gramaziokohler/coding_architecture_fs26_focus_work/Dokumentation/Group A/Booklet_focuswork_2406 Folder/Links/project2.png

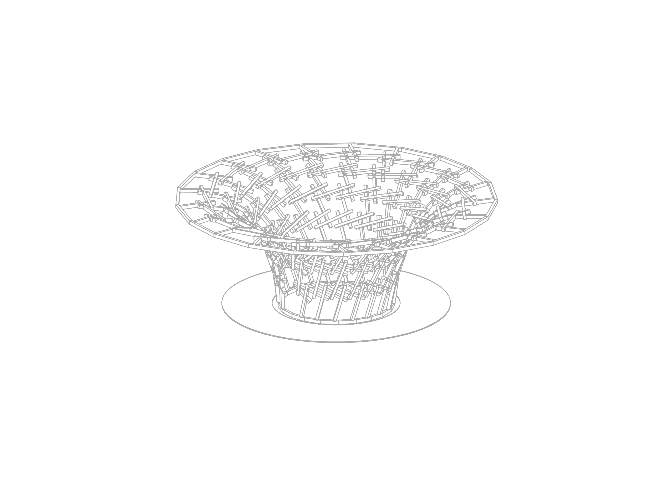
Dokumentation/Group A/Booklet_focuswork_2406 Folder/Links/project2.png
