gramaziokohler/coding_architecture_fs26_focus_work/Dokumentation/Group A/Height.jpg

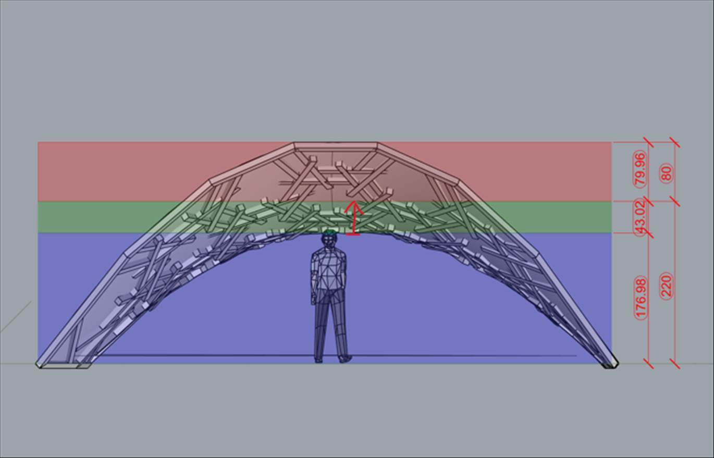
Dokumentation/Group A/Height.jpg
