gramaziokohler/coding_architecture_fs26_focus_work/Dokumentation/Group A/Hexagon Cutting.png

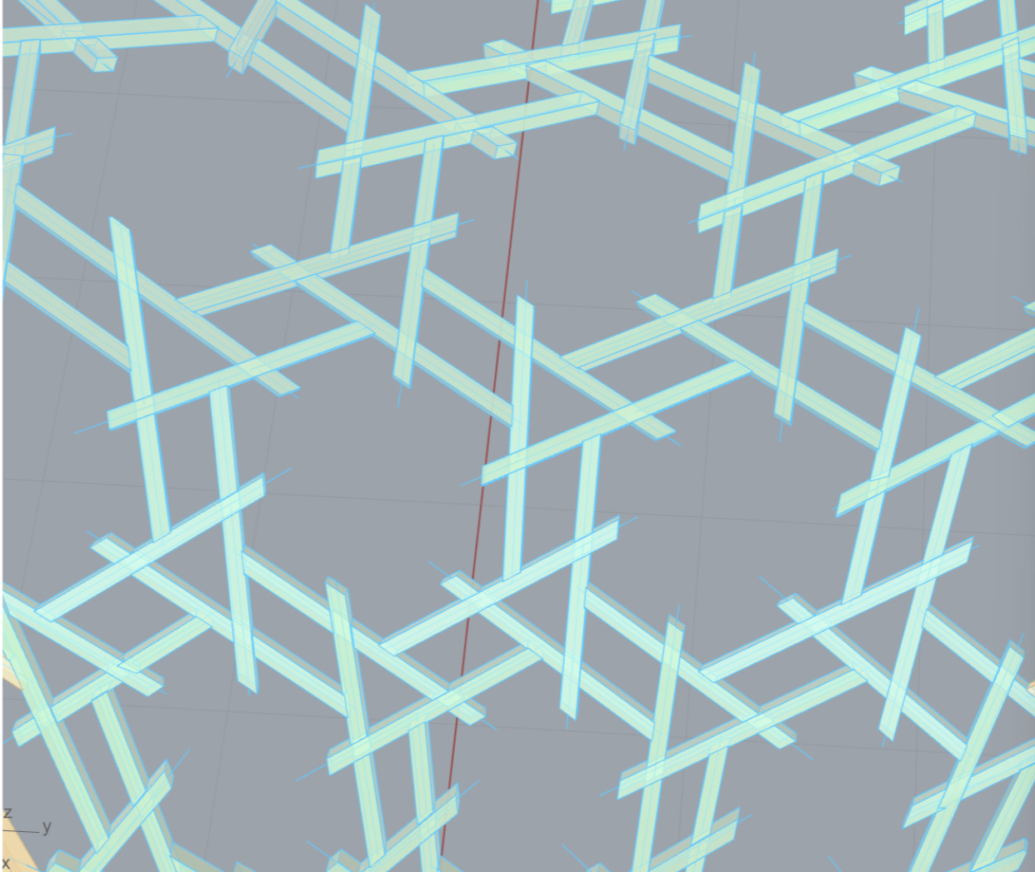
Dokumentation/Group A/Hexagon Cutting.png
