gramaziokohler/coding_architecture_fs26_focus_work/Dokumentation/Group A/Structure_Analysis.png

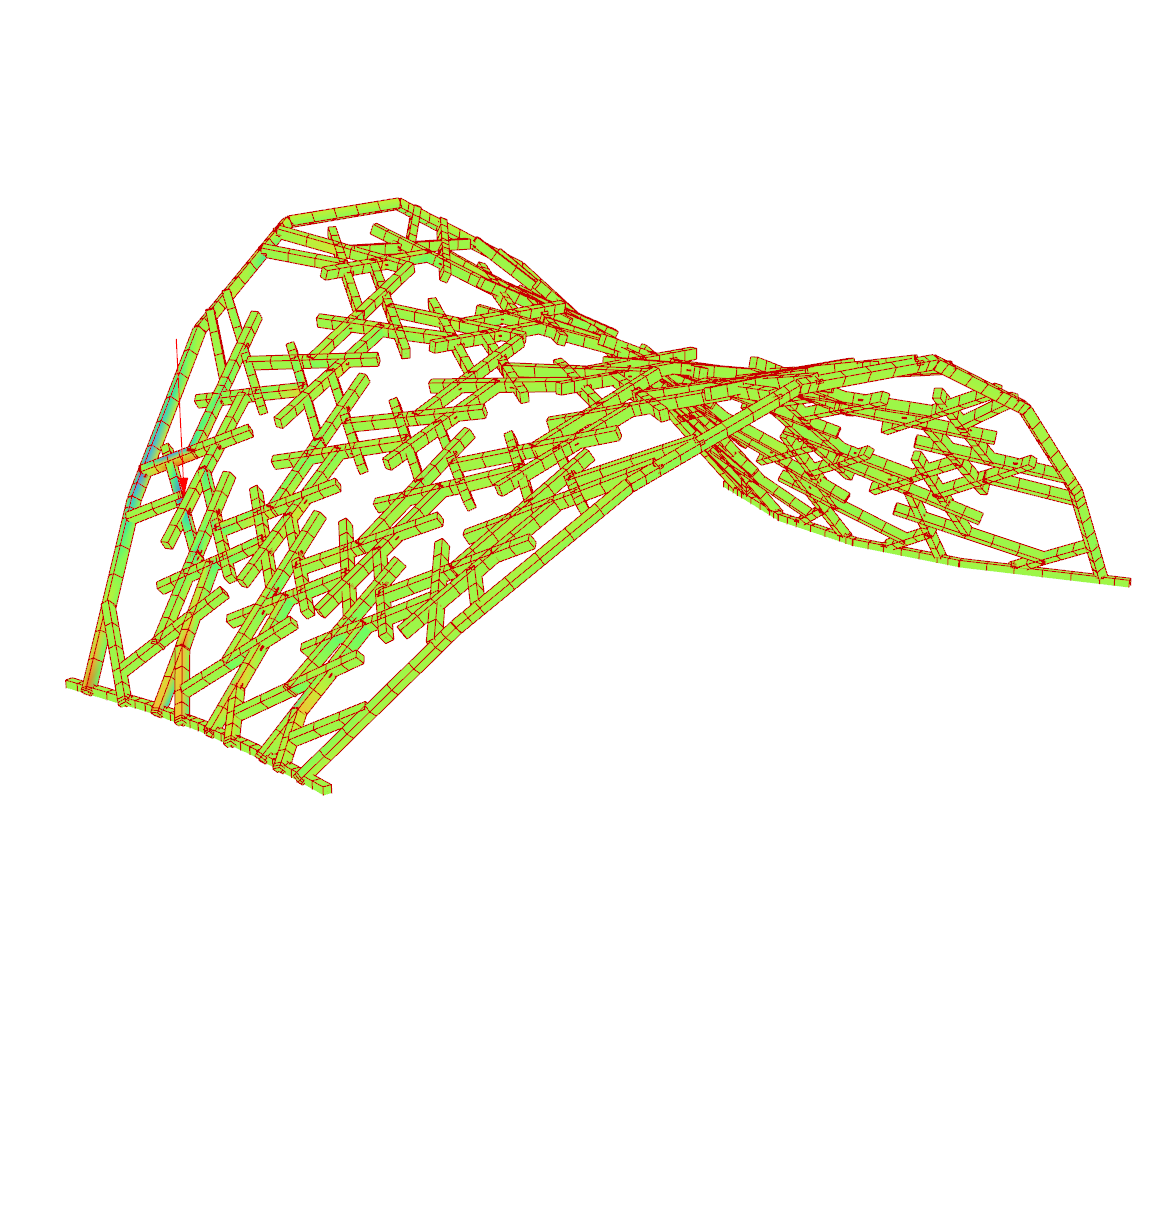
Dokumentation/Group A/Structure_Analysis.png
