gramaziokohler/coding_architecture_fs26_focus_work/Dokumentation/Group B/Screw_processing_2.png

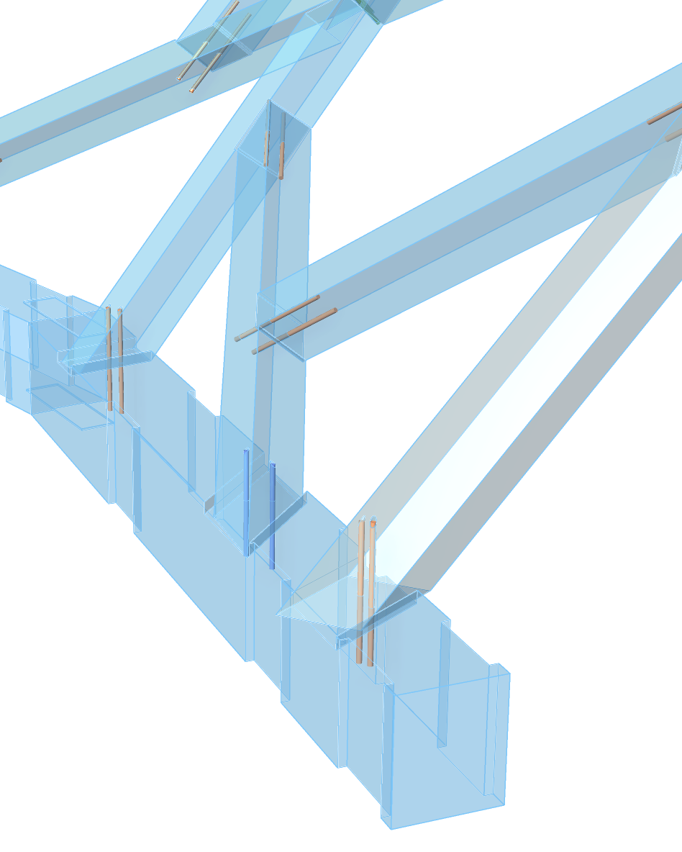
Dokumentation/Group B/Screw_processing_2.png
