gramaziokohler/coding_architecture_fs26_focus_work/Dokumentation/Group B/Screw_processing_6.png

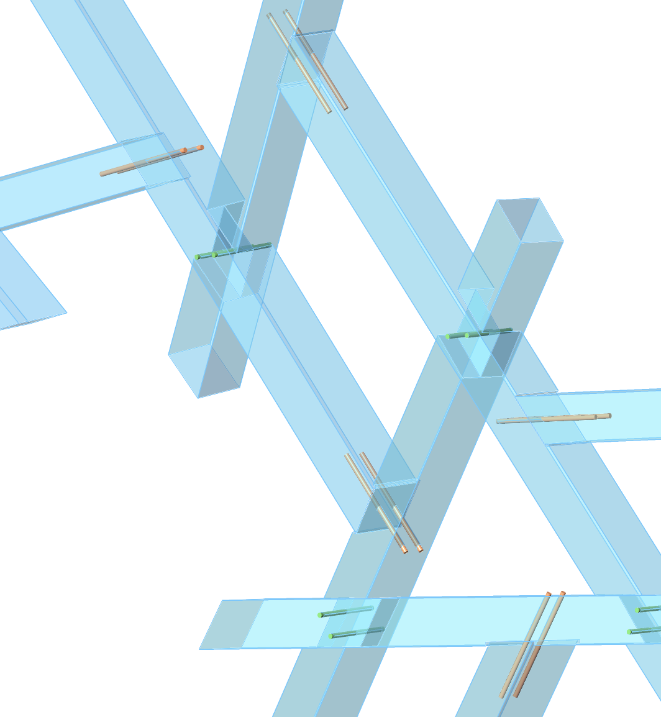
Dokumentation/Group B/Screw_processing_6.png
