gramaziokohler/coding_architecture_fs26_focus_work/Dokumentation/Group B/Screw_processing_fail_2.jpeg

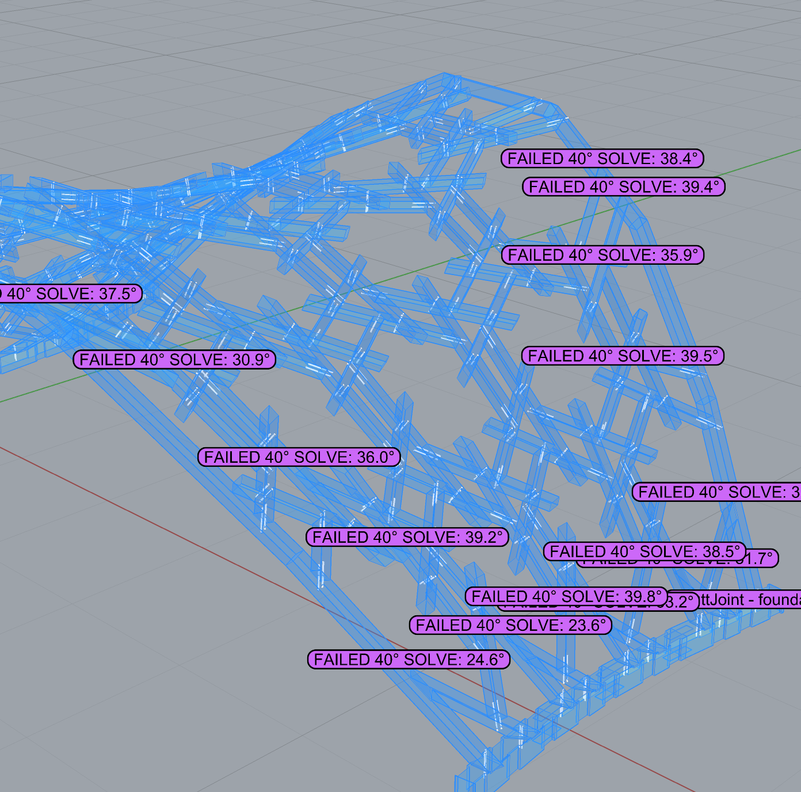
Dokumentation/Group B/Screw_processing_fail_2.jpeg
