gramaziokohler/coding_architecture_fs26_focus_work/Dokumentation/Group B/sketches_joints_2.jpeg

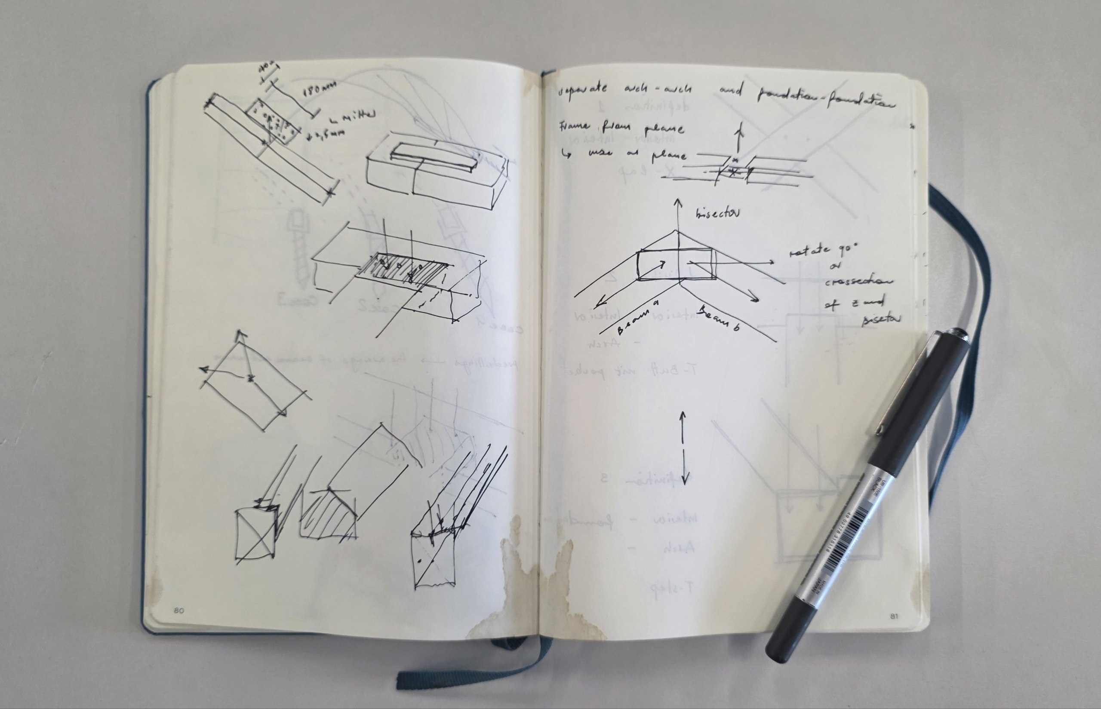
Dokumentation/Group B/sketches_joints_2.jpeg
