gramaziokohler/coding_architecture_fs26_focus_work/working_directory/group_c/bicchieri che brindano.png

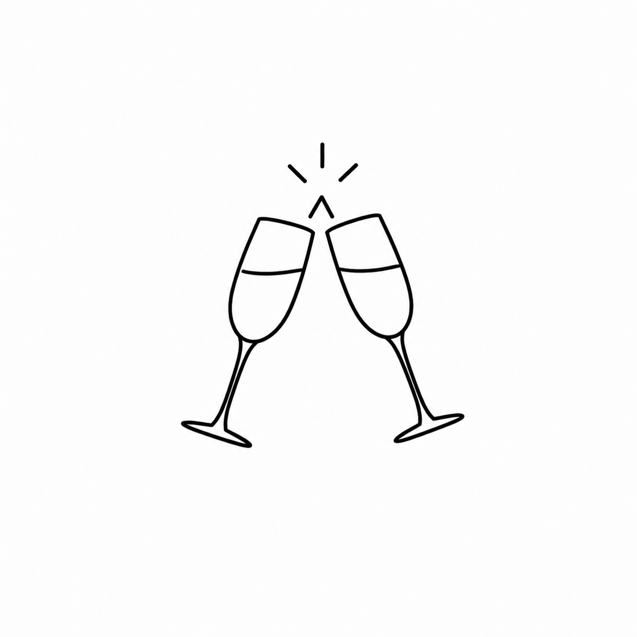
working_directory/group_c/bicchieri che brindano.png
