gramaziokohler/coding_architecture_fs26_focus_work/working_directory/group_d/Assemply_front.png

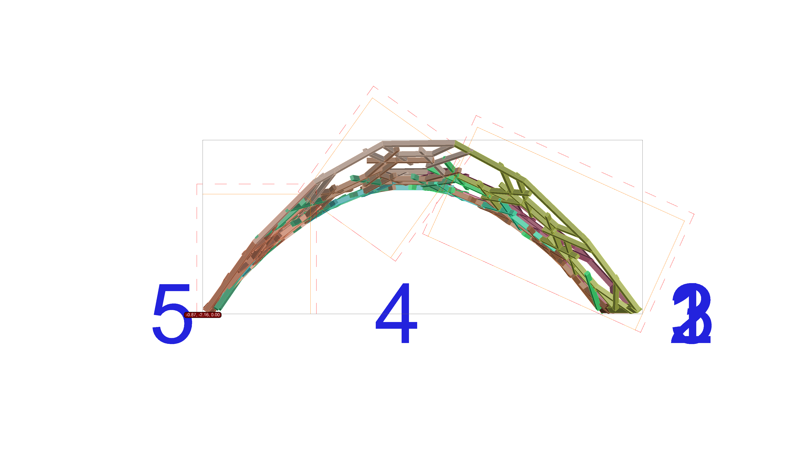
working_directory/group_d/Assemply_front.png
