gramaziokohler/coding_architecture_fs26_focus_work/working_directory/group_d/GardenWires_Diagram.png

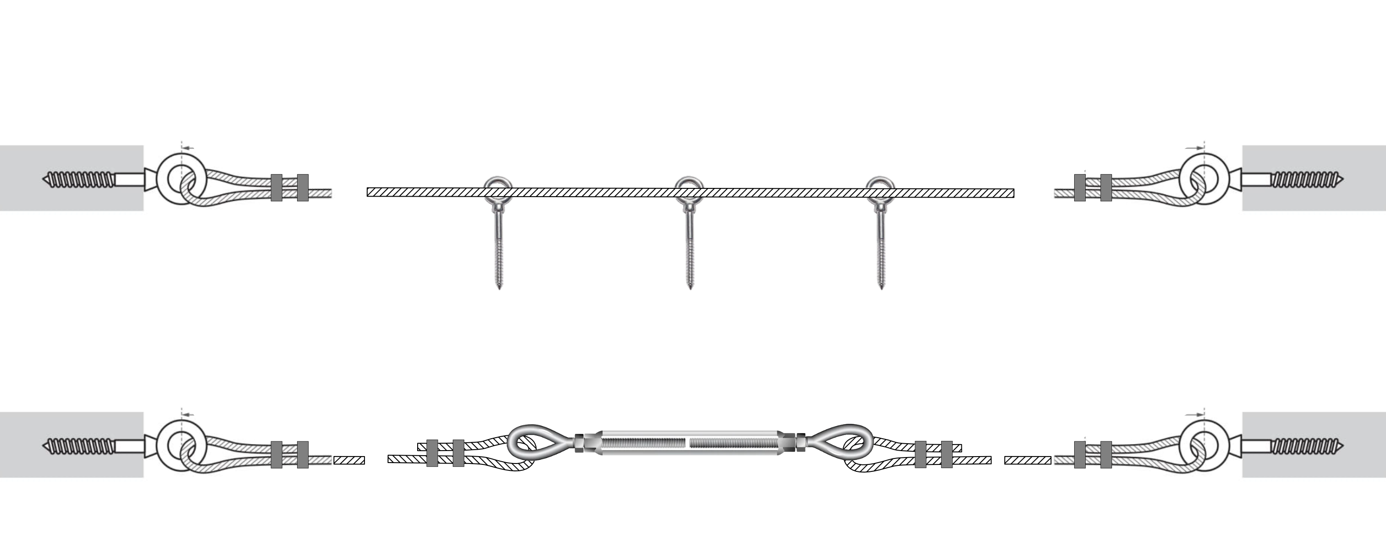
working_directory/group_d/GardenWires_Diagram.png
