gramaziokohler/coding_architecture_fs26_focus_work/working_directory/group_d/STRUCTURE_WITH_NUMBERS_embedded_files/max. 3330.png

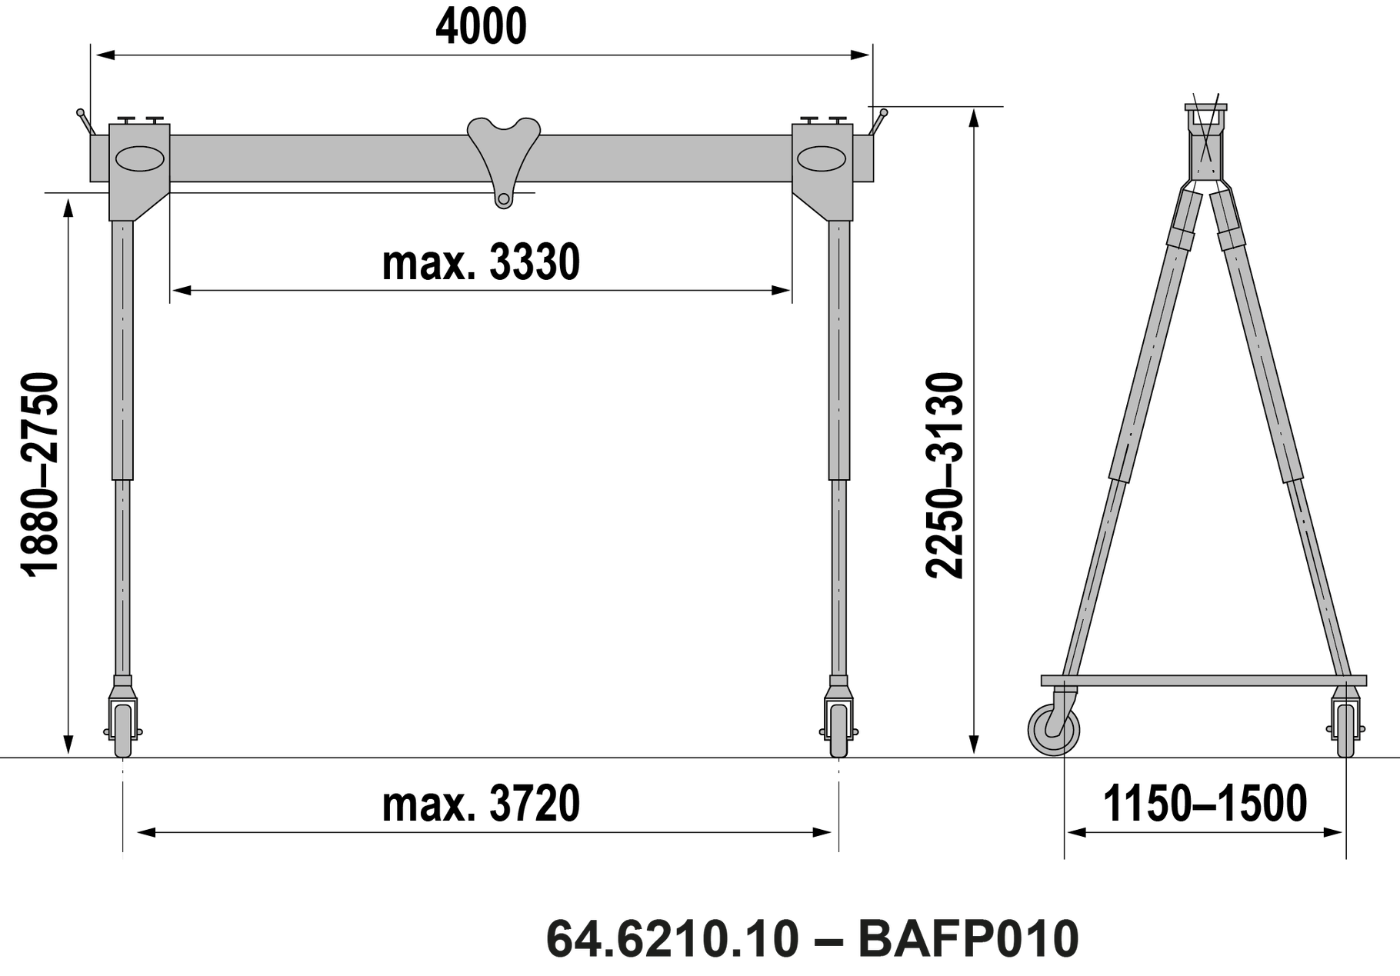
working_directory/group_d/STRUCTURE_WITH_NUMBERS_embedded_files/max. 3330.png
