gramaziokohler/coding_architecture_fs26_focus_work/web_data/beam/a22/a22.stl

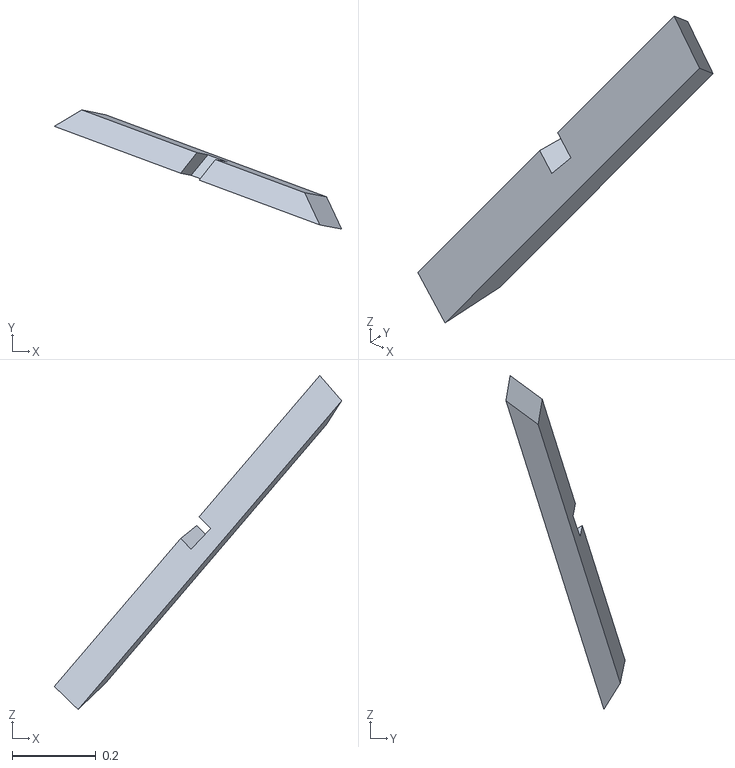
[picture p97: CAD file, 2026-06-04]
web_data/beam/a22/a22.stl
0.687 x 0.285 x 0.798
