gramaziokohler/coding_architecture_fs26_focus_work/web_data/beam/a23/a23.stl

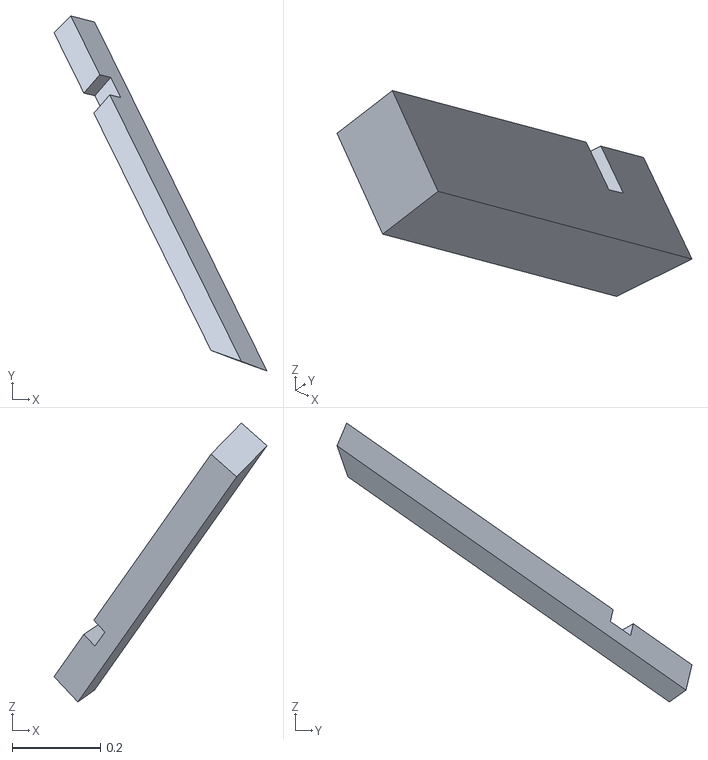
[picture p98: CAD file, 2026-06-04]
web_data/beam/a23/a23.stl
0.484 x 0.806 x 0.633
