gramaziokohler/coding_architecture_fs26_focus_work/web_data/beam/a24/a24.stl

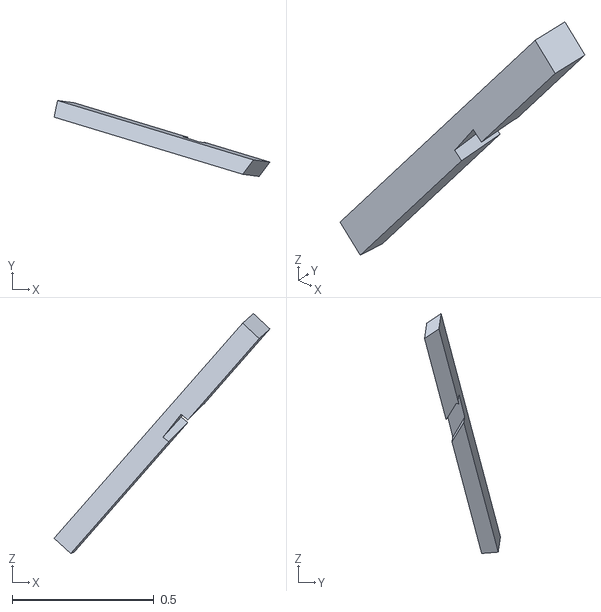
[picture p99: CAD file, 2026-06-04]
web_data/beam/a24/a24.stl
0.761 x 0.268 x 0.846
