gramaziokohler/coding_architecture_fs26_focus_work/web_data/beam/a25/a25.stl

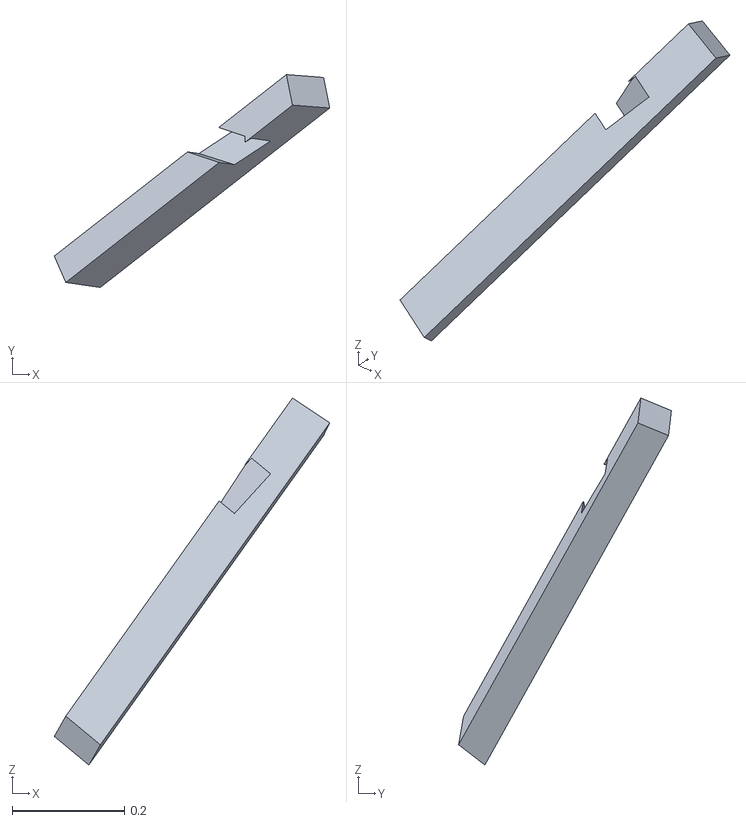
[picture p100: CAD file, 2026-06-04]
web_data/beam/a25/a25.stl
0.491 x 0.38 x 0.654
