gramaziokohler/coding_architecture_fs26_focus_work/web_data/beam/a26/a26.stl

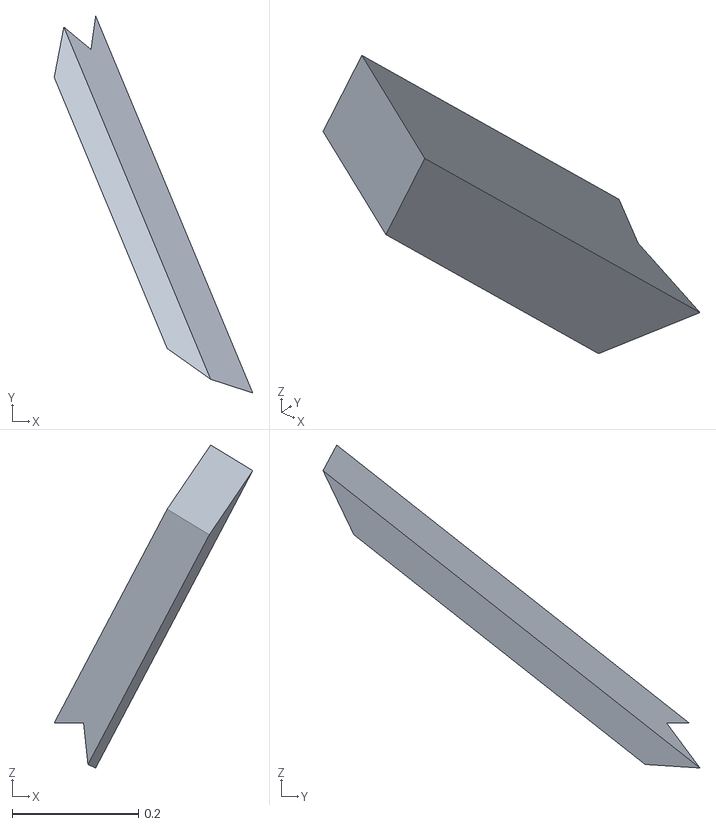
[picture p101: CAD file, 2026-06-04]
web_data/beam/a26/a26.stl
0.315 x 0.597 x 0.512
