gramaziokohler/coding_architecture_fs26_focus_work/web_data/beam/a27/a27.stl

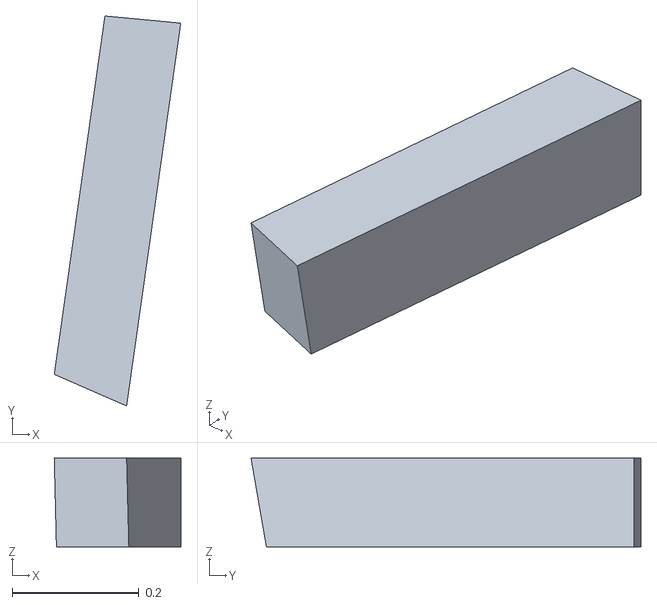
[picture p102: CAD file, 2026-06-04]
web_data/beam/a27/a27.stl
0.2 x 0.615 x 0.14
