gramaziokohler/coding_architecture_fs26_focus_work/web_data/beam/a28/a28.stl

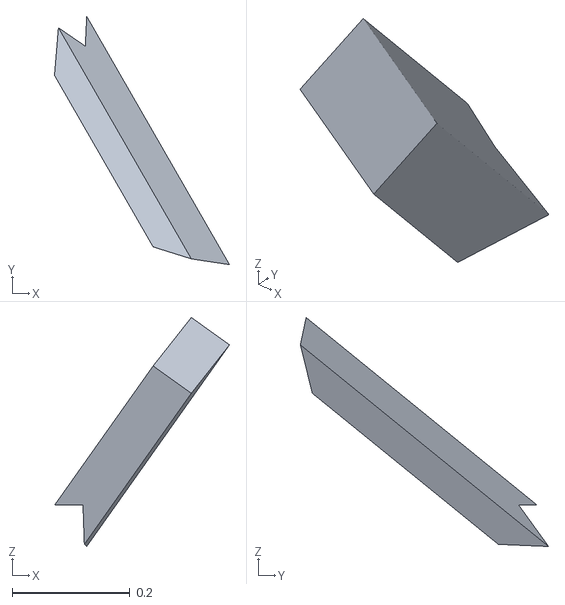
[picture p103: CAD file, 2026-06-04]
web_data/beam/a28/a28.stl
0.297 x 0.421 x 0.389
