gramaziokohler/coding_architecture_fs26_focus_work/web_data/beam/a29/a29.stl

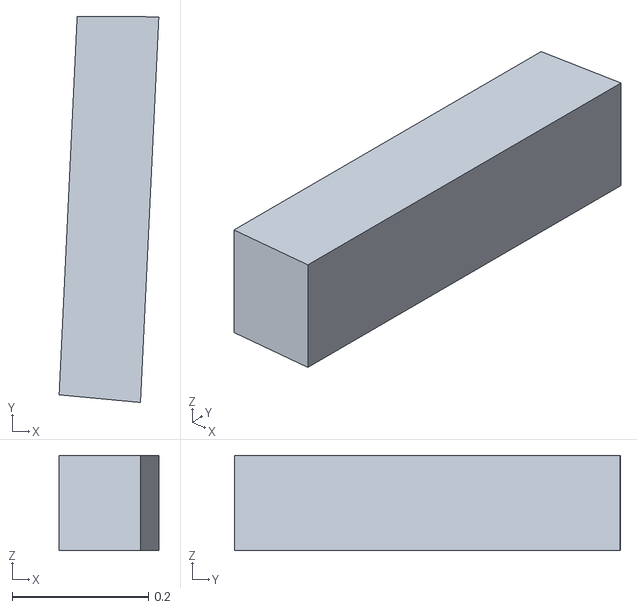
[picture p104: CAD file, 2026-06-04]
web_data/beam/a29/a29.stl
0.147 x 0.567 x 0.14
