gramaziokohler/coding_architecture_fs26_focus_work/web_data/beam/a3/a3.stl

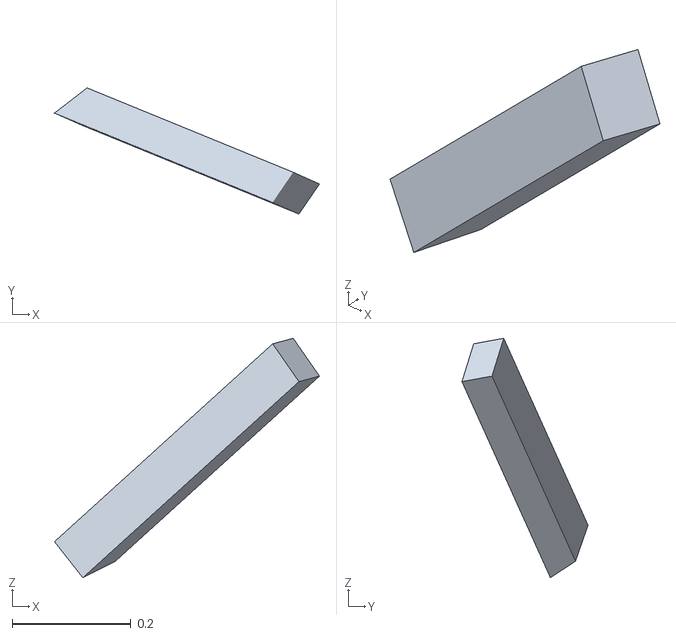
[picture p105: CAD file, 2026-06-04]
web_data/beam/a3/a3.stl
0.447 x 0.213 x 0.403
