gramaziokohler/coding_architecture_fs26_focus_work/web_data/beam/a30/a30.stl

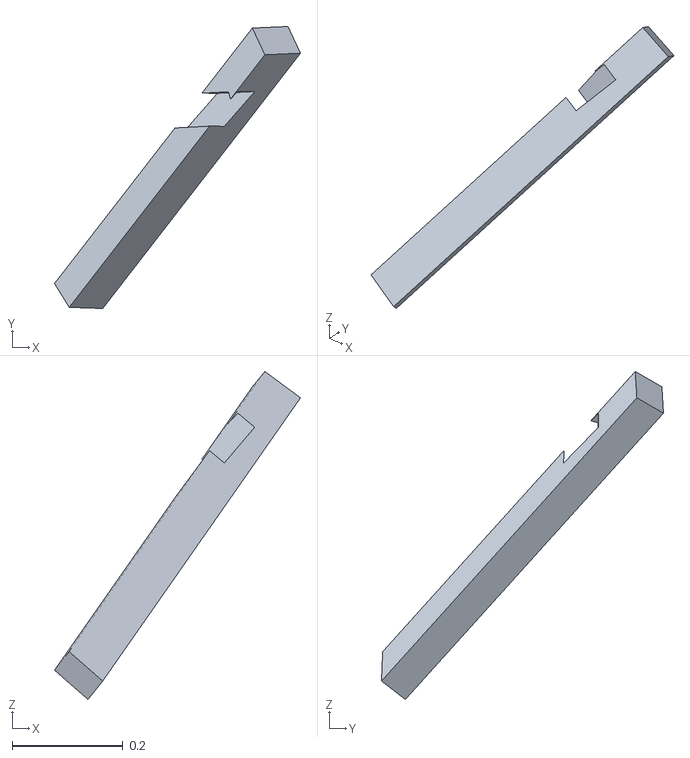
[picture p106: CAD file, 2026-06-04]
web_data/beam/a30/a30.stl
0.444 x 0.509 x 0.592
