gramaziokohler/coding_architecture_fs26_focus_work/web_data/beam/a31/a31.stl

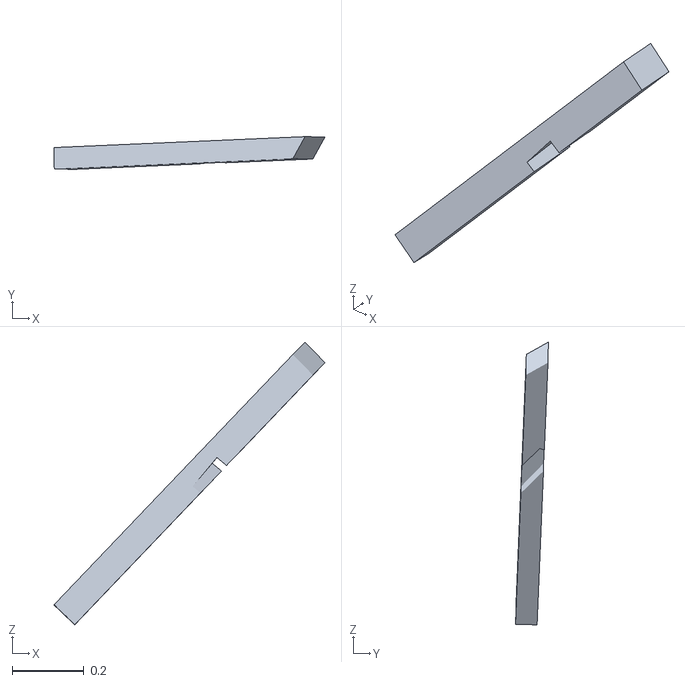
[picture p107: CAD file, 2026-06-04]
web_data/beam/a31/a31.stl
0.756 x 0.0914 x 0.789
