gramaziokohler/coding_architecture_fs26_focus_work/web_data/beam/a32/a32.stl

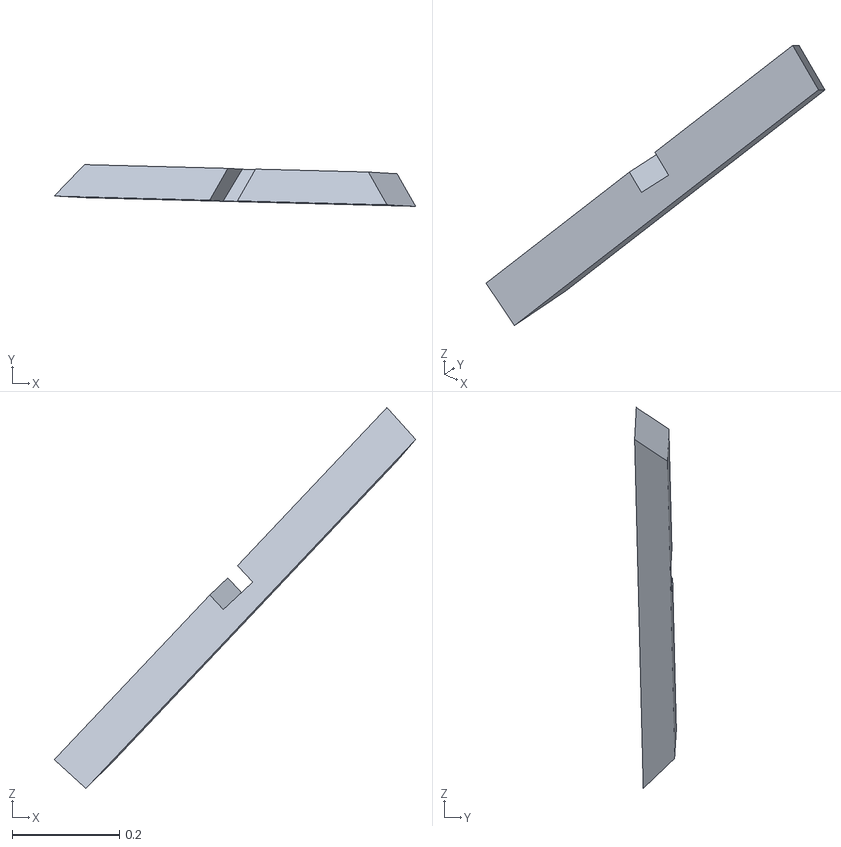
[picture p108: CAD file, 2026-06-04]
web_data/beam/a32/a32.stl
0.674 x 0.078 x 0.711
