gramaziokohler/coding_architecture_fs26_focus_work/web_data/beam/a33/a33.stl

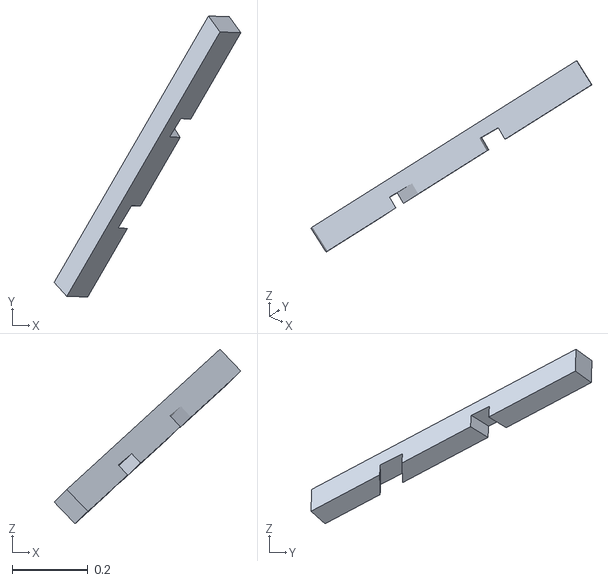
[picture p109: CAD file, 2026-06-04]
web_data/beam/a33/a33.stl
0.494 x 0.743 x 0.462
