gramaziokohler/coding_architecture_fs26_focus_work/web_data/beam/a34/a34.stl

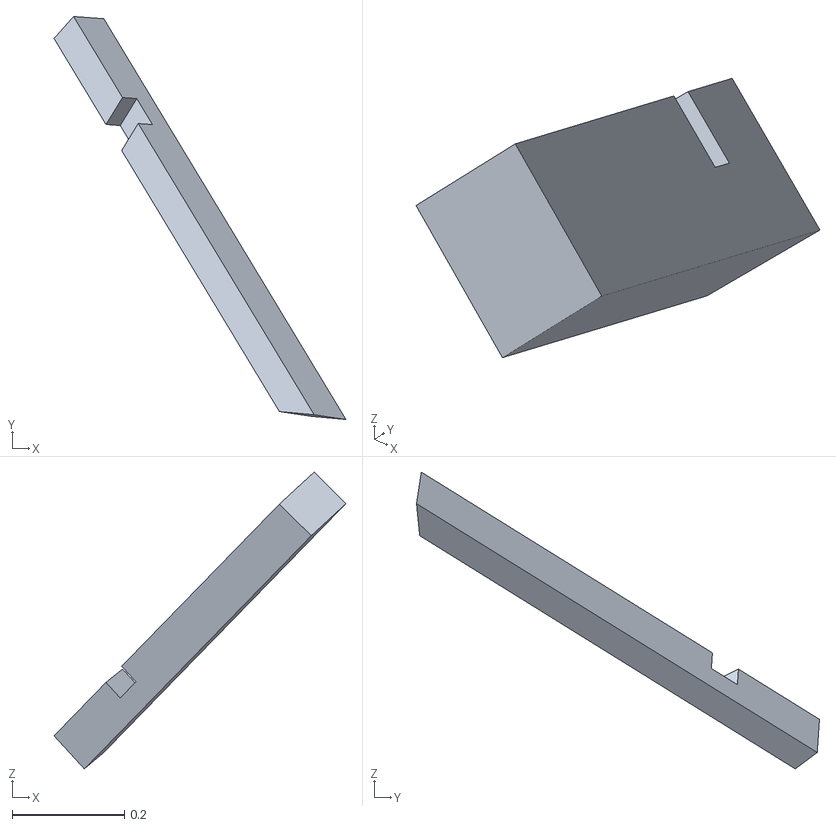
[picture p110: CAD file, 2026-06-04]
web_data/beam/a34/a34.stl
0.52 x 0.717 x 0.528
