gramaziokohler/coding_architecture_fs26_focus_work/web_data/beam/a35/a35.stl

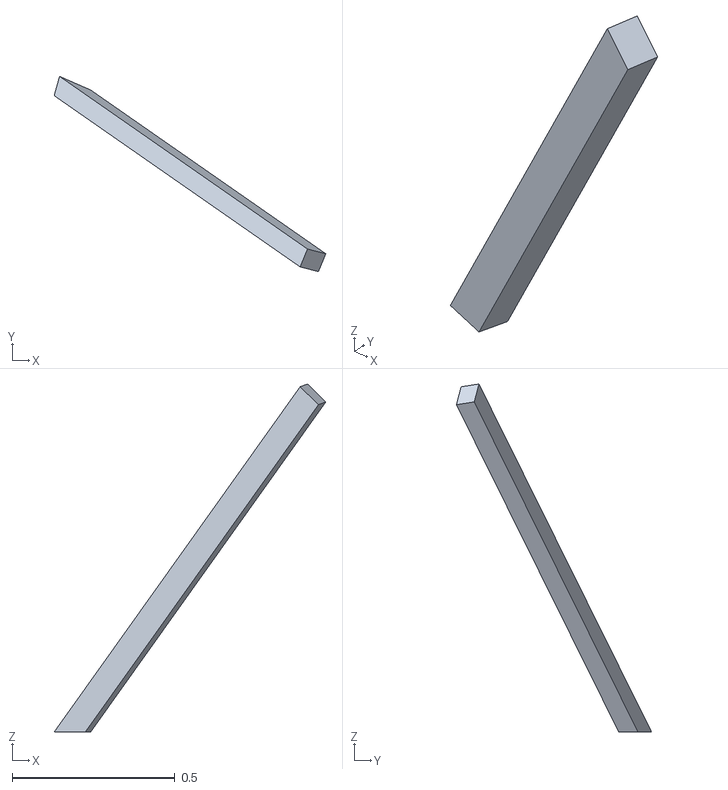
[picture p111: CAD file, 2026-06-04]
web_data/beam/a35/a35.stl
0.835 x 0.6 x 1.07
