gramaziokohler/coding_architecture_fs26_focus_work/web_data/beam/a36/a36.stl

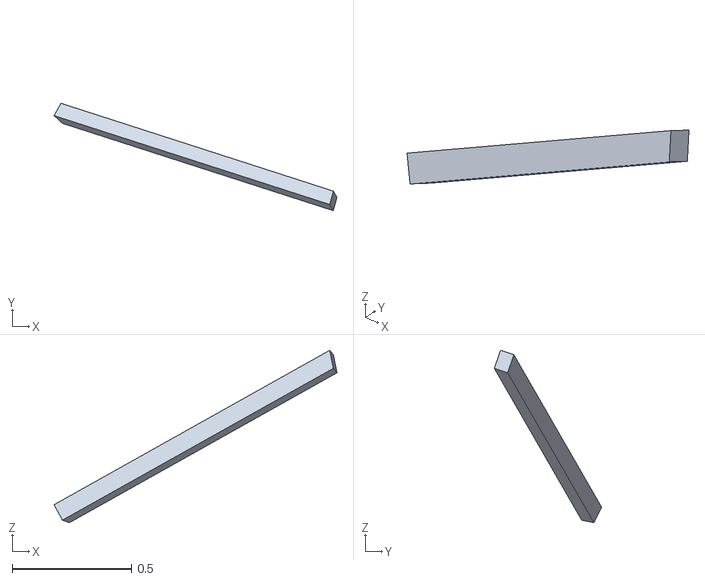
[picture p112: CAD file, 2026-06-04]
web_data/beam/a36/a36.stl
1.19 x 0.45 x 0.723
