gramaziokohler/coding_architecture_fs26_focus_work/web_data/beam/a4/a4.stl

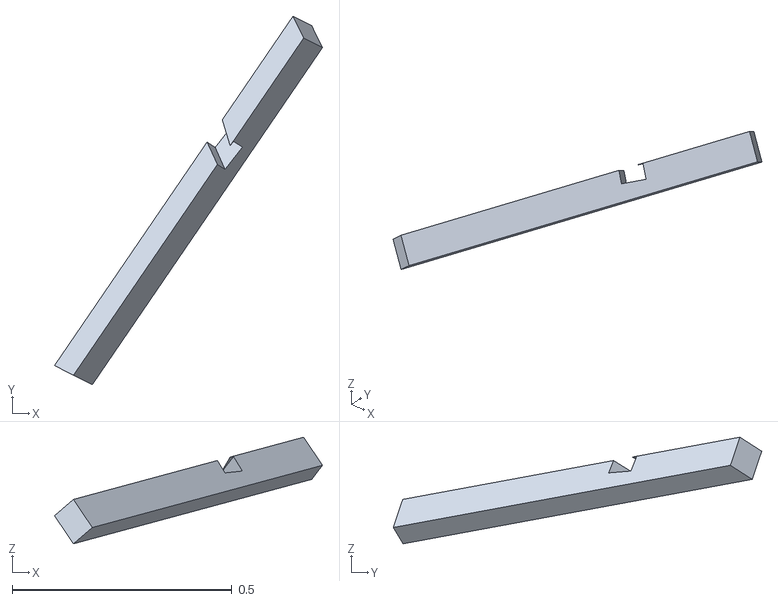
[picture p113: CAD file, 2026-06-04]
web_data/beam/a4/a4.stl
0.61 x 0.839 x 0.243
