gramaziokohler/coding_architecture_fs26_focus_work/web_data/beam/a5/a5.stl

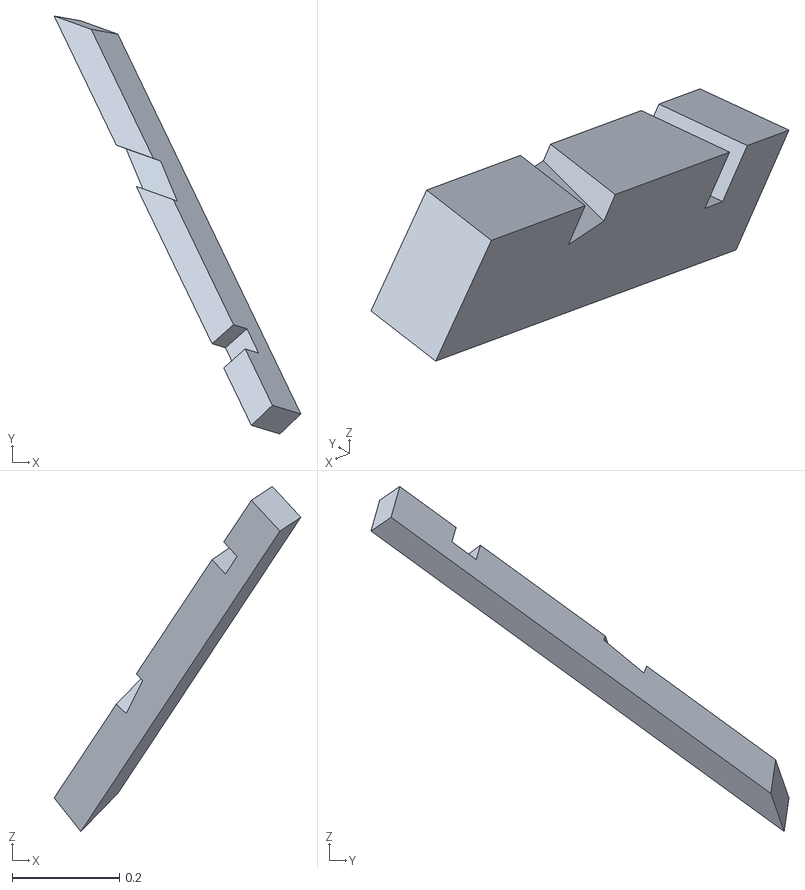
[picture p114: CAD file, 2026-06-04]
web_data/beam/a5/a5.stl
0.461 x 0.781 x 0.644
