gramaziokohler/coding_architecture_fs26_focus_work/web_data/beam/a6/a6.stl

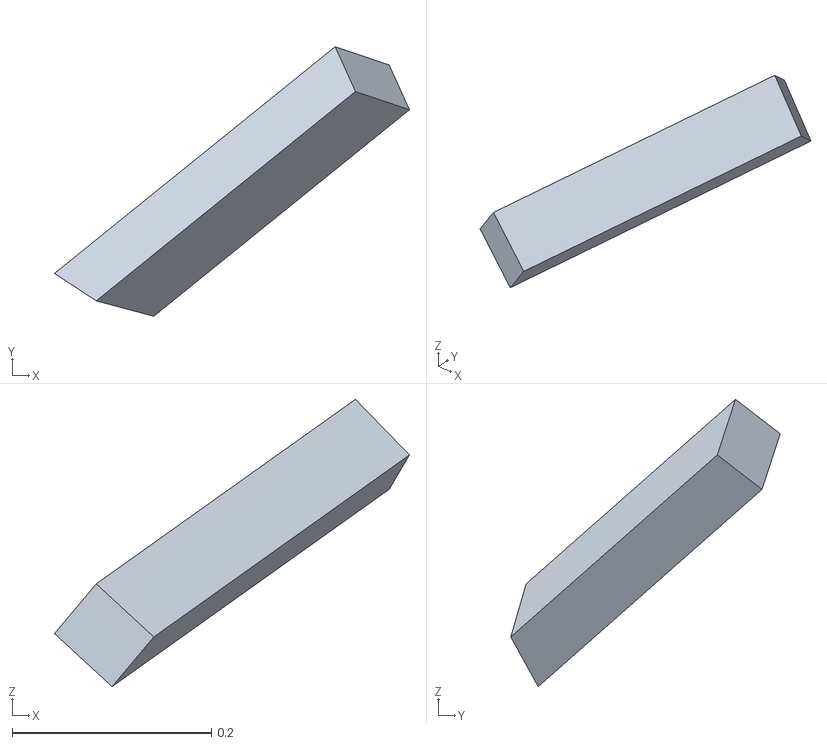
[picture p115: CAD file, 2026-06-04]
web_data/beam/a6/a6.stl
0.357 x 0.271 x 0.289
