gramaziokohler/coding_architecture_fs26_focus_work/web_data/beam/a7/a7.stl

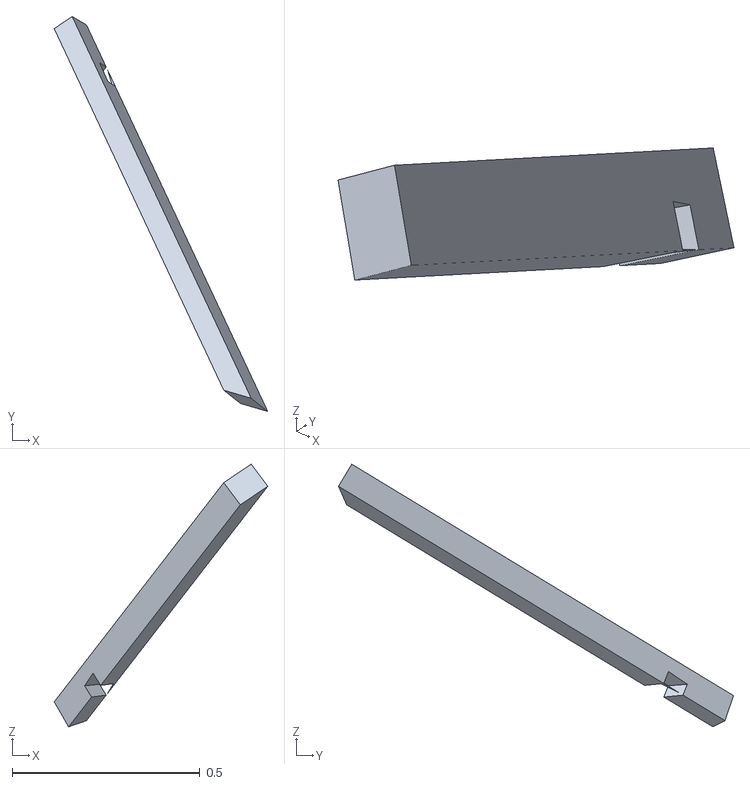
[picture p116: CAD file, 2026-06-04]
web_data/beam/a7/a7.stl
0.568 x 1.05 x 0.699
