gramaziokohler/coding_architecture_fs26_focus_work/web_data/beam/a8/a8.stl

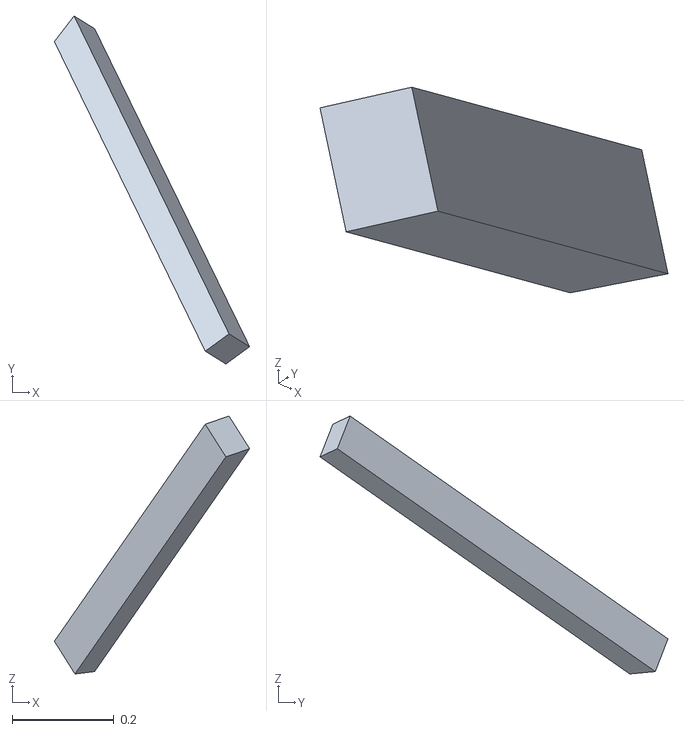
[picture p117: CAD file, 2026-06-04]
web_data/beam/a8/a8.stl
0.384 x 0.684 x 0.507
