gramaziokohler/coding_architecture_fs26_focus_work/web_data/beam/a9/a9.stl

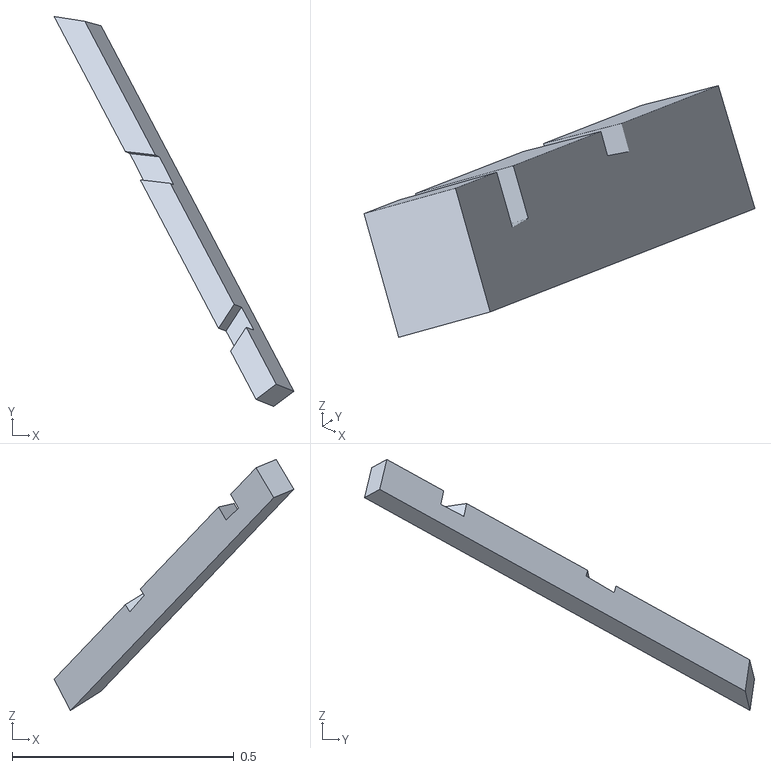
[picture p118: CAD file, 2026-06-04]
web_data/beam/a9/a9.stl
0.541 x 0.88 x 0.567
