gramaziokohler/coding_architecture_fs26_focus_work/web_data/beam/b1/b1.stl

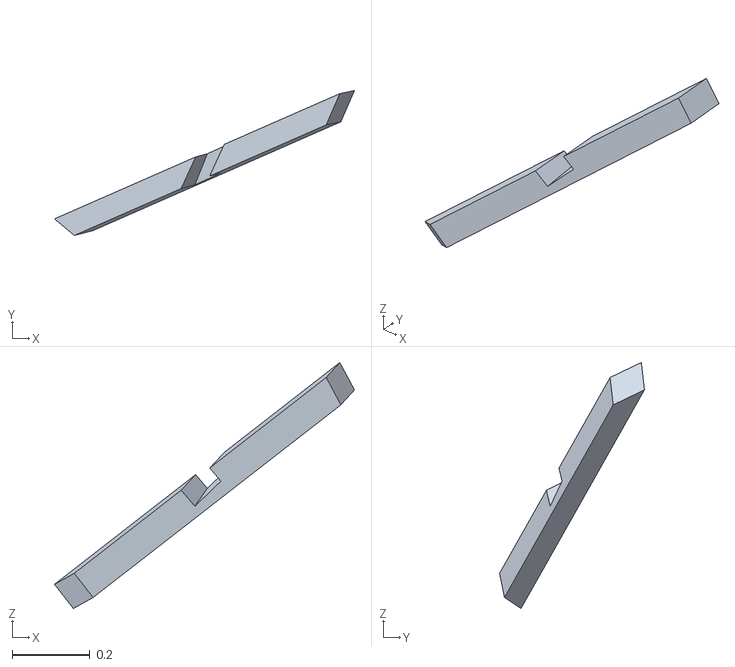
[picture p119: CAD file, 2026-06-04]
web_data/beam/b1/b1.stl
0.774 x 0.374 x 0.635
