gramaziokohler/coding_architecture_fs26_focus_work/web_data/beam/b10/b10.stl

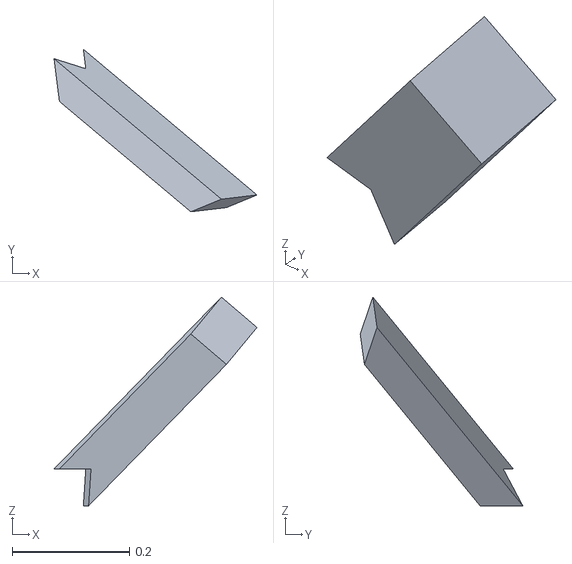
[picture p120: CAD file, 2026-06-04]
web_data/beam/b10/b10.stl
0.346 x 0.277 x 0.356
