gramaziokohler/coding_architecture_fs26_focus_work/web_data/beam/b11/b11.stl

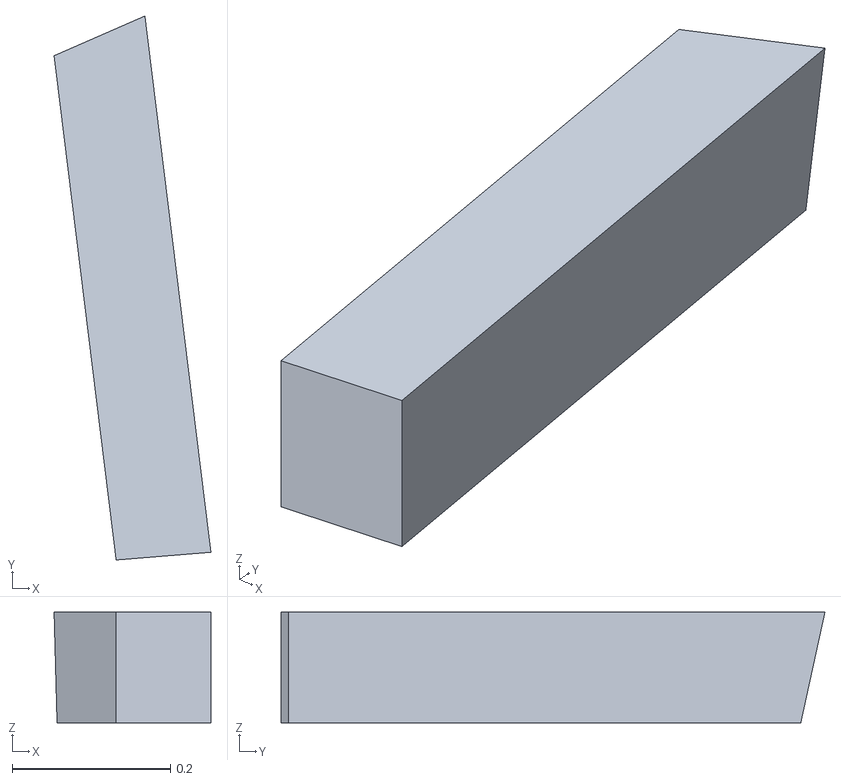
[picture p121: CAD file, 2026-06-04]
web_data/beam/b11/b11.stl
0.198 x 0.687 x 0.14
