gramaziokohler/coding_architecture_fs26_focus_work/web_data/beam/b12/b12.stl

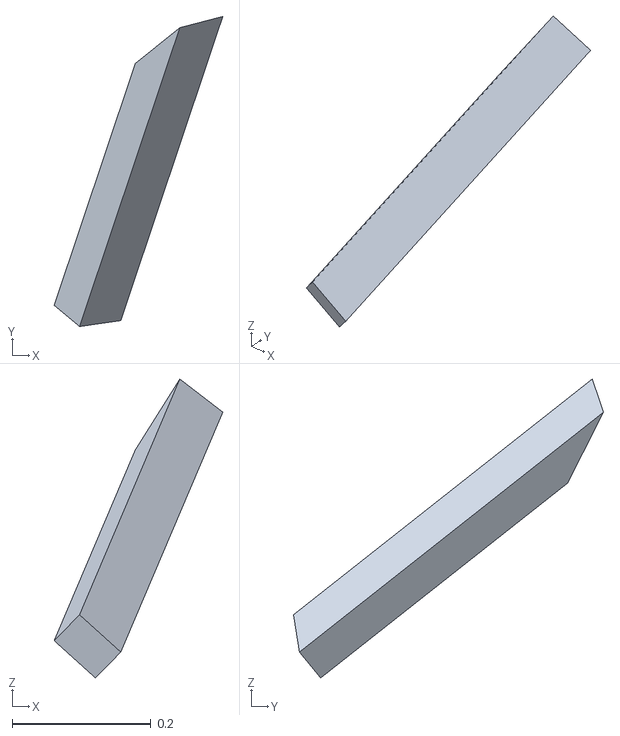
[picture p122: CAD file, 2026-06-04]
web_data/beam/b12/b12.stl
0.243 x 0.447 x 0.431
