gramaziokohler/coding_architecture_fs26_focus_work/web_data/beam/b13/b13.stl

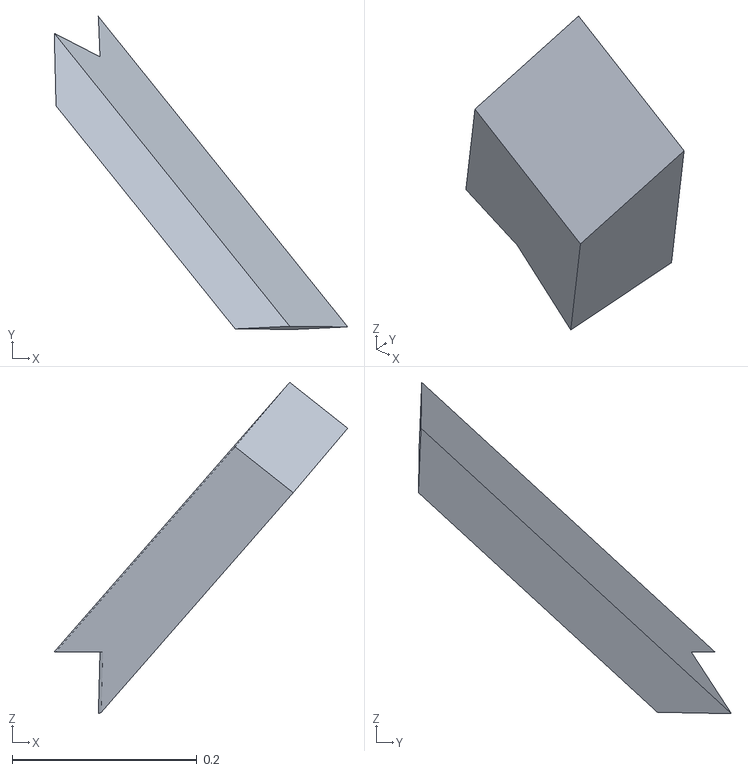
[picture p123: CAD file, 2026-06-04]
web_data/beam/b13/b13.stl
0.317 x 0.338 x 0.358
