gramaziokohler/coding_architecture_fs26_focus_work/web_data/beam/b14/b14.stl

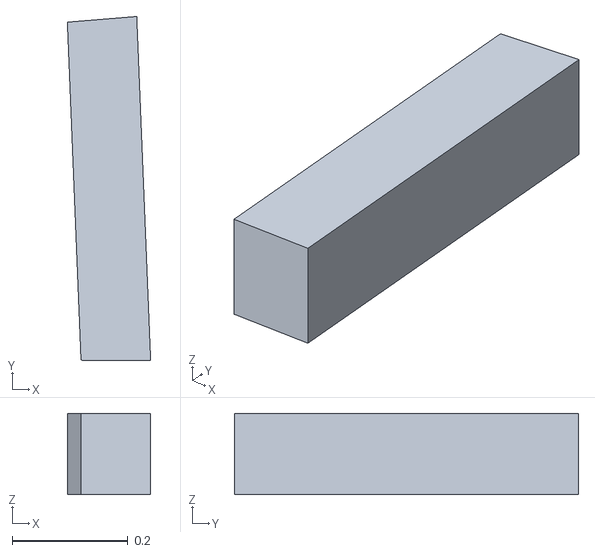
[picture p124: CAD file, 2026-06-04]
web_data/beam/b14/b14.stl
0.144 x 0.593 x 0.14
