gramaziokohler/coding_architecture_fs26_focus_work/web_data/beam/b15/b15.stl

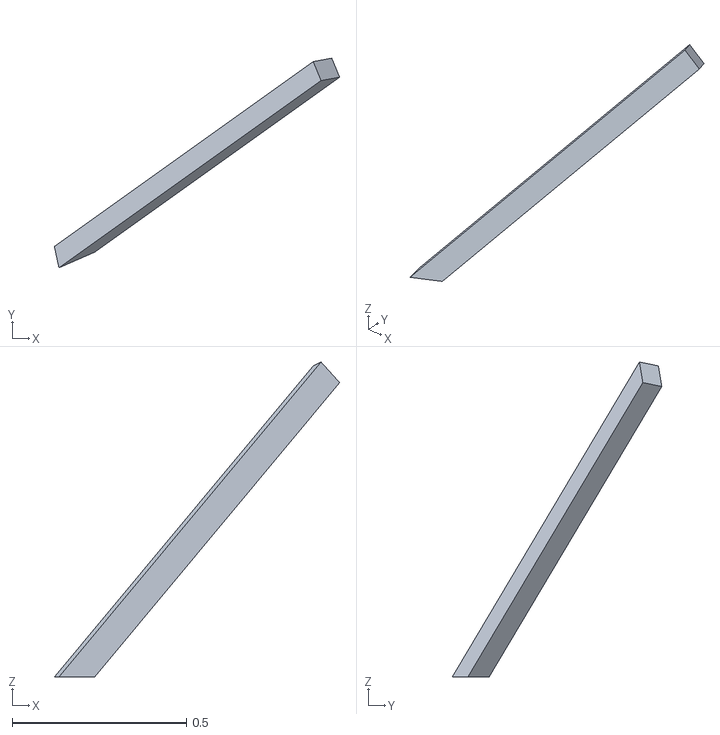
[picture p125: CAD file, 2026-06-04]
web_data/beam/b15/b15.stl
0.819 x 0.602 x 0.904
