gramaziokohler/coding_architecture_fs26_focus_work/web_data/beam/b16/b16.stl

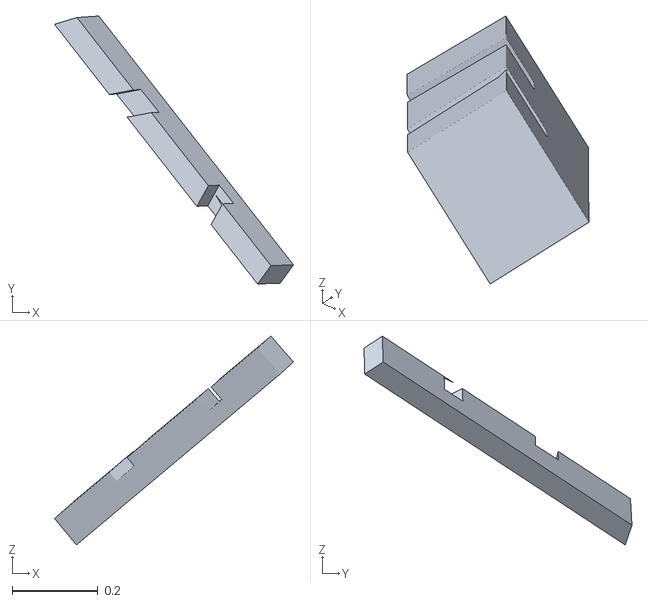
[picture p126: CAD file, 2026-06-04]
web_data/beam/b16/b16.stl
0.556 x 0.624 x 0.486
