gramaziokohler/coding_architecture_fs26_focus_work/web_data/beam/b17/b17.stl

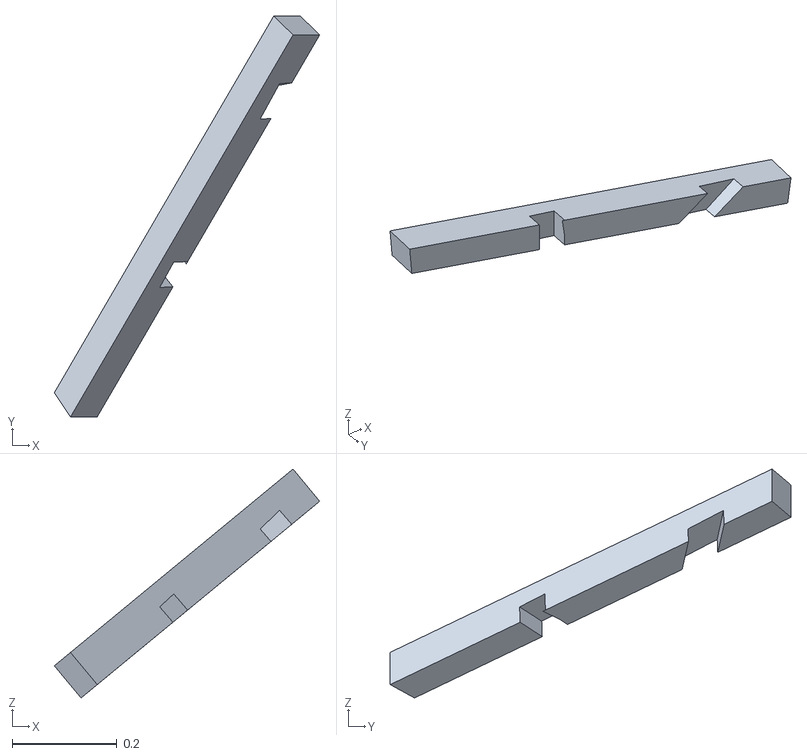
[picture p127: CAD file, 2026-06-04]
web_data/beam/b17/b17.stl
0.507 x 0.767 x 0.438
