gramaziokohler/coding_architecture_fs26_focus_work/web_data/beam/b18/b18.stl

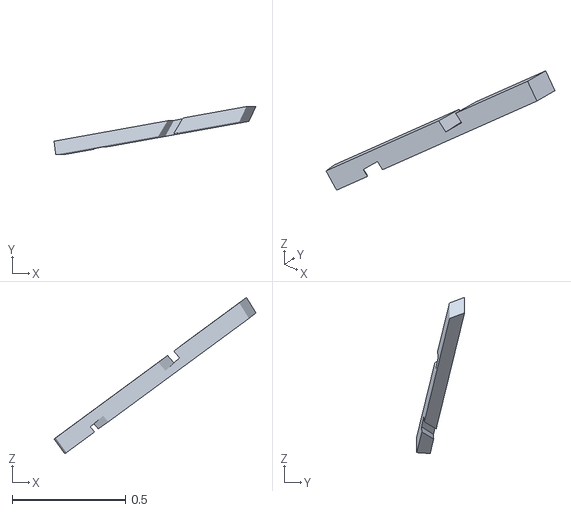
[picture p128: CAD file, 2026-06-04]
web_data/beam/b18/b18.stl
0.893 x 0.213 x 0.69
