gramaziokohler/coding_architecture_fs26_focus_work/web_data/beam/b19/b19.stl

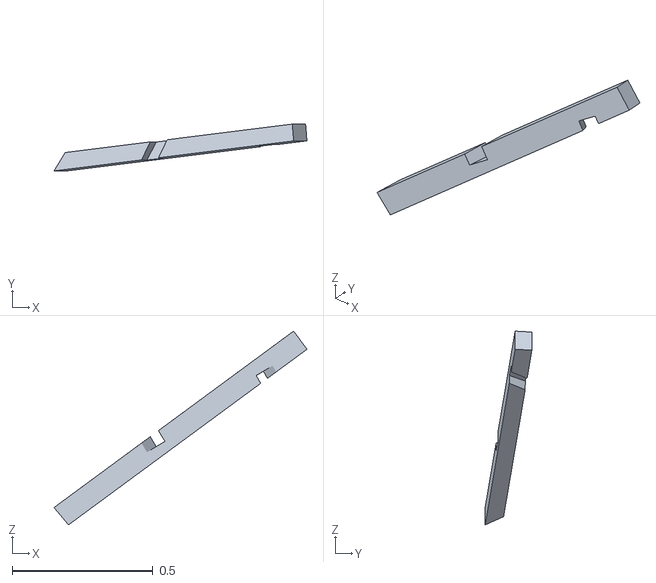
[picture p129: CAD file, 2026-06-04]
web_data/beam/b19/b19.stl
0.898 x 0.166 x 0.688
