gramaziokohler/coding_architecture_fs26_focus_work/web_data/beam/b2/b2.stl

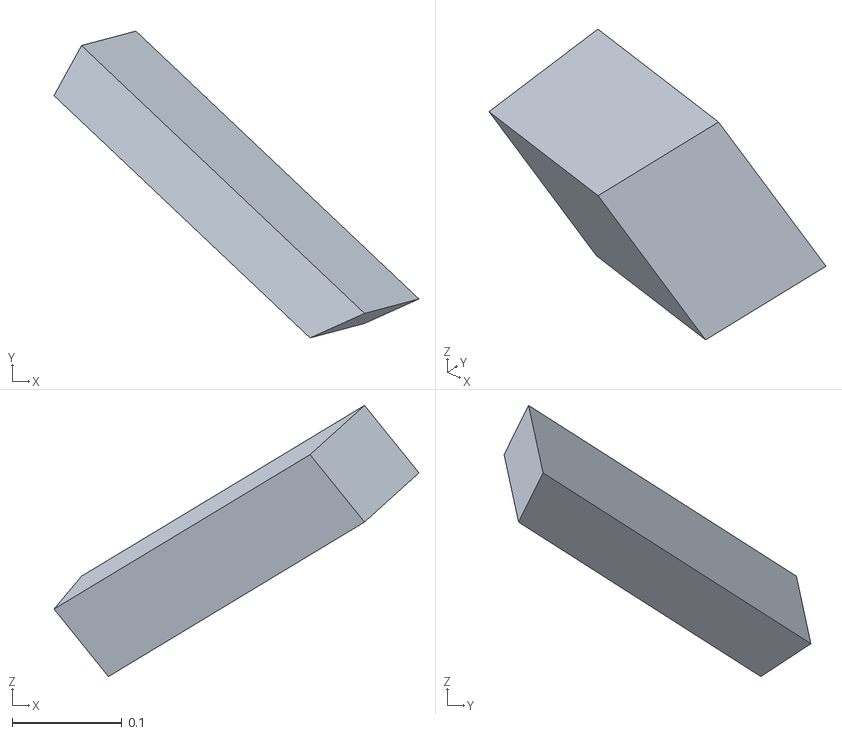
[picture p130: CAD file, 2026-06-04]
web_data/beam/b2/b2.stl
0.332 x 0.279 x 0.247
