gramaziokohler/coding_architecture_fs26_focus_work/web_data/beam/b20/b20.stl

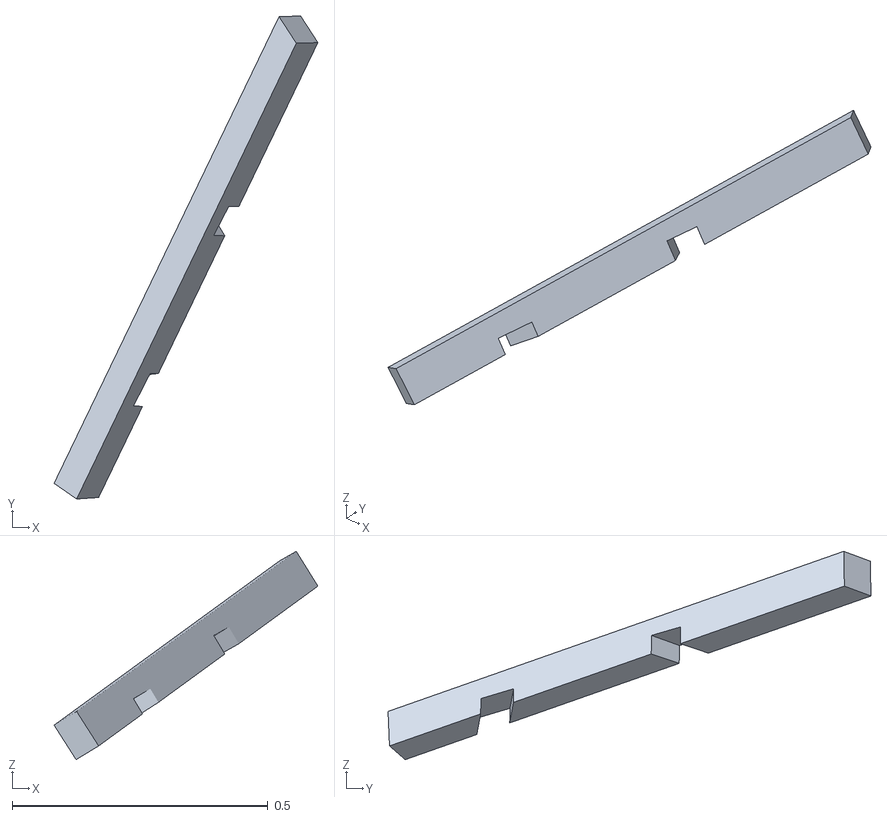
[picture p131: CAD file, 2026-06-04]
web_data/beam/b20/b20.stl
0.516 x 0.944 x 0.407
