gramaziokohler/coding_architecture_fs26_focus_work/web_data/beam/b21/b21.stl

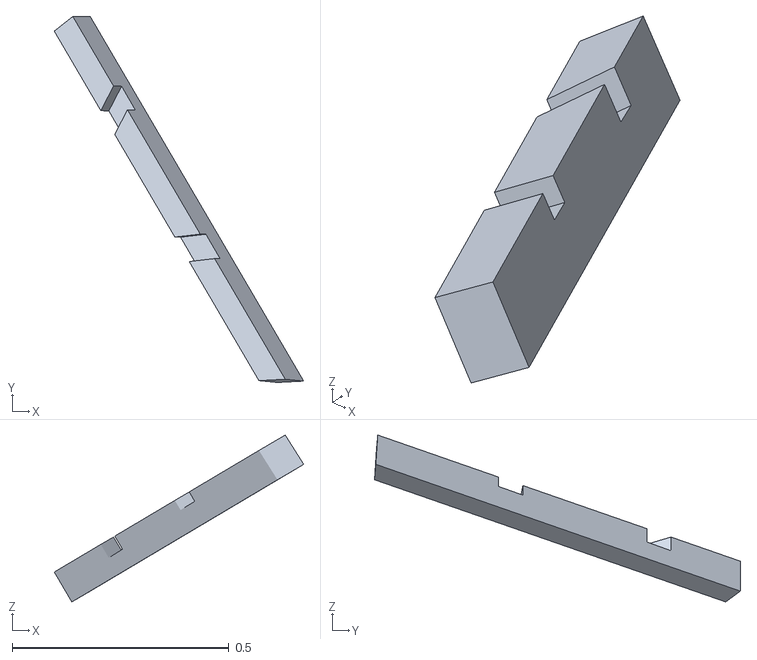
[picture p132: CAD file, 2026-06-04]
web_data/beam/b21/b21.stl
0.576 x 0.845 x 0.385
