gramaziokohler/coding_architecture_fs26_focus_work/web_data/beam/b22/b22.stl

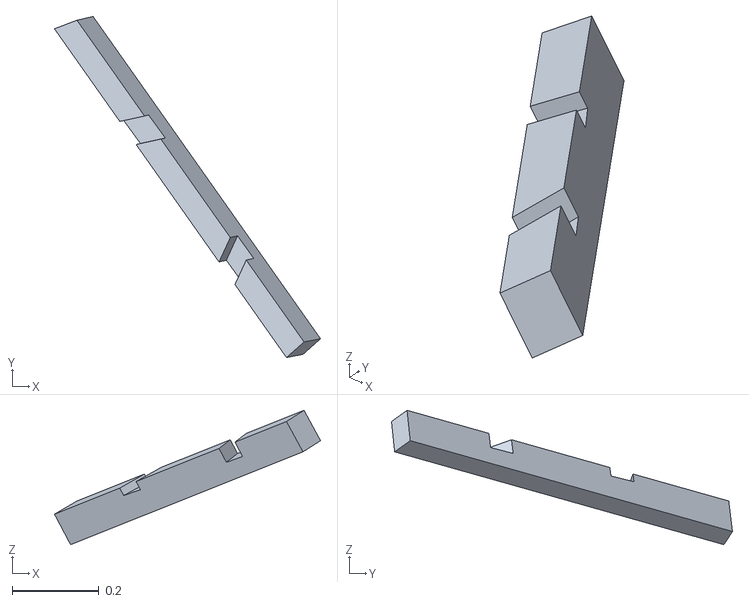
[picture p133: CAD file, 2026-06-04]
web_data/beam/b22/b22.stl
0.614 x 0.786 x 0.31
