gramaziokohler/coding_architecture_fs26_focus_work/web_data/beam/b23/b23.stl

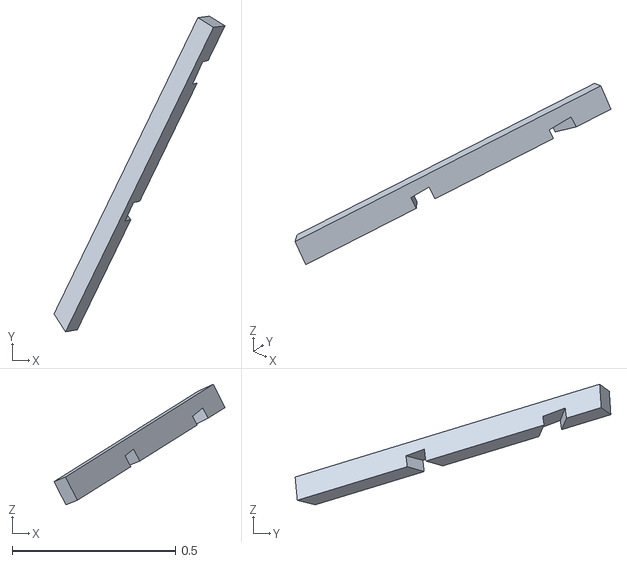
[picture p134: CAD file, 2026-06-04]
web_data/beam/b23/b23.stl
0.523 x 0.966 x 0.369
