gramaziokohler/coding_architecture_fs26_focus_work/web_data/beam/b24/b24.stl

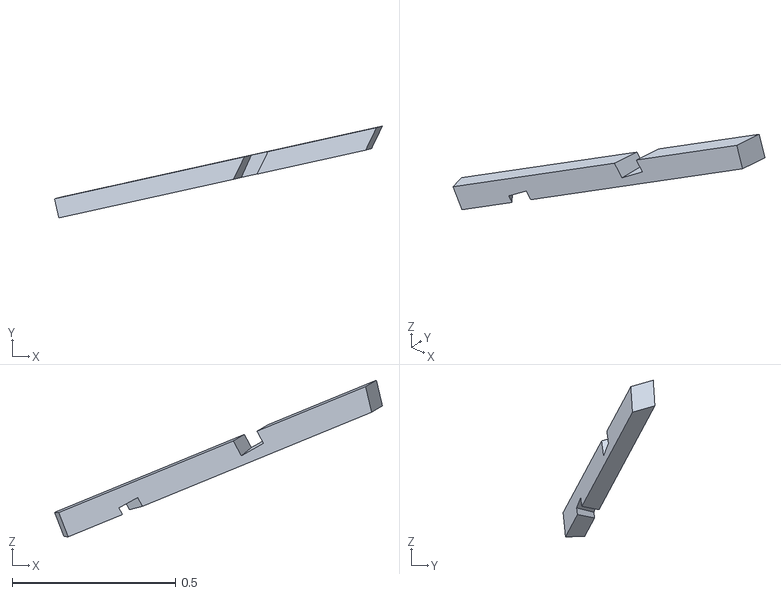
[picture p135: CAD file, 2026-06-04]
web_data/beam/b24/b24.stl
1.00 x 0.281 x 0.48
