gramaziokohler/coding_architecture_fs26_focus_work/web_data/beam/b25/b25.stl

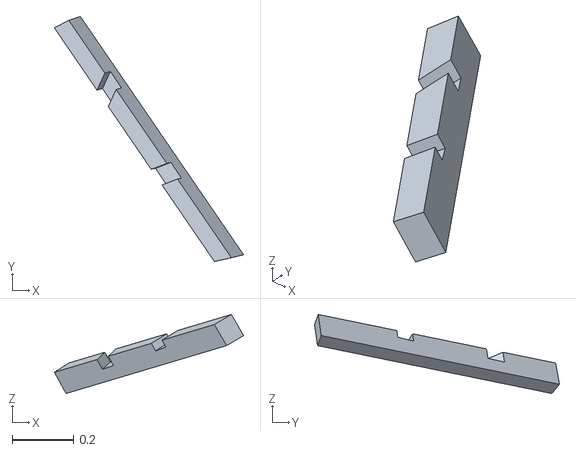
[picture p136: CAD file, 2026-06-04]
web_data/beam/b25/b25.stl
0.617 x 0.799 x 0.258
