gramaziokohler/coding_architecture_fs26_focus_work/web_data/beam/b26/b26.stl

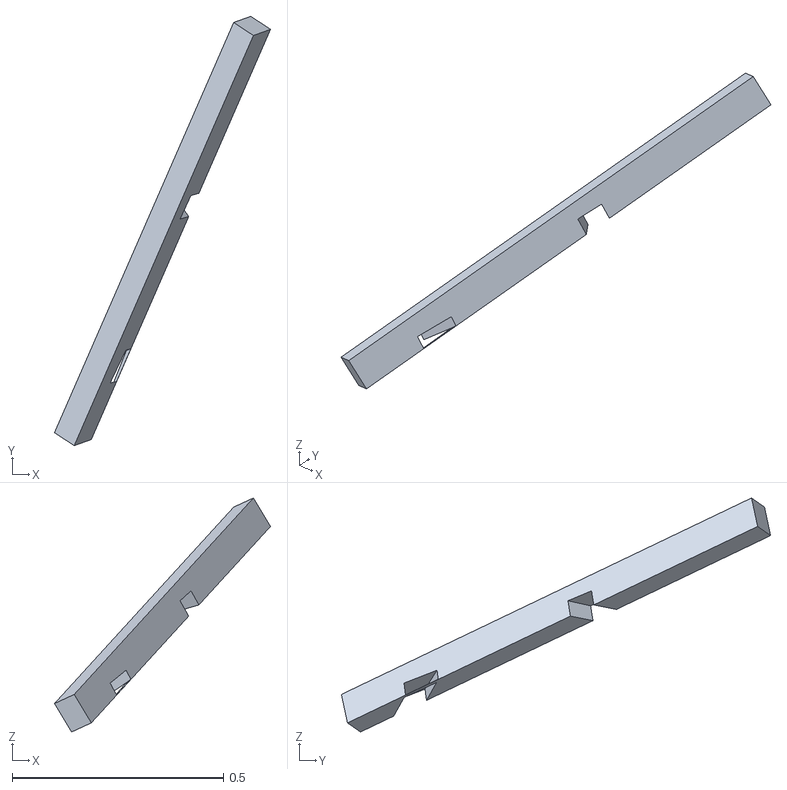
[picture p137: CAD file, 2026-06-04]
web_data/beam/b26/b26.stl
0.512 x 1.02 x 0.554
