gramaziokohler/coding_architecture_fs26_focus_work/web_data/beam/b27/b27.stl

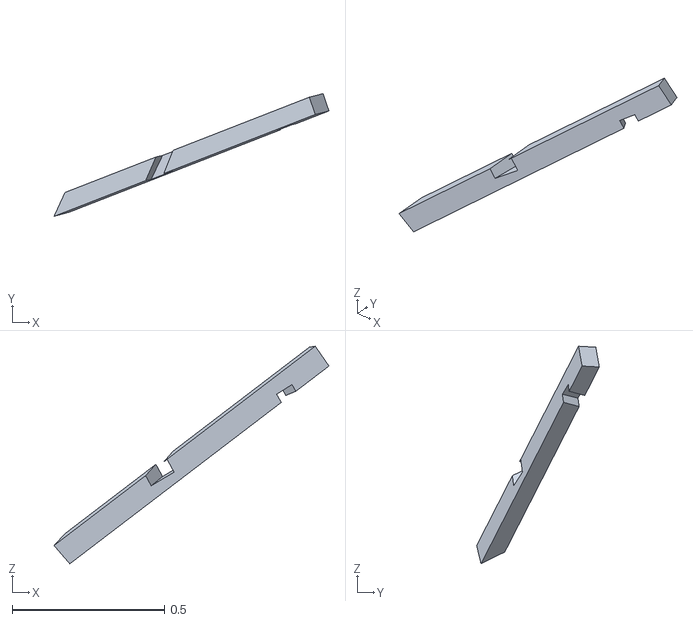
[picture p138: CAD file, 2026-06-04]
web_data/beam/b27/b27.stl
0.902 x 0.403 x 0.714
