gramaziokohler/coding_architecture_fs26_focus_work/web_data/beam/b28/b28.stl

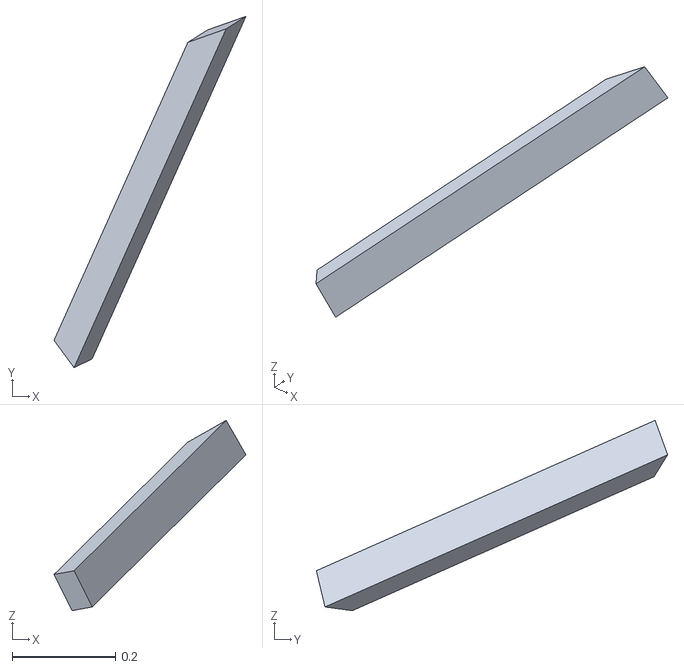
[picture p139: CAD file, 2026-06-04]
web_data/beam/b28/b28.stl
0.371 x 0.679 x 0.368
