gramaziokohler/coding_architecture_fs26_focus_work/web_data/beam/b29/b29.stl

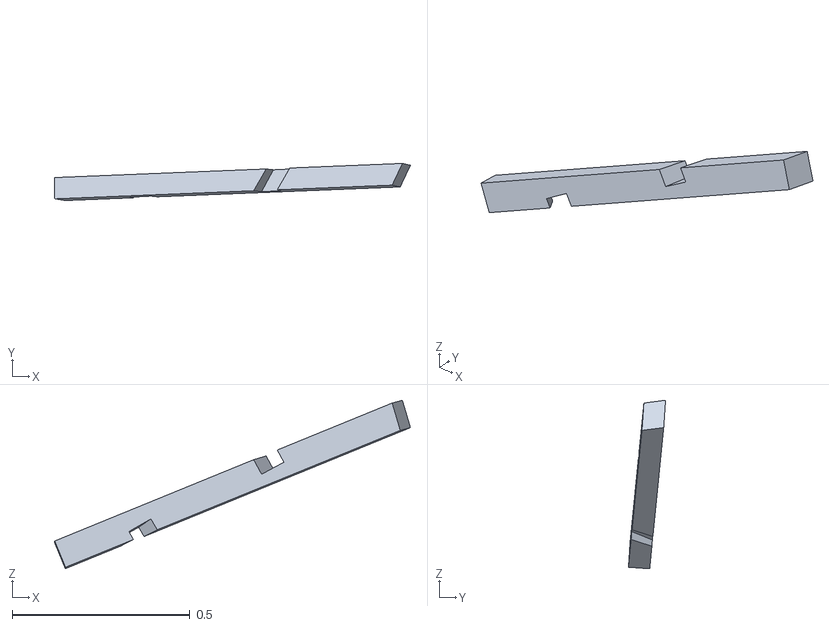
[picture p140: CAD file, 2026-06-04]
web_data/beam/b29/b29.stl
1.00 x 0.104 x 0.474
