gramaziokohler/coding_architecture_fs26_focus_work/web_data/beam/b3/b3.stl

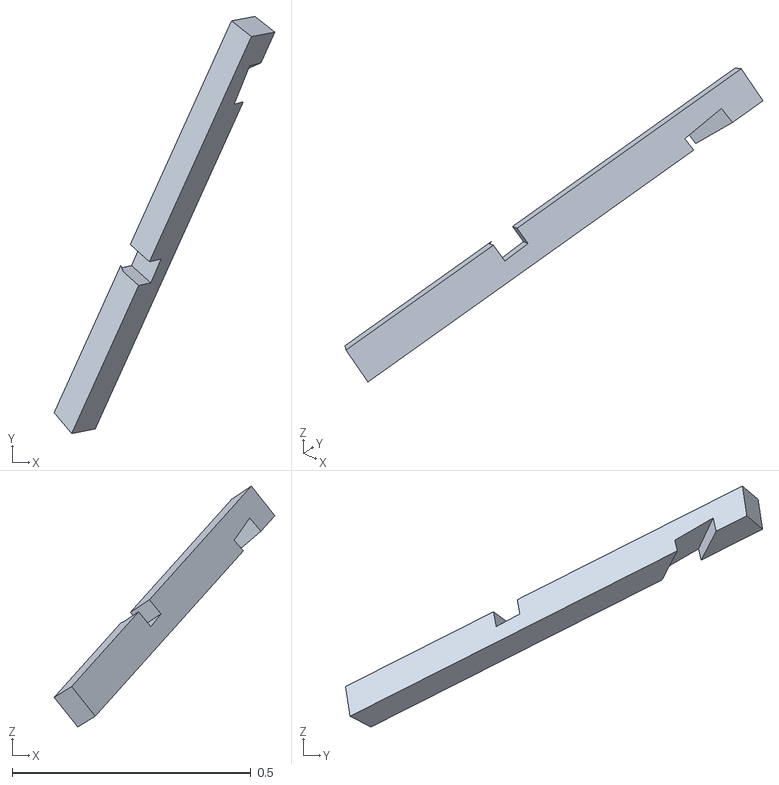
[picture p141: CAD file, 2026-06-04]
web_data/beam/b3/b3.stl
0.462 x 0.874 x 0.505
