gramaziokohler/coding_architecture_fs26_focus_work/web_data/beam/b30/b30.stl

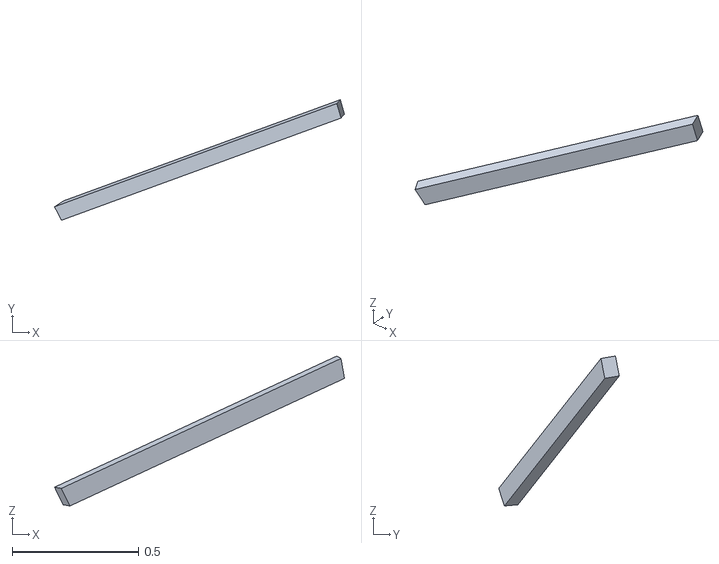
[picture p142: CAD file, 2026-06-04]
web_data/beam/b30/b30.stl
1.15 x 0.477 x 0.593
