gramaziokohler/coding_architecture_fs26_focus_work/web_data/beam/b31/b31.stl

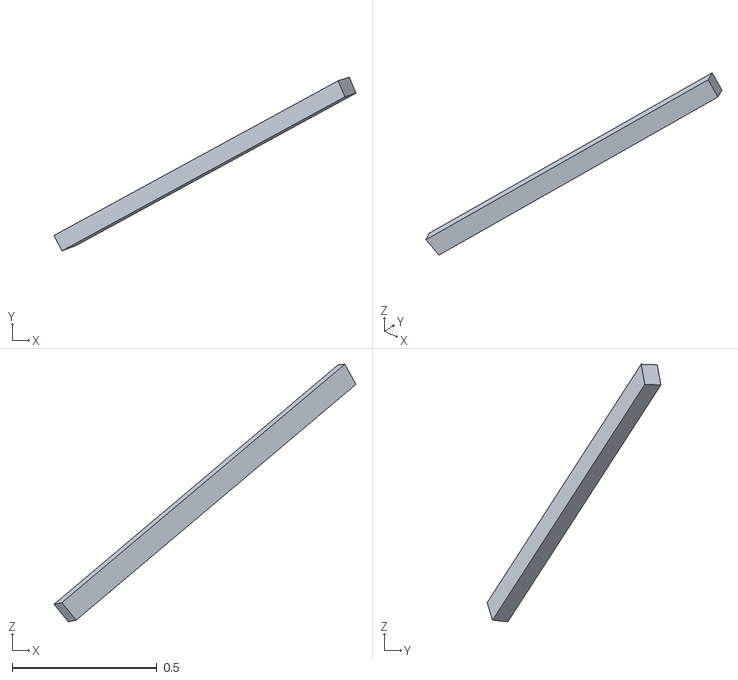
[picture p143: CAD file, 2026-06-04]
web_data/beam/b31/b31.stl
1.04 x 0.6 x 0.889
