gramaziokohler/coding_architecture_fs26_focus_work/web_data/beam/b4/b4.stl

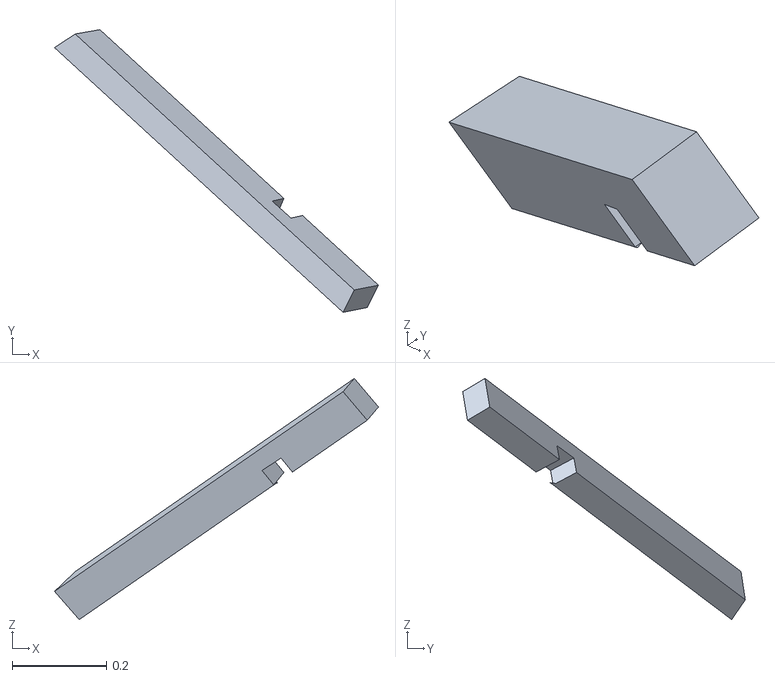
[picture p144: CAD file, 2026-06-04]
web_data/beam/b4/b4.stl
0.687 x 0.599 x 0.511
