gramaziokohler/coding_architecture_fs26_focus_work/web_data/beam/b5/b5.stl

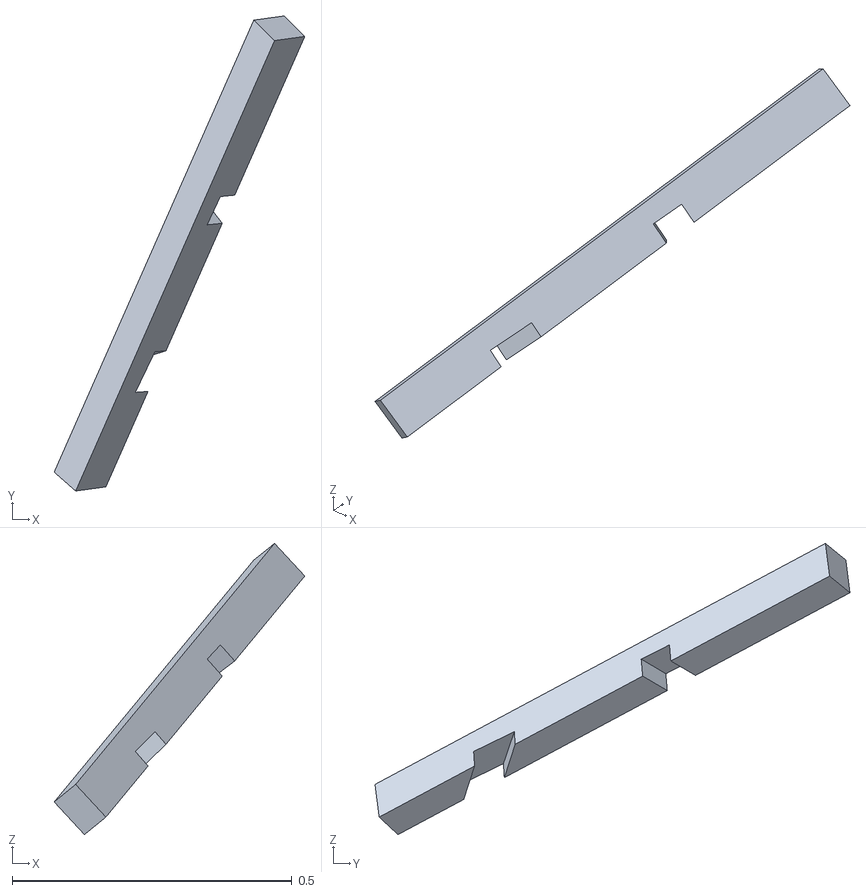
[picture p145: CAD file, 2026-06-04]
web_data/beam/b5/b5.stl
0.448 x 0.85 x 0.521
