gramaziokohler/coding_architecture_fs26_focus_work/web_data/beam/b6/b6.stl

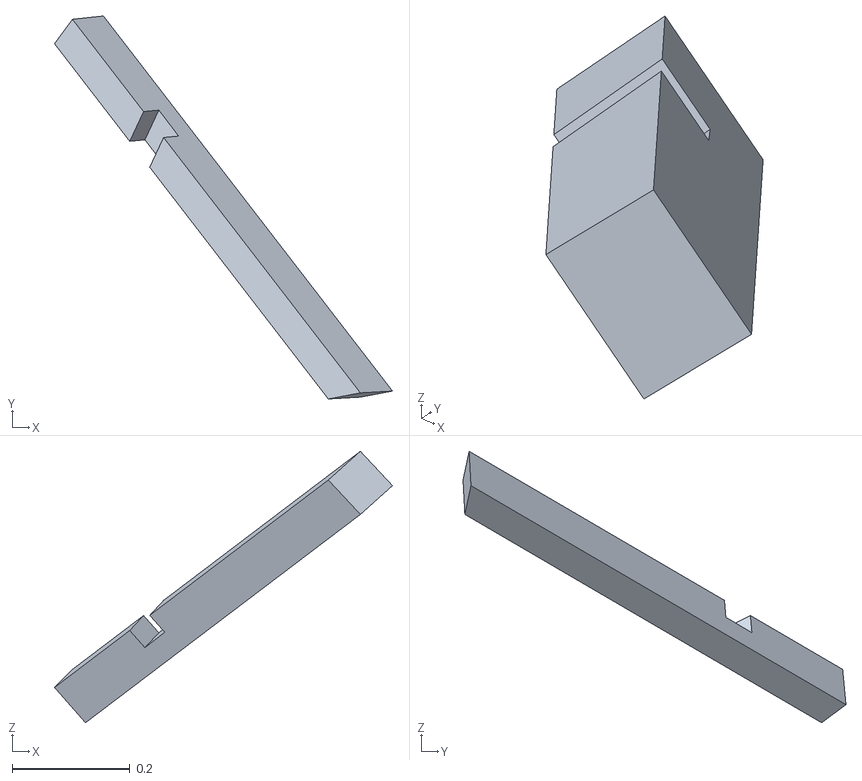
[picture p146: CAD file, 2026-06-04]
web_data/beam/b6/b6.stl
0.575 x 0.651 x 0.462
