gramaziokohler/coding_architecture_fs26_focus_work/web_data/beam/b7/b7.stl

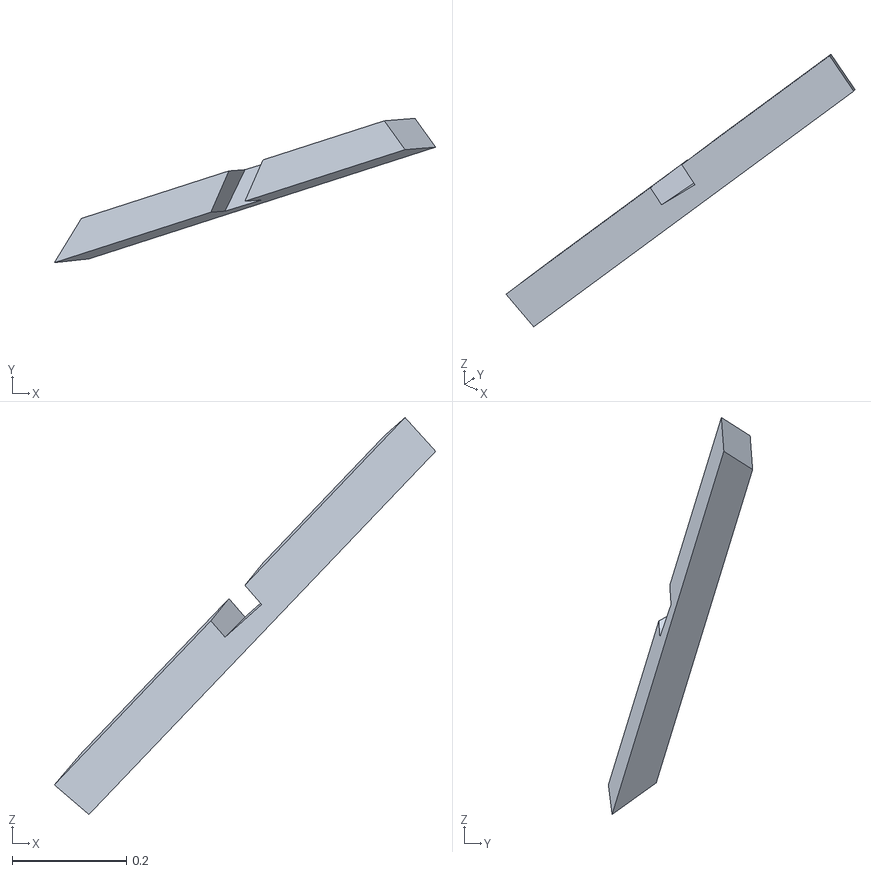
[picture p147: CAD file, 2026-06-04]
web_data/beam/b7/b7.stl
0.669 x 0.253 x 0.696
