gramaziokohler/coding_architecture_fs26_focus_work/web_data/beam/b8/b8.stl

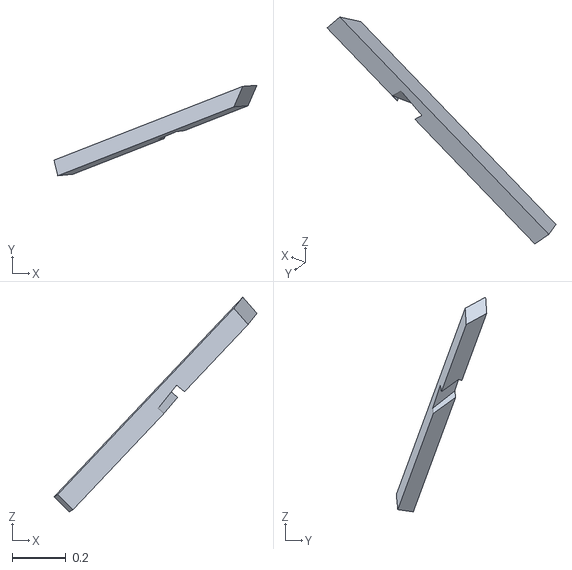
[picture p148: CAD file, 2026-06-04]
web_data/beam/b8/b8.stl
0.753 x 0.336 x 0.797
