gramaziokohler/coding_architecture_fs26_focus_work/web_data/beam/b9/b9.stl

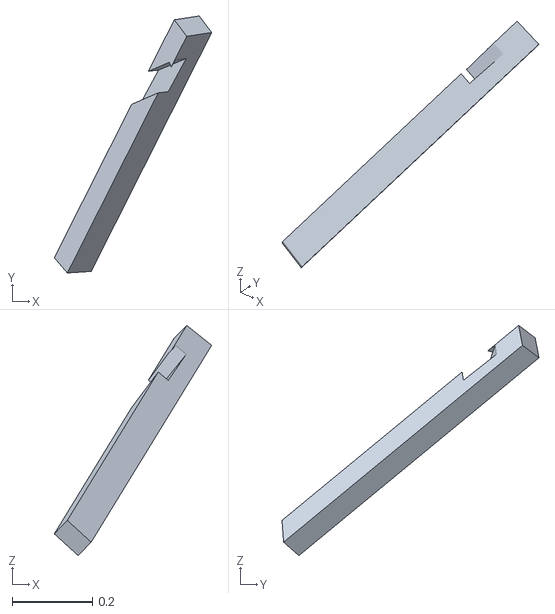
[picture p149: CAD file, 2026-06-04]
web_data/beam/b9/b9.stl
0.391 x 0.639 x 0.572
