gramaziokohler/coding_architecture_fs26_focus_work/web_data/beam/c1/c1.stl

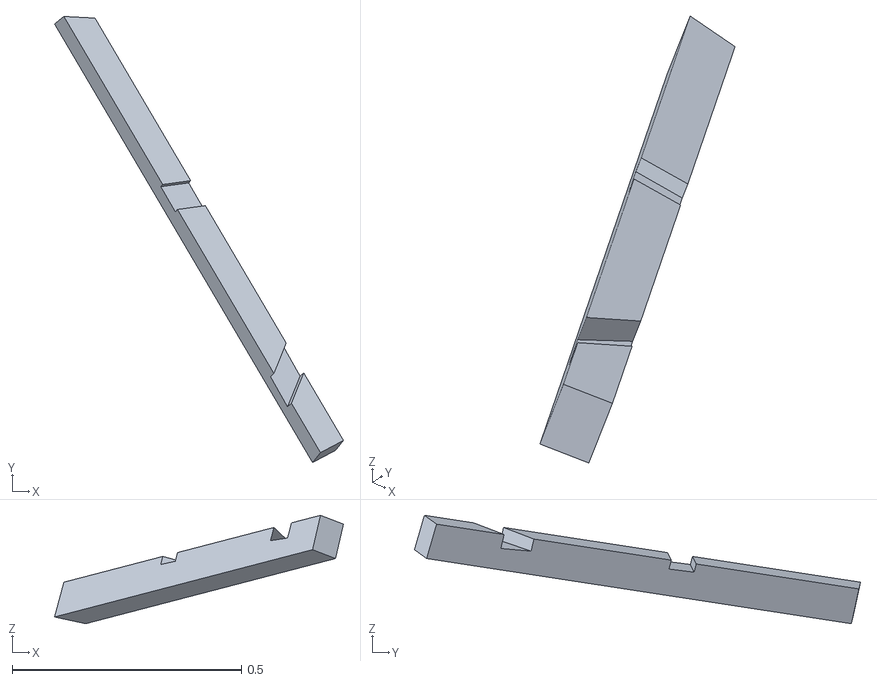
[picture p150: CAD file, 2026-06-04]
web_data/beam/c1/c1.stl
0.631 x 0.973 x 0.236
