gramaziokohler/coding_architecture_fs26_focus_work/web_data/beam/c10/c10.stl

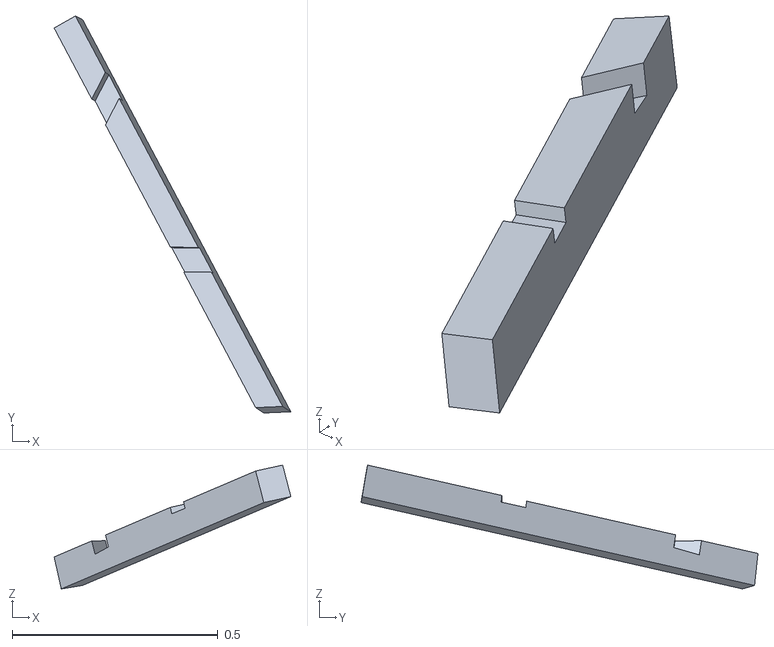
[picture p151: CAD file, 2026-06-04]
web_data/beam/c10/c10.stl
0.575 x 0.964 x 0.301
