gramaziokohler/coding_architecture_fs26_focus_work/web_data/beam/c11/c11.stl

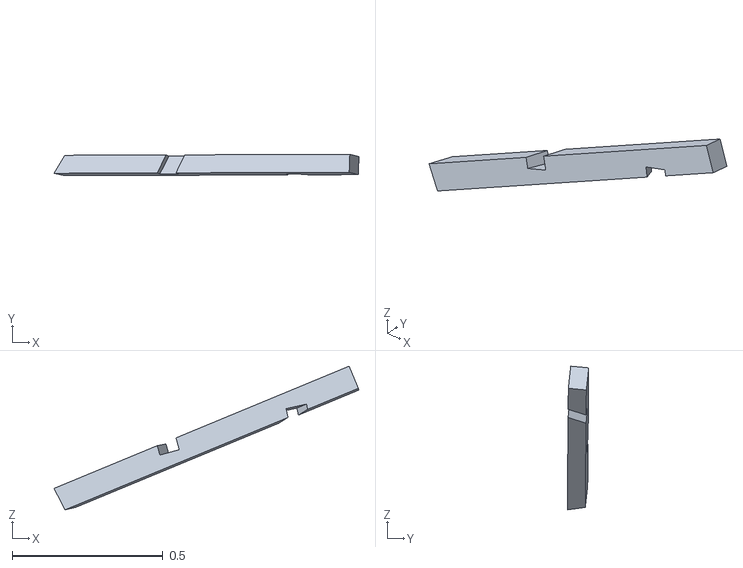
[picture p152: CAD file, 2026-06-04]
web_data/beam/c11/c11.stl
1.01 x 0.0712 x 0.477
