gramaziokohler/coding_architecture_fs26_focus_work/web_data/beam/c12/c12.stl

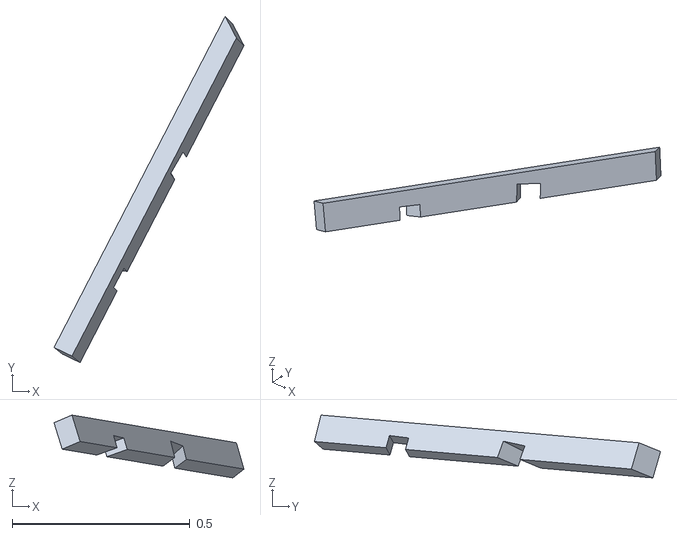
[picture p153: CAD file, 2026-06-04]
web_data/beam/c12/c12.stl
0.535 x 0.974 x 0.177
