gramaziokohler/coding_architecture_fs26_focus_work/web_data/beam/c13/c13.stl

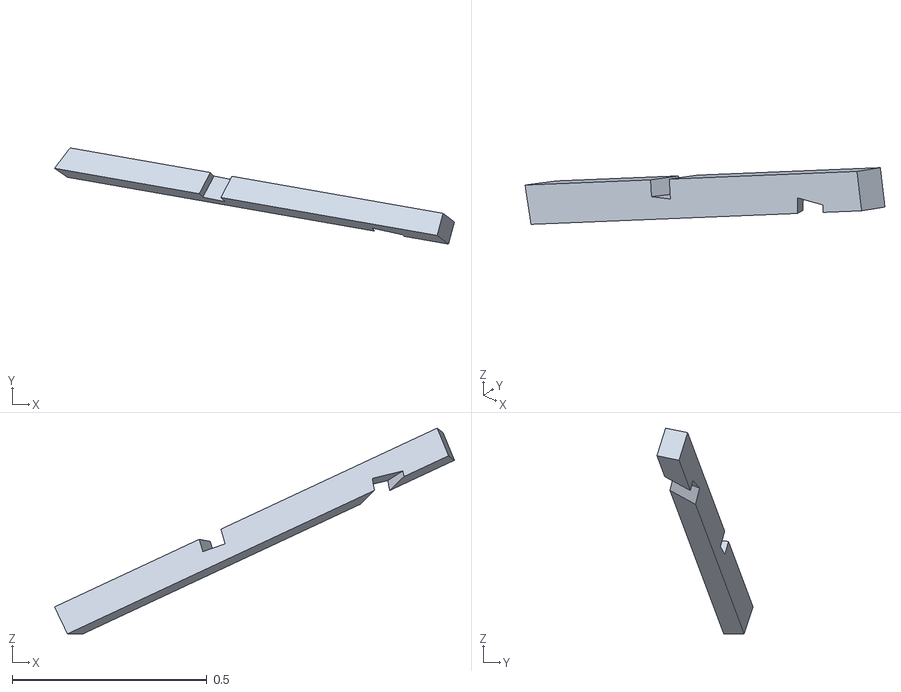
[picture p154: CAD file, 2026-06-04]
web_data/beam/c13/c13.stl
1.03 x 0.247 x 0.529
