gramaziokohler/coding_architecture_fs26_focus_work/web_data/beam/c14/c14.stl

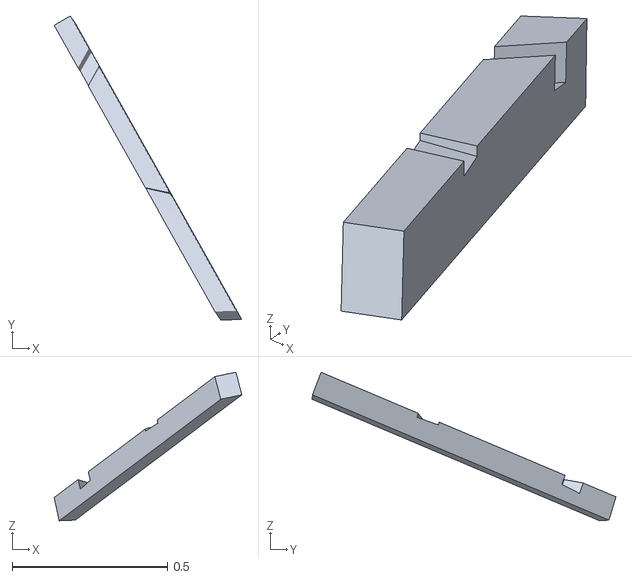
[picture p155: CAD file, 2026-06-04]
web_data/beam/c14/c14.stl
0.605 x 0.98 x 0.479
