gramaziokohler/coding_architecture_fs26_focus_work/web_data/beam/c15/c15.stl

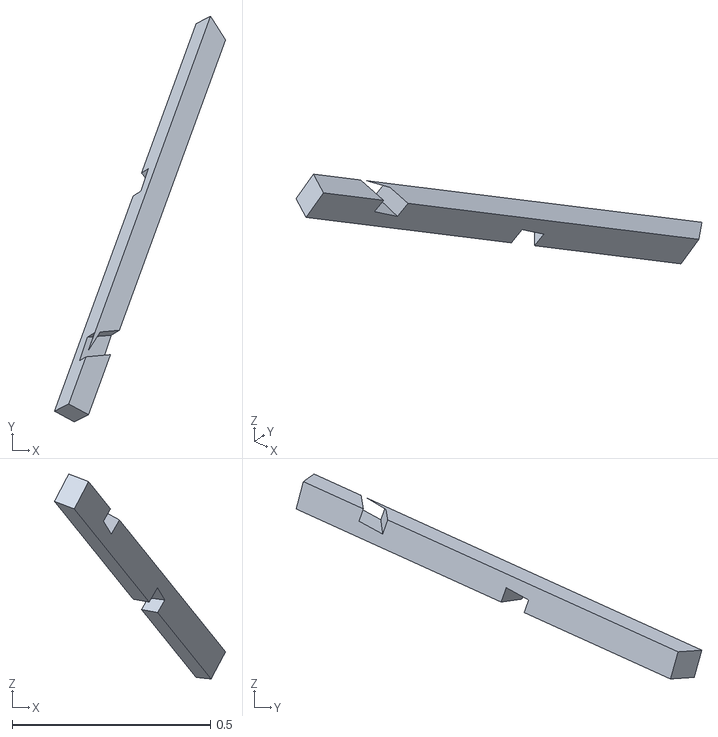
[picture p156: CAD file, 2026-06-04]
web_data/beam/c15/c15.stl
0.432 x 1.02 x 0.517
