gramaziokohler/coding_architecture_fs26_focus_work/web_data/beam/c16/c16.stl

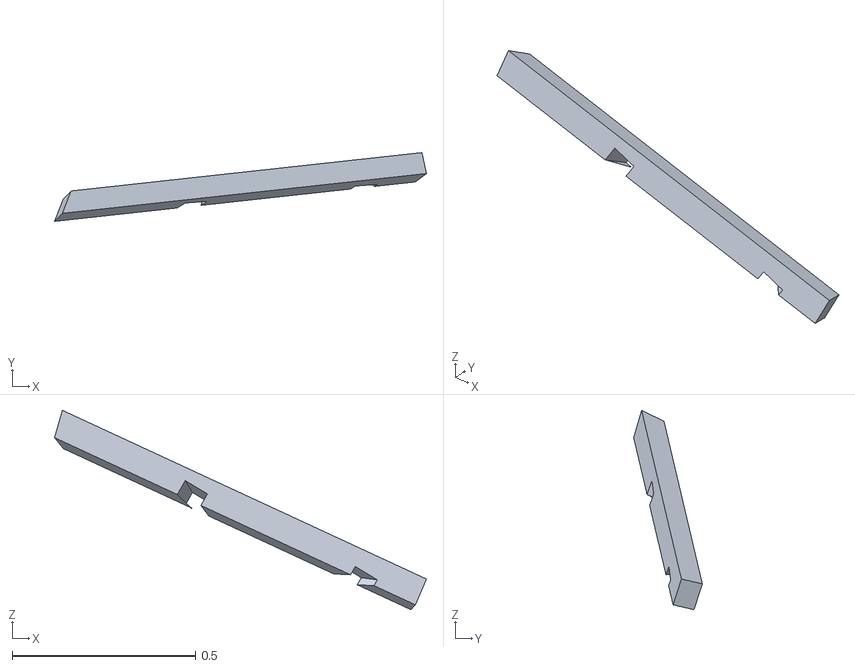
[picture p157: CAD file, 2026-06-04]
web_data/beam/c16/c16.stl
1.02 x 0.188 x 0.545
