gramaziokohler/coding_architecture_fs26_focus_work/web_data/beam/c17/c17.stl

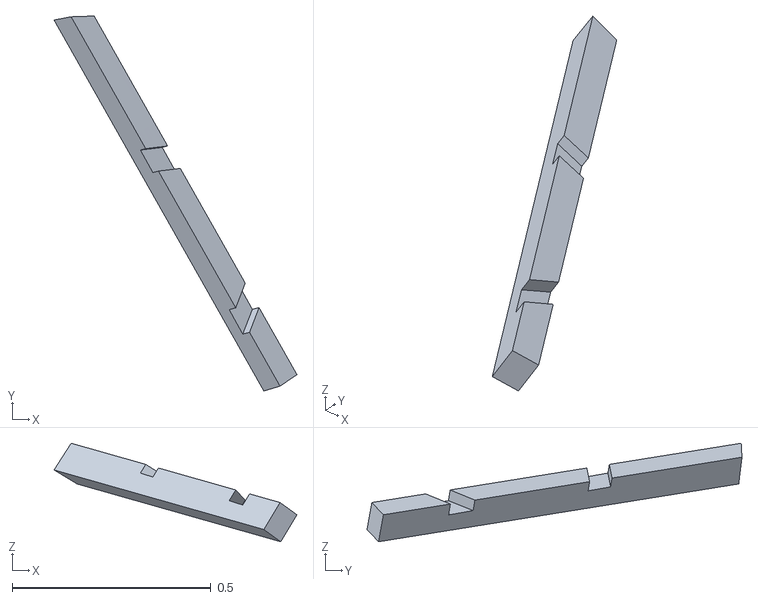
[picture p158: CAD file, 2026-06-04]
web_data/beam/c17/c17.stl
0.61 x 0.942 x 0.248
