gramaziokohler/coding_architecture_fs26_focus_work/web_data/beam/c18/c18.stl

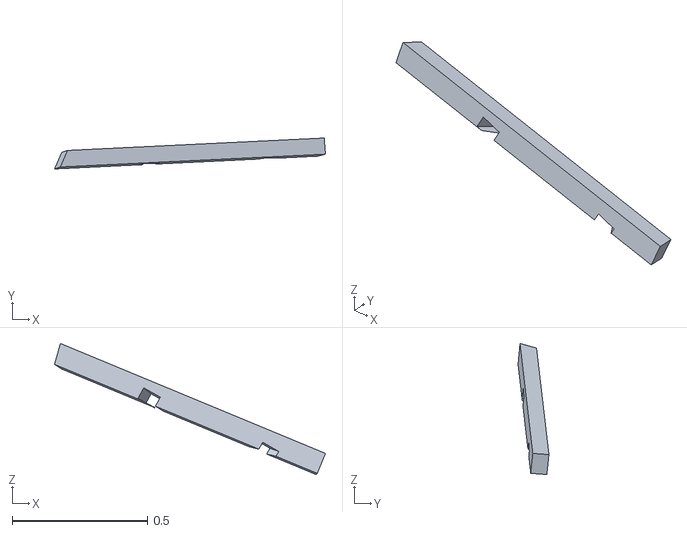
[picture p159: CAD file, 2026-06-04]
web_data/beam/c18/c18.stl
1.00 x 0.114 x 0.484
