gramaziokohler/coding_architecture_fs26_focus_work/web_data/beam/c19/c19.stl

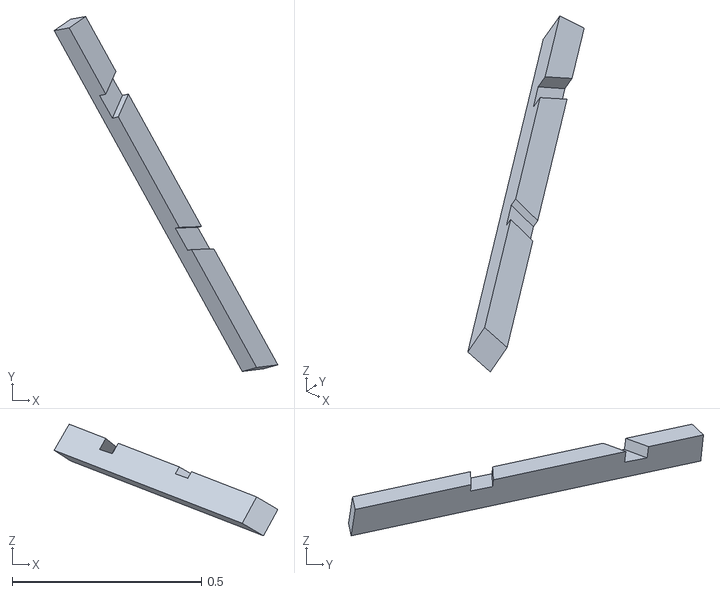
[picture p160: CAD file, 2026-06-04]
web_data/beam/c19/c19.stl
0.592 x 0.939 x 0.295
