gramaziokohler/coding_architecture_fs26_focus_work/web_data/beam/c2/c2.stl

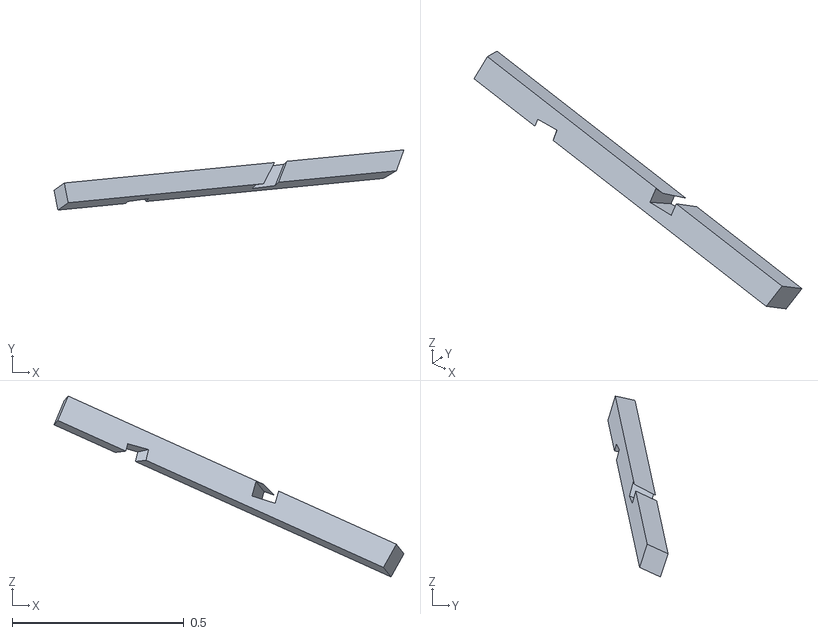
[picture p161: CAD file, 2026-06-04]
web_data/beam/c2/c2.stl
1.02 x 0.175 x 0.526
