gramaziokohler/coding_architecture_fs26_focus_work/web_data/beam/c20/c20.stl

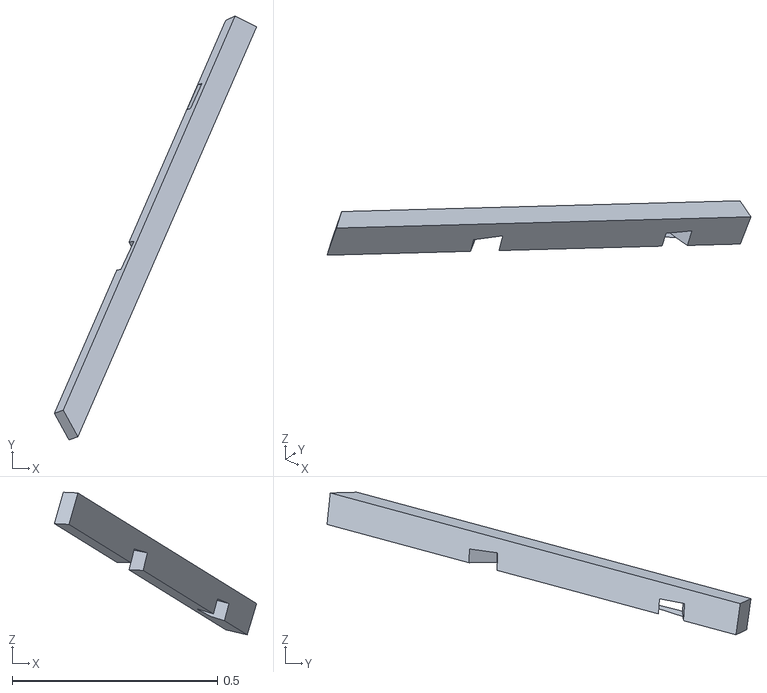
[picture p162: CAD file, 2026-06-04]
web_data/beam/c20/c20.stl
0.493 x 1.03 x 0.347
