gramaziokohler/coding_architecture_fs26_focus_work/web_data/beam/c21/c21.stl

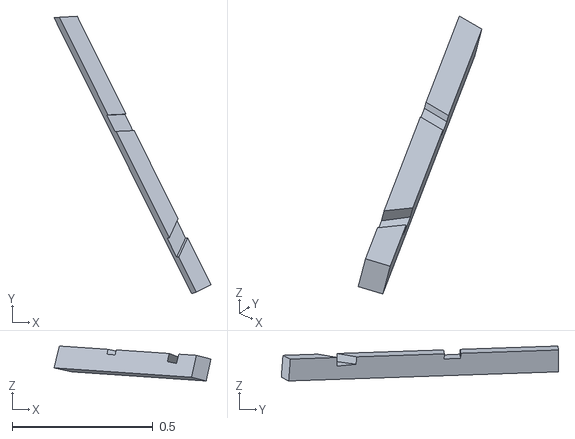
[picture p163: CAD file, 2026-06-04]
web_data/beam/c21/c21.stl
0.558 x 0.987 x 0.124
