gramaziokohler/coding_architecture_fs26_focus_work/web_data/beam/c22/c22.stl

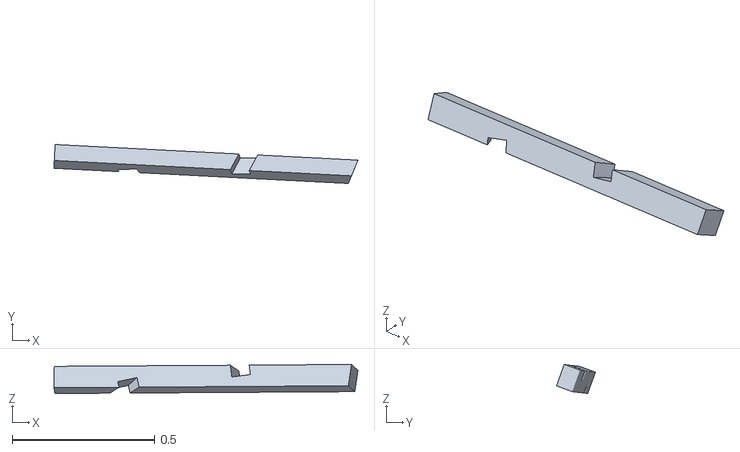
[picture p164: CAD file, 2026-06-04]
web_data/beam/c22/c22.stl
1.07 x 0.137 x 0.102
