gramaziokohler/coding_architecture_fs26_focus_work/web_data/beam/c23/c23.stl

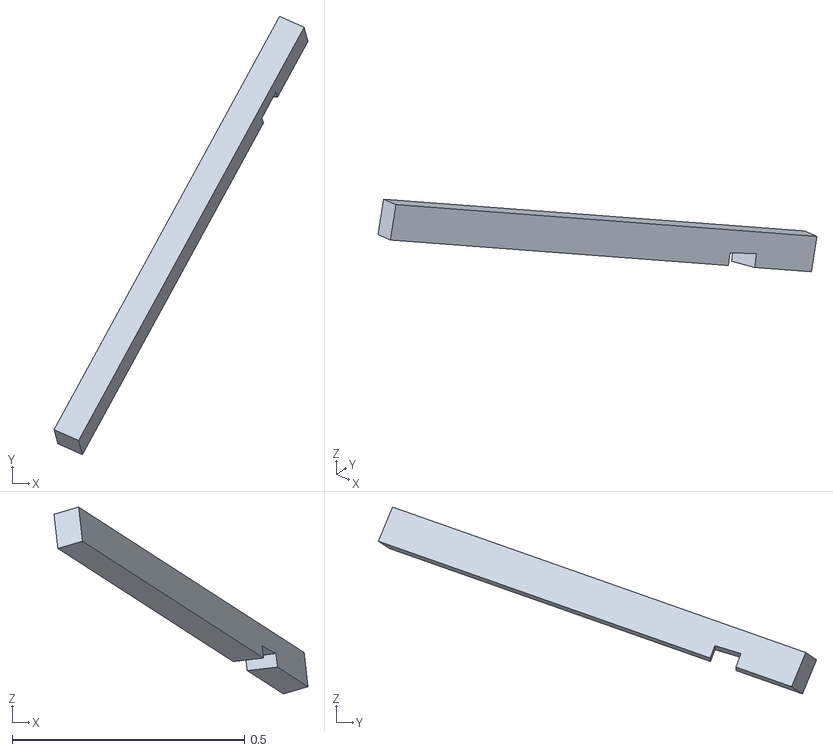
[picture p165: CAD file, 2026-06-04]
web_data/beam/c23/c23.stl
0.547 x 0.943 x 0.402
