gramaziokohler/coding_architecture_fs26_focus_work/web_data/beam/c24/c24.stl

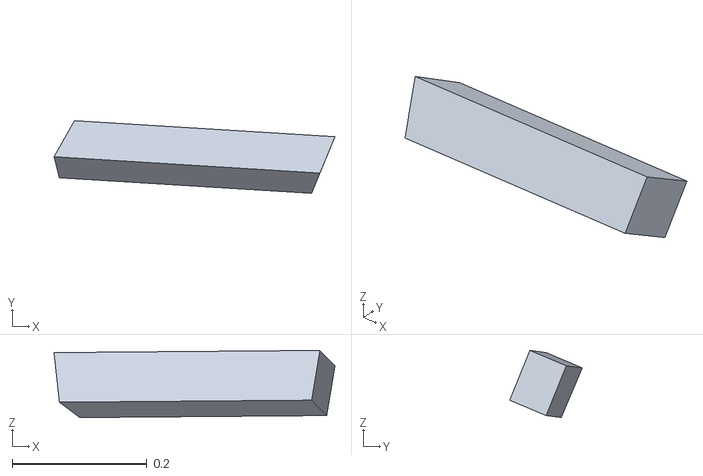
[picture p166: CAD file, 2026-06-04]
web_data/beam/c24/c24.stl
0.418 x 0.108 x 0.0998
