gramaziokohler/coding_architecture_fs26_focus_work/web_data/beam/c25/c25.stl

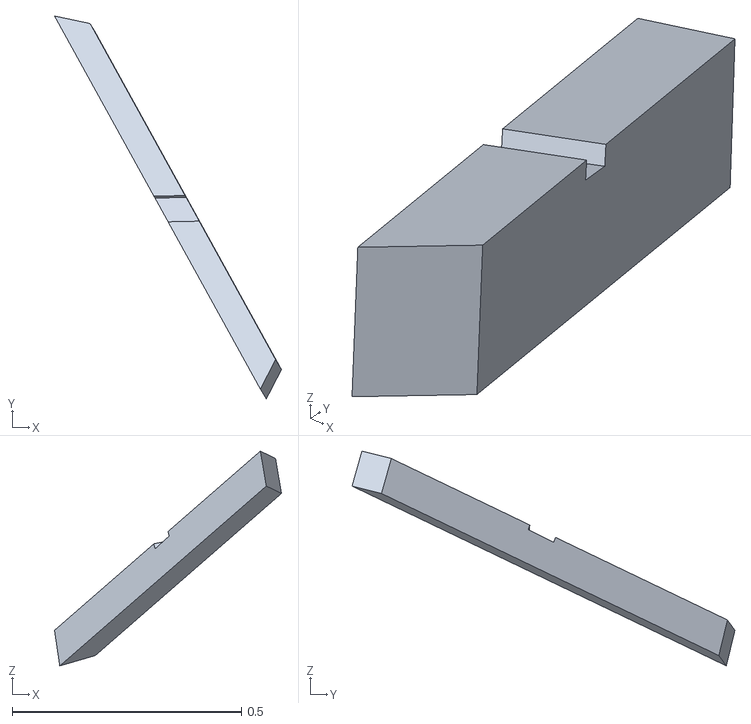
[picture p167: CAD file, 2026-06-04]
web_data/beam/c25/c25.stl
0.495 x 0.835 x 0.468
