gramaziokohler/coding_architecture_fs26_focus_work/web_data/beam/c26/c26.stl

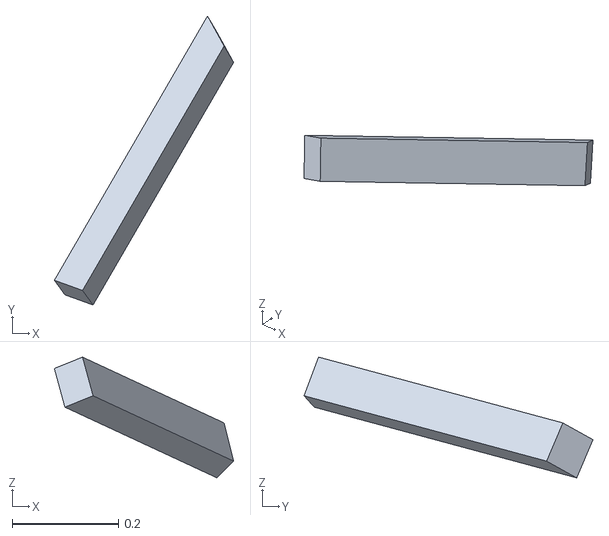
[picture p168: CAD file, 2026-06-04]
web_data/beam/c26/c26.stl
0.337 x 0.543 x 0.227
