gramaziokohler/coding_architecture_fs26_focus_work/web_data/beam/c27/c27.stl

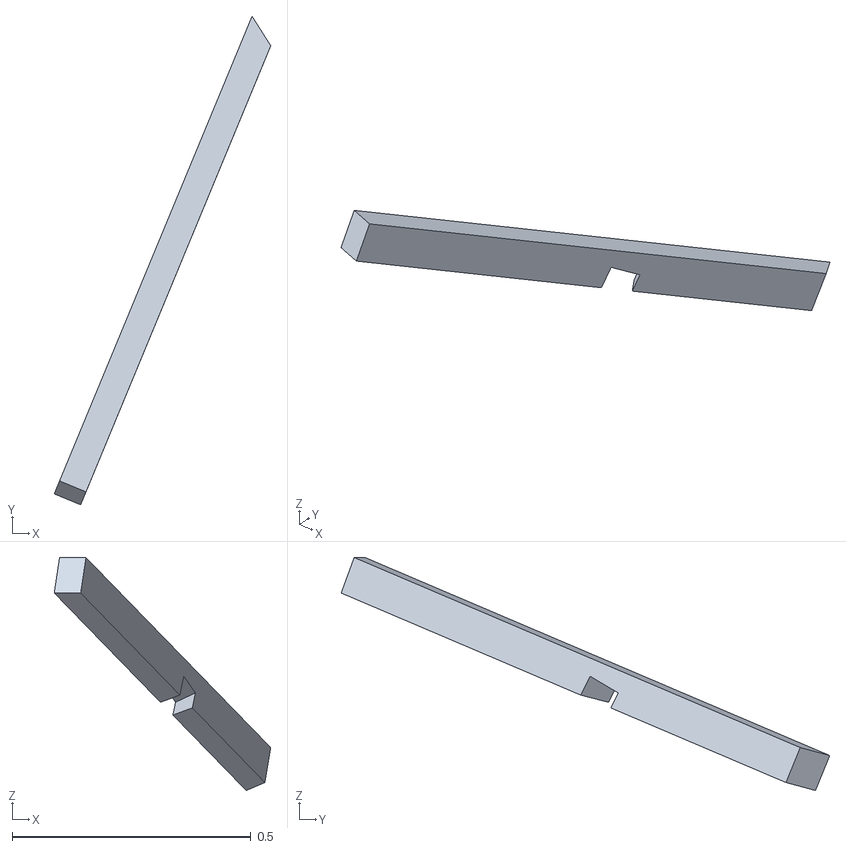
[picture p169: CAD file, 2026-06-04]
web_data/beam/c27/c27.stl
0.454 x 1.02 x 0.488
