gramaziokohler/coding_architecture_fs26_focus_work/web_data/beam/c28/c28.stl

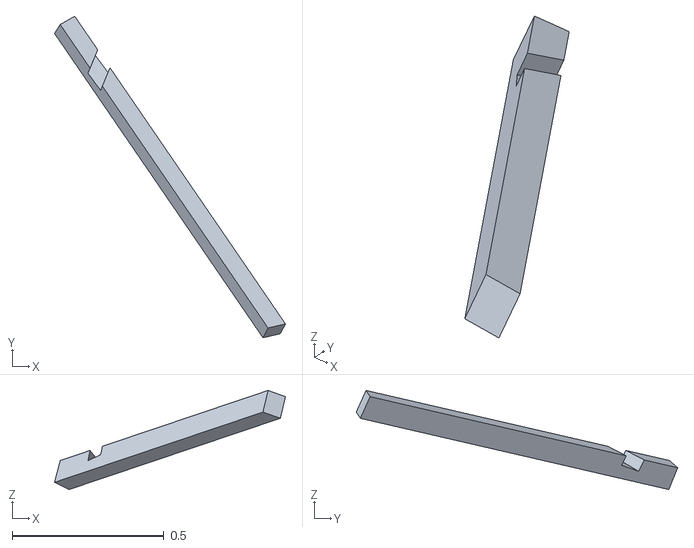
[picture p170: CAD file, 2026-06-04]
web_data/beam/c28/c28.stl
0.761 x 1.06 x 0.327
