gramaziokohler/coding_architecture_fs26_focus_work/web_data/beam/c29/c29.stl

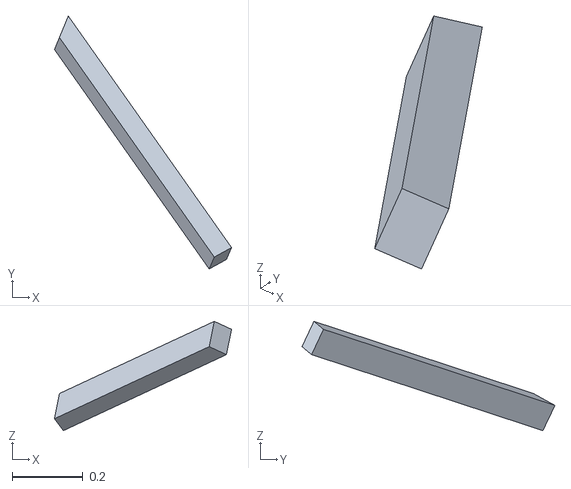
[picture p171: CAD file, 2026-06-04]
web_data/beam/c29/c29.stl
0.499 x 0.713 x 0.308
