gramaziokohler/coding_architecture_fs26_focus_work/web_data/beam/c3/c3.stl

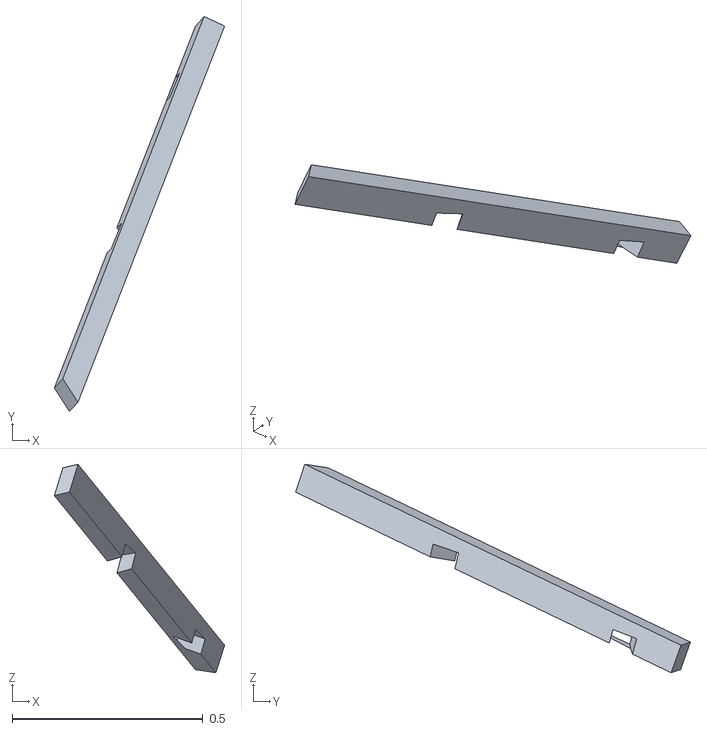
[picture p172: CAD file, 2026-06-04]
web_data/beam/c3/c3.stl
0.447 x 1.04 x 0.547
