gramaziokohler/coding_architecture_fs26_focus_work/web_data/beam/c30/c30.stl

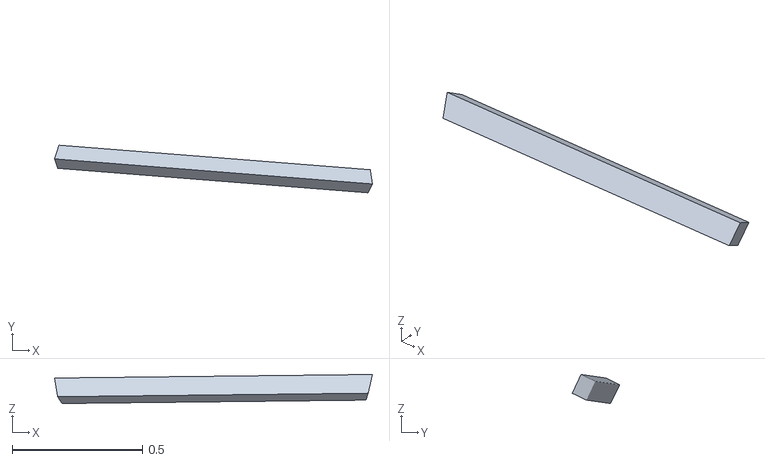
[picture p173: CAD file, 2026-06-04]
web_data/beam/c30/c30.stl
1.22 x 0.183 x 0.112
