gramaziokohler/coding_architecture_fs26_focus_work/web_data/beam/c4/c4.stl

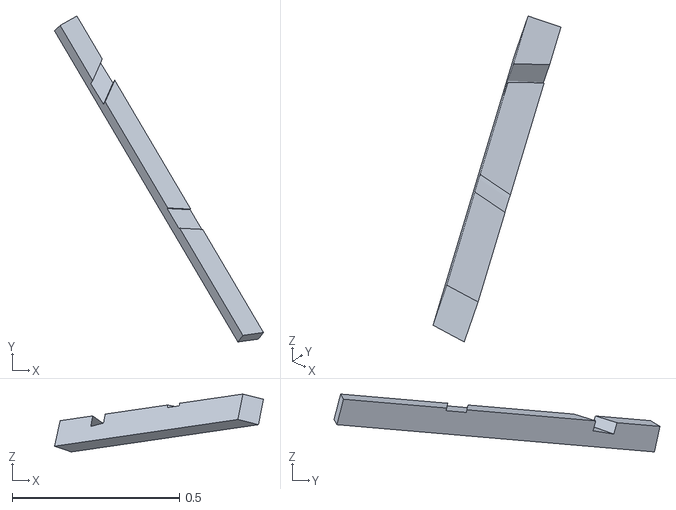
[picture p174: CAD file, 2026-06-04]
web_data/beam/c4/c4.stl
0.625 x 0.975 x 0.173
