gramaziokohler/coding_architecture_fs26_focus_work/web_data/beam/c5/c5.stl

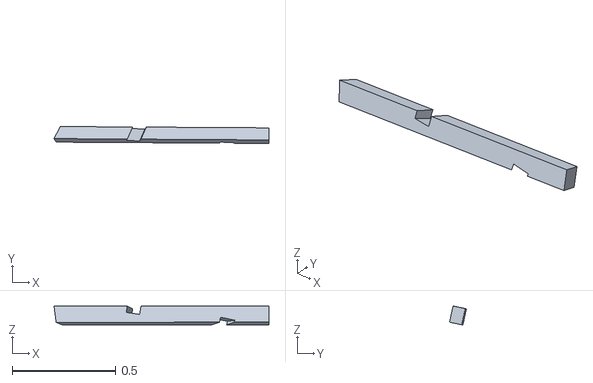
[picture p175: CAD file, 2026-06-04]
web_data/beam/c5/c5.stl
1.04 x 0.082 x 0.0919
