gramaziokohler/coding_architecture_fs26_focus_work/web_data/beam/c6/c6.stl

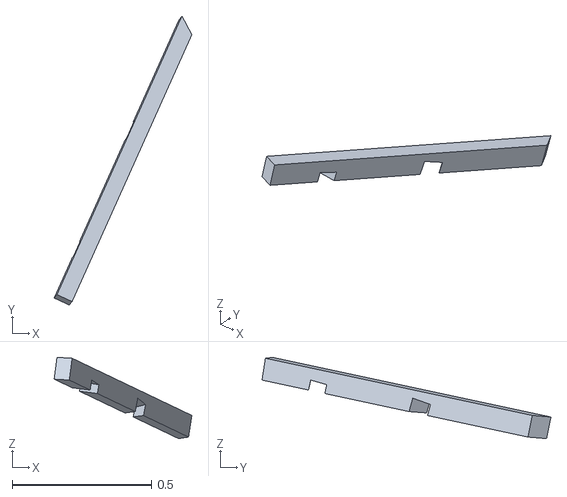
[picture p176: CAD file, 2026-06-04]
web_data/beam/c6/c6.stl
0.495 x 1.04 x 0.292
