gramaziokohler/coding_architecture_fs26_focus_work/web_data/beam/c7/c7.stl

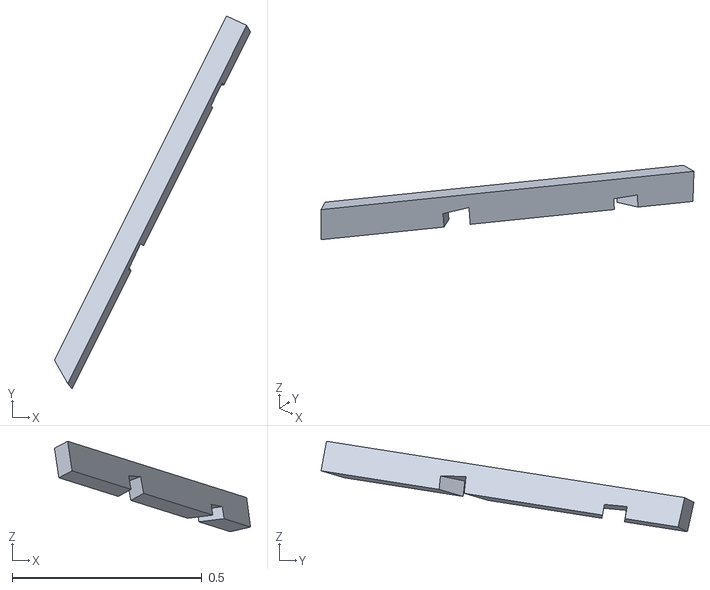
[picture p177: CAD file, 2026-06-04]
web_data/beam/c7/c7.stl
0.517 x 0.982 x 0.238
