gramaziokohler/coding_architecture_fs26_focus_work/web_data/beam/c8/c8.stl

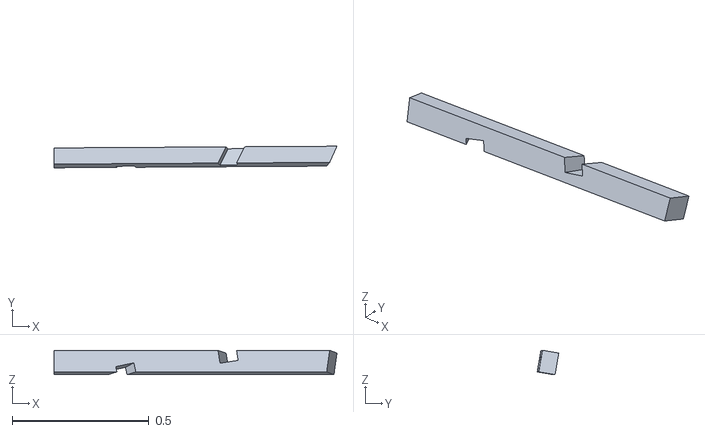
[picture p178: CAD file, 2026-06-04]
web_data/beam/c8/c8.stl
1.03 x 0.0791 x 0.0893
