gramaziokohler/coding_architecture_fs26_focus_work/web_data/beam/c9/c9.stl

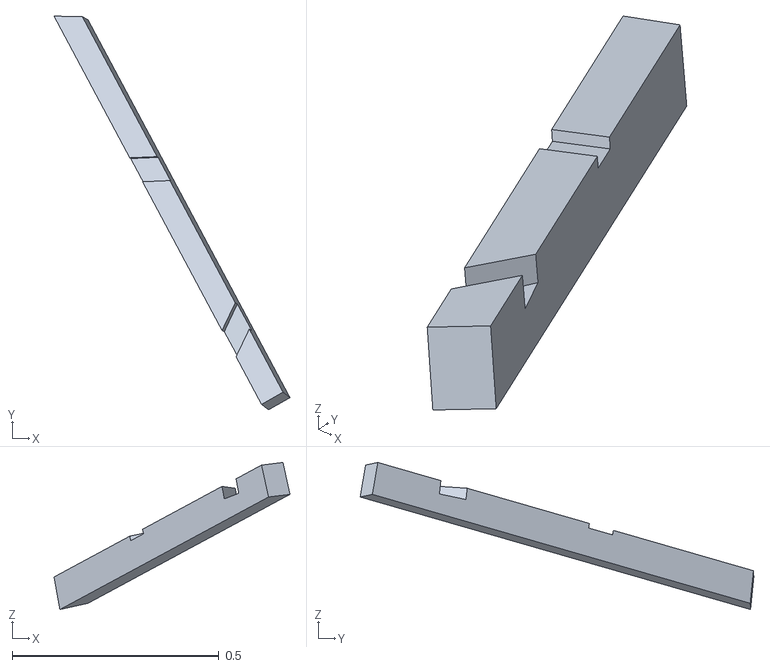
[picture p179: CAD file, 2026-06-04]
web_data/beam/c9/c9.stl
0.57 x 0.951 x 0.355
