gramaziokohler/coding_architecture_fs26_focus_work/web_data/beam/d1/d1.stl

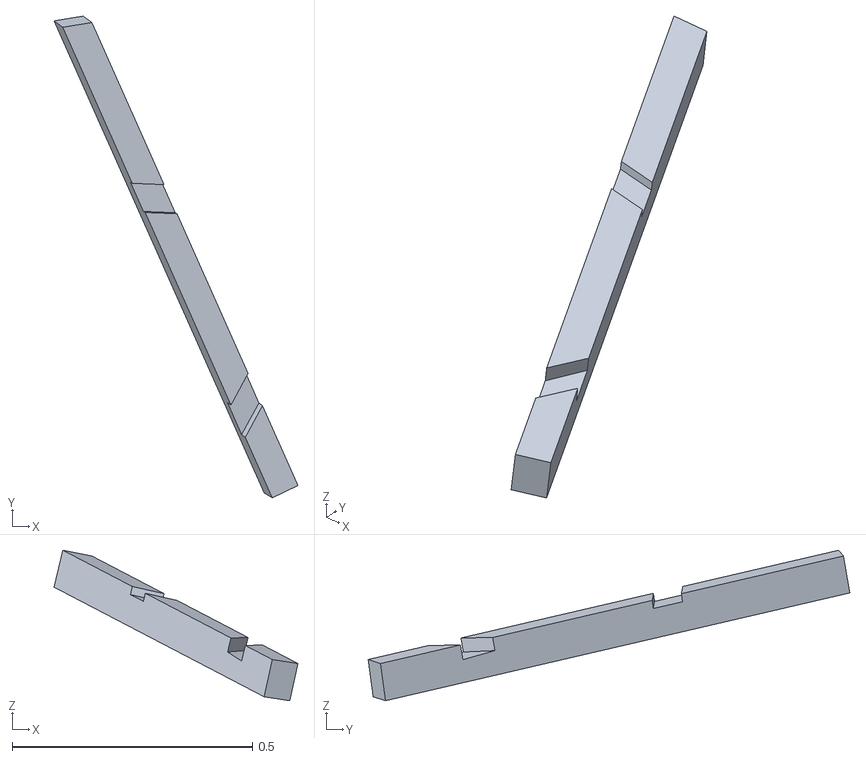
[picture p180: CAD file, 2026-06-04]
web_data/beam/d1/d1.stl
0.508 x 1.00 x 0.313
