gramaziokohler/coding_architecture_fs26_focus_work/web_data/beam/d10/d10.stl

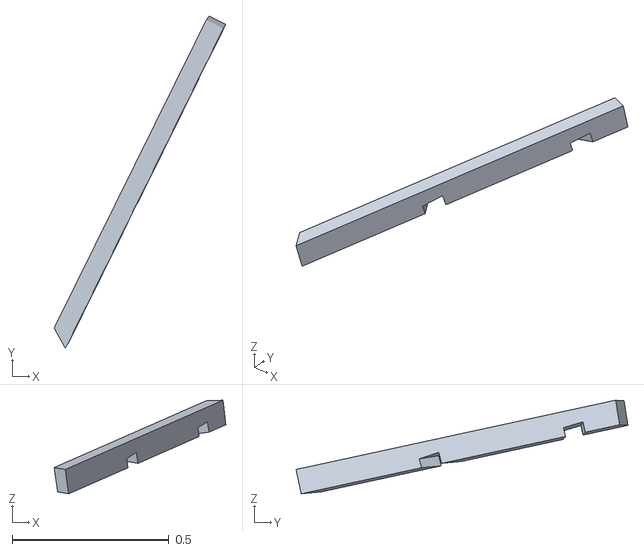
[picture p181: CAD file, 2026-06-04]
web_data/beam/d10/d10.stl
0.548 x 1.06 x 0.299
