gramaziokohler/coding_architecture_fs26_focus_work/web_data/beam/d11/d11.stl

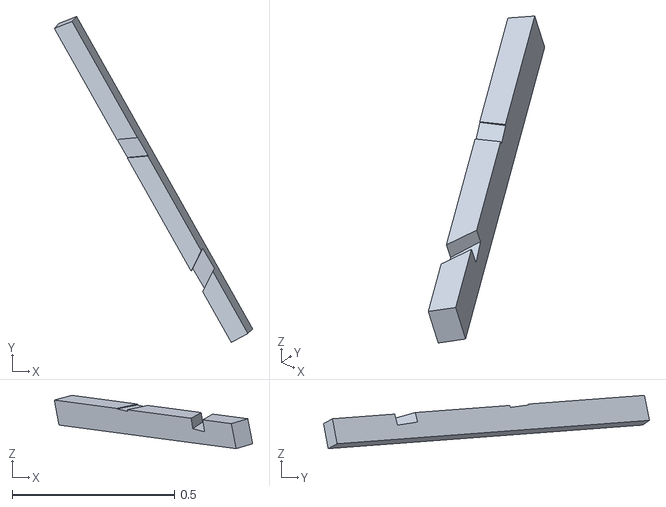
[picture p182: CAD file, 2026-06-04]
web_data/beam/d11/d11.stl
0.612 x 1.01 x 0.165
