gramaziokohler/coding_architecture_fs26_focus_work/web_data/beam/d12/d12.stl

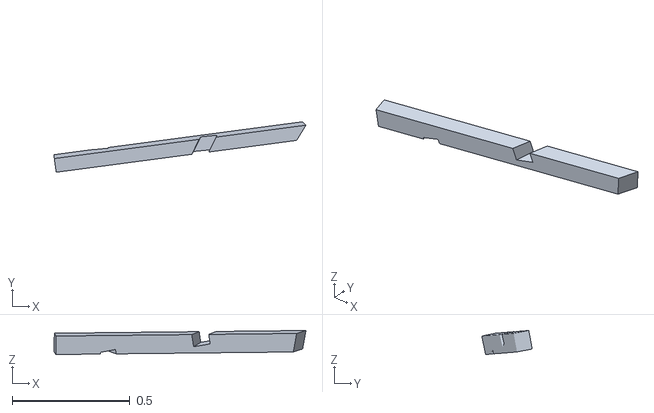
[picture p183: CAD file, 2026-06-04]
web_data/beam/d12/d12.stl
1.07 x 0.214 x 0.102
