gramaziokohler/coding_architecture_fs26_focus_work/web_data/beam/d13/d13.stl

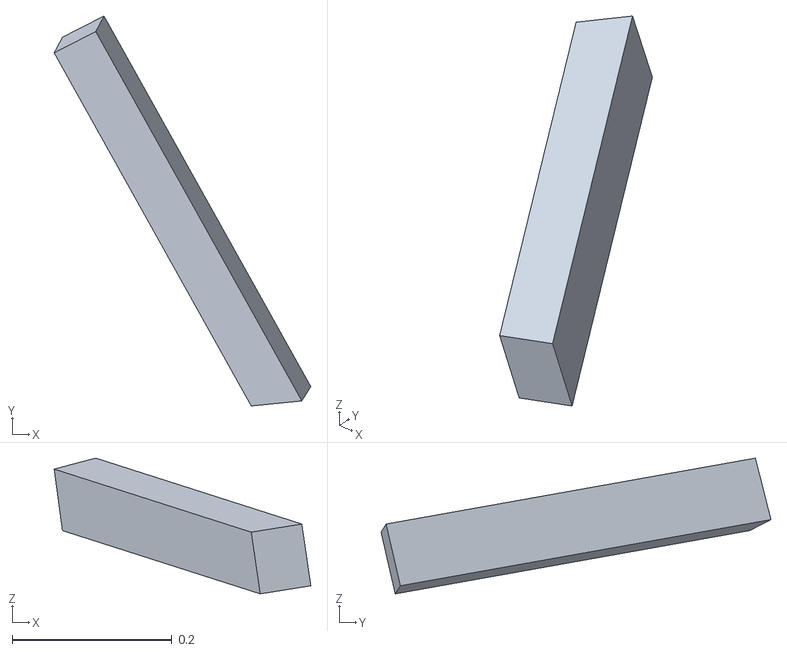
[picture p184: CAD file, 2026-06-04]
web_data/beam/d13/d13.stl
0.321 x 0.488 x 0.17
