gramaziokohler/coding_architecture_fs26_focus_work/web_data/beam/d14/d14.stl

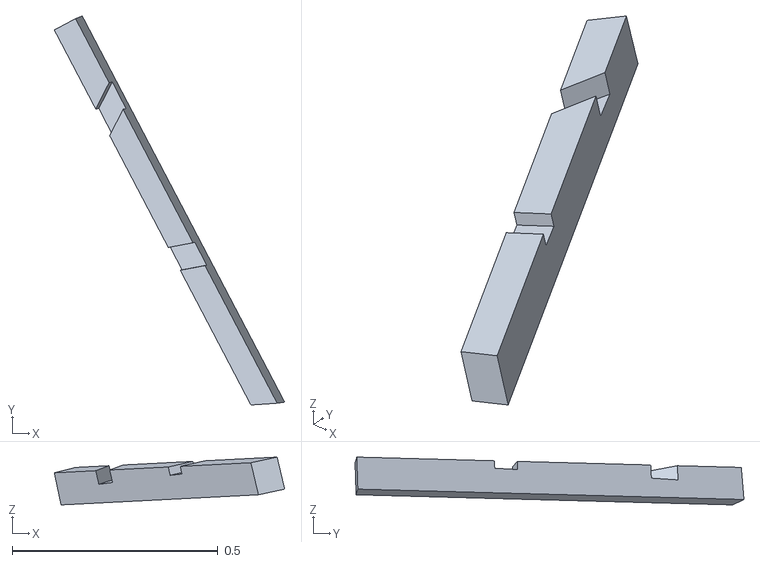
[picture p185: CAD file, 2026-06-04]
web_data/beam/d14/d14.stl
0.56 x 0.946 x 0.116
