gramaziokohler/coding_architecture_fs26_focus_work/web_data/beam/d15/d15.stl

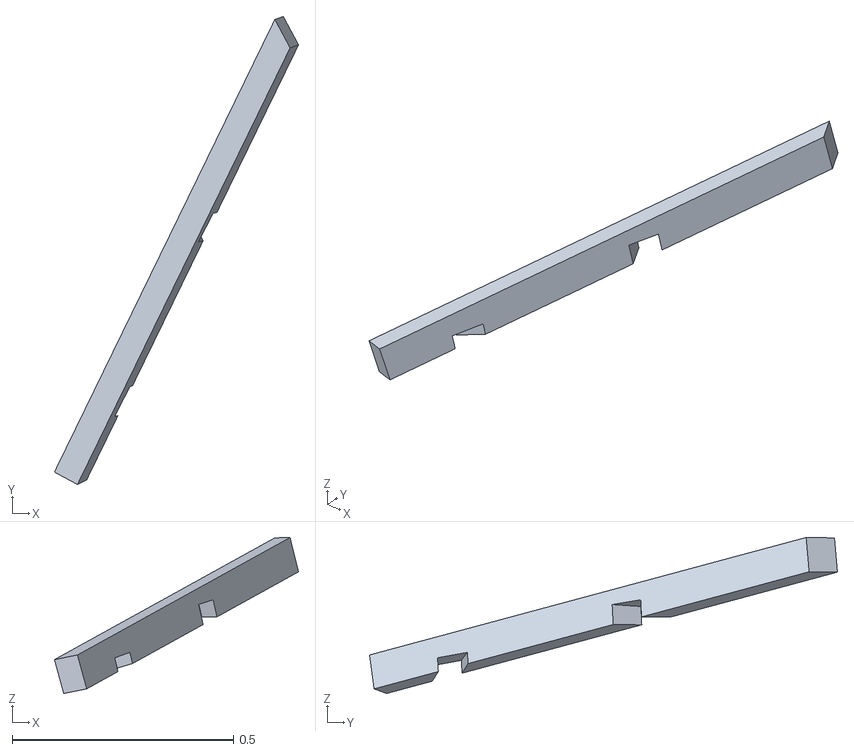
[picture p186: CAD file, 2026-06-04]
web_data/beam/d15/d15.stl
0.551 x 1.06 x 0.352
