gramaziokohler/coding_architecture_fs26_focus_work/web_data/beam/d16/d16.stl

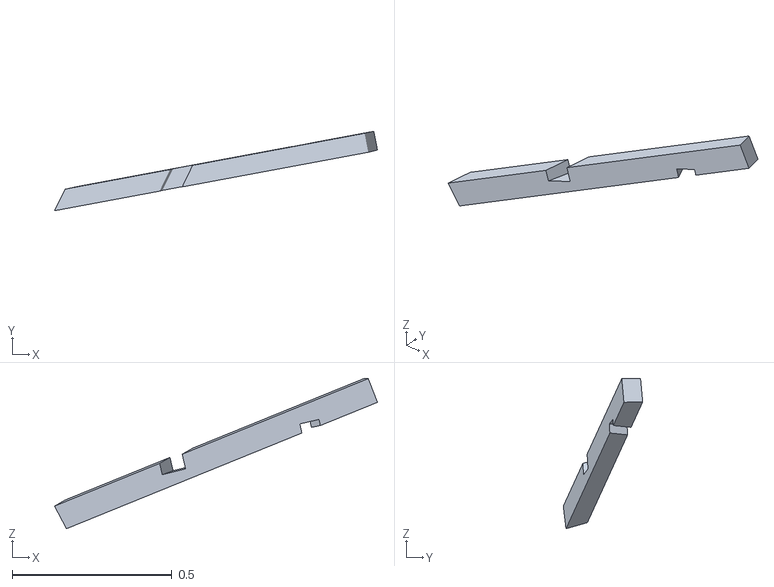
[picture p187: CAD file, 2026-06-04]
web_data/beam/d16/d16.stl
1.01 x 0.249 x 0.471
