gramaziokohler/coding_architecture_fs26_focus_work/web_data/beam/d17/d17.stl

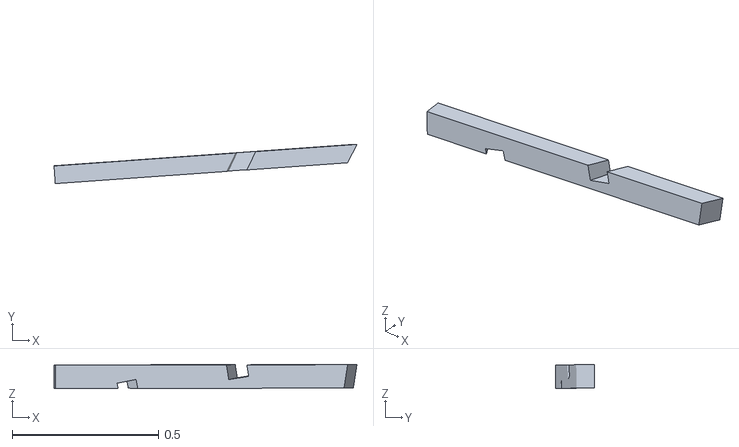
[picture p188: CAD file, 2026-06-04]
web_data/beam/d17/d17.stl
1.04 x 0.134 x 0.0828
