gramaziokohler/coding_architecture_fs26_focus_work/web_data/beam/d18/d18.stl

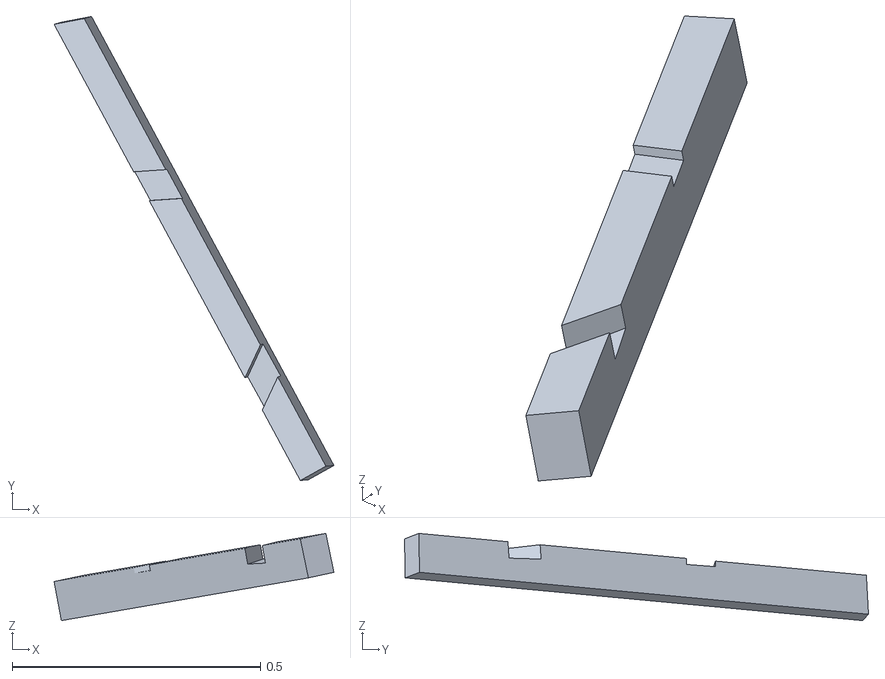
[picture p189: CAD file, 2026-06-04]
web_data/beam/d18/d18.stl
0.563 x 0.934 x 0.176
