gramaziokohler/coding_architecture_fs26_focus_work/web_data/beam/d19/d19.stl

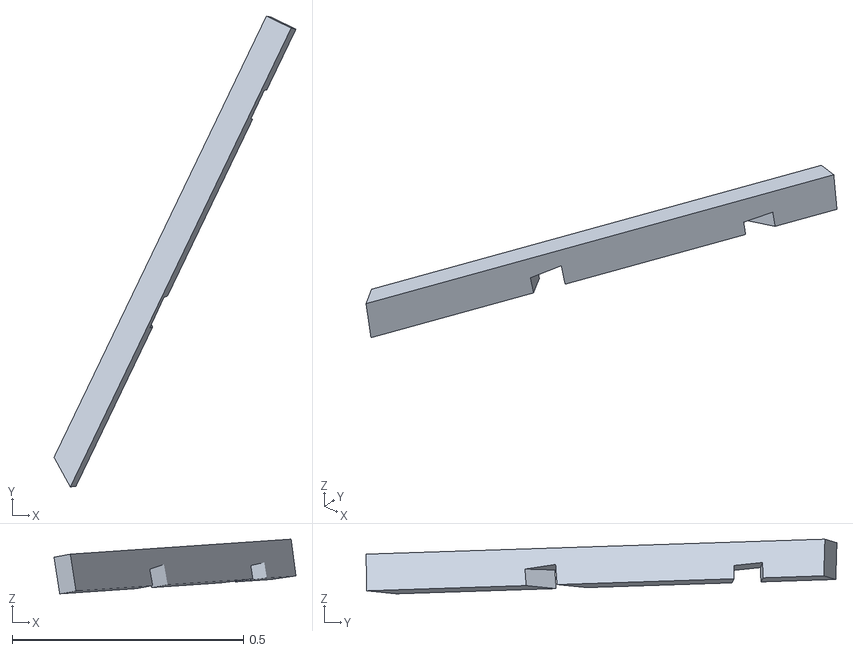
[picture p190: CAD file, 2026-06-04]
web_data/beam/d19/d19.stl
0.523 x 1.02 x 0.118
