gramaziokohler/coding_architecture_fs26_focus_work/web_data/beam/d2/d2.stl

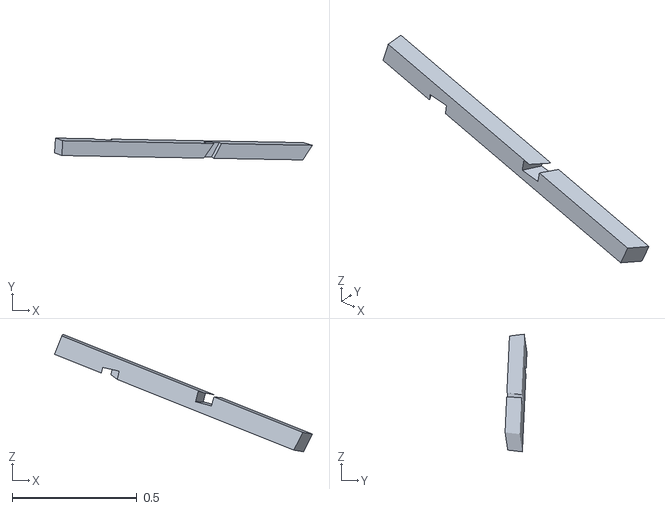
[picture p191: CAD file, 2026-06-04]
web_data/beam/d2/d2.stl
1.03 x 0.0879 x 0.472
