gramaziokohler/coding_architecture_fs26_focus_work/web_data/beam/d20/d20.stl

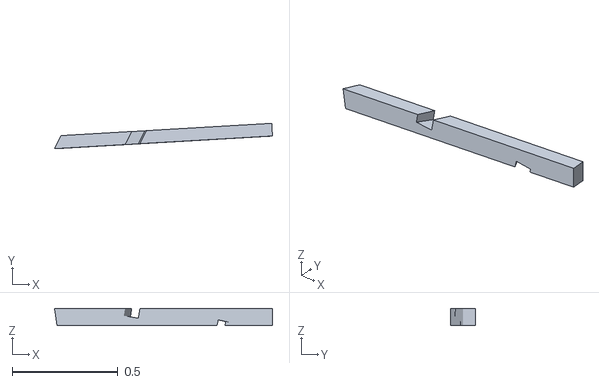
[picture p192: CAD file, 2026-06-04]
web_data/beam/d20/d20.stl
1.03 x 0.12 x 0.0813
