gramaziokohler/coding_architecture_fs26_focus_work/web_data/beam/d3/d3.stl

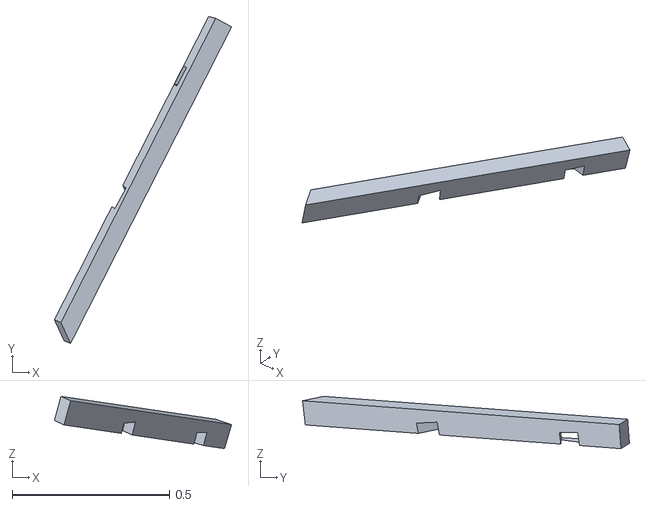
[picture p193: CAD file, 2026-06-04]
web_data/beam/d3/d3.stl
0.564 x 1.04 x 0.166
