gramaziokohler/coding_architecture_fs26_focus_work/web_data/beam/d4/d4.stl

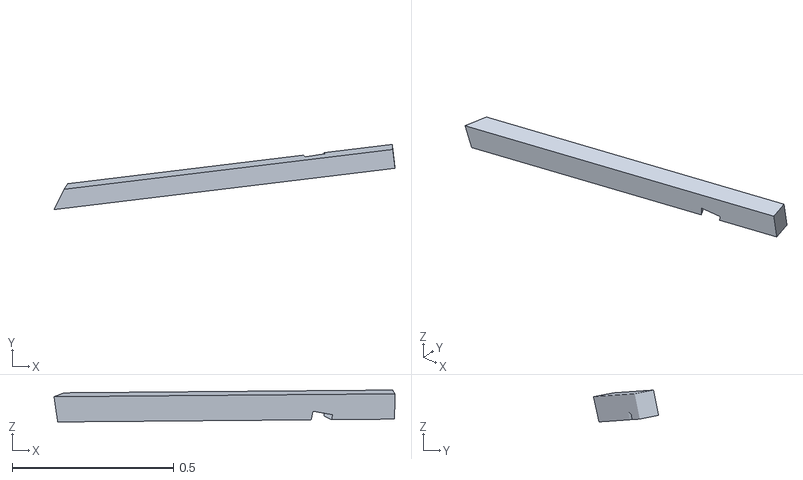
[picture p194: CAD file, 2026-06-04]
web_data/beam/d4/d4.stl
1.06 x 0.202 x 0.0991
