gramaziokohler/coding_architecture_fs26_focus_work/web_data/beam/d5/d5.stl

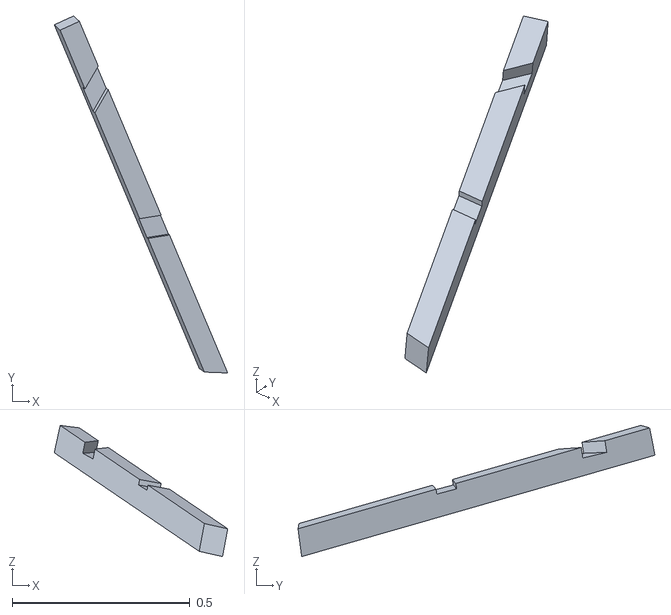
[picture p195: CAD file, 2026-06-04]
web_data/beam/d5/d5.stl
0.488 x 1.00 x 0.369
