gramaziokohler/coding_architecture_fs26_focus_work/web_data/beam/d6/d6.stl

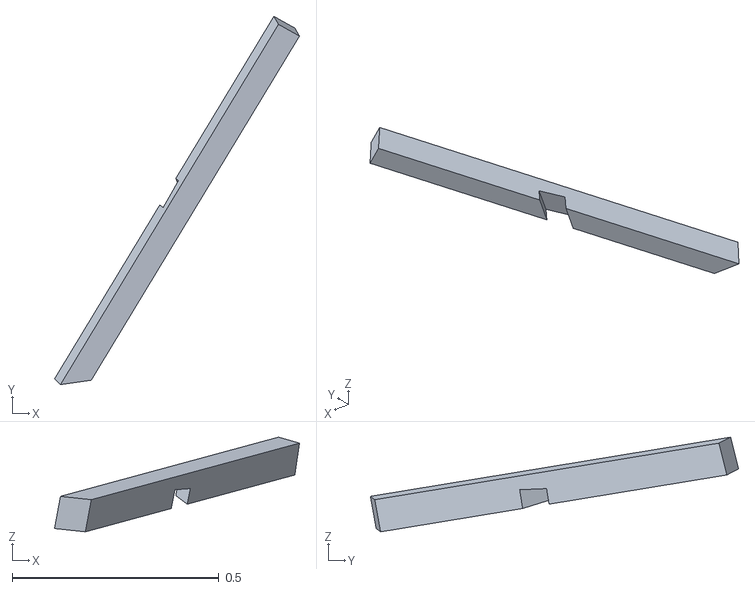
[picture p196: CAD file, 2026-06-04]
web_data/beam/d6/d6.stl
0.592 x 0.89 x 0.229
