gramaziokohler/coding_architecture_fs26_focus_work/web_data/beam/d7/d7.stl

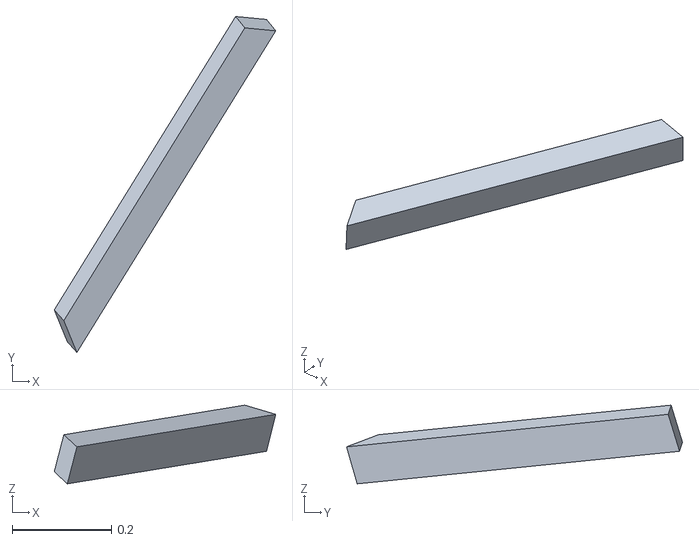
[picture p197: CAD file, 2026-06-04]
web_data/beam/d7/d7.stl
0.447 x 0.678 x 0.159
