gramaziokohler/coding_architecture_fs26_focus_work/web_data/beam/d8/d8.stl

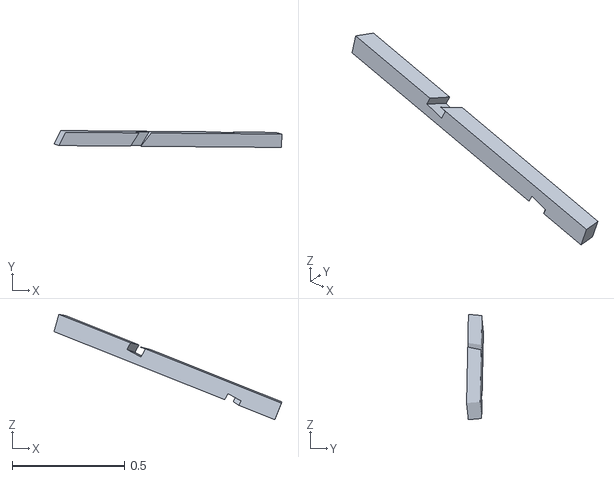
[picture p198: CAD file, 2026-06-04]
web_data/beam/d8/d8.stl
1.02 x 0.0757 x 0.47
