gramaziokohler/coding_architecture_fs26_focus_work/web_data/beam/d9/d9.stl

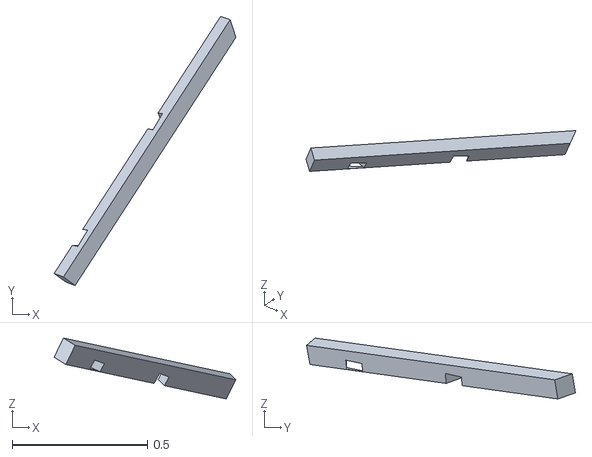
[picture p199: CAD file, 2026-06-04]
web_data/beam/d9/d9.stl
0.673 x 0.995 x 0.225
