gramaziokohler/coding_architecture_fs26_focus_work/web_data/beam/e1/e1.stl

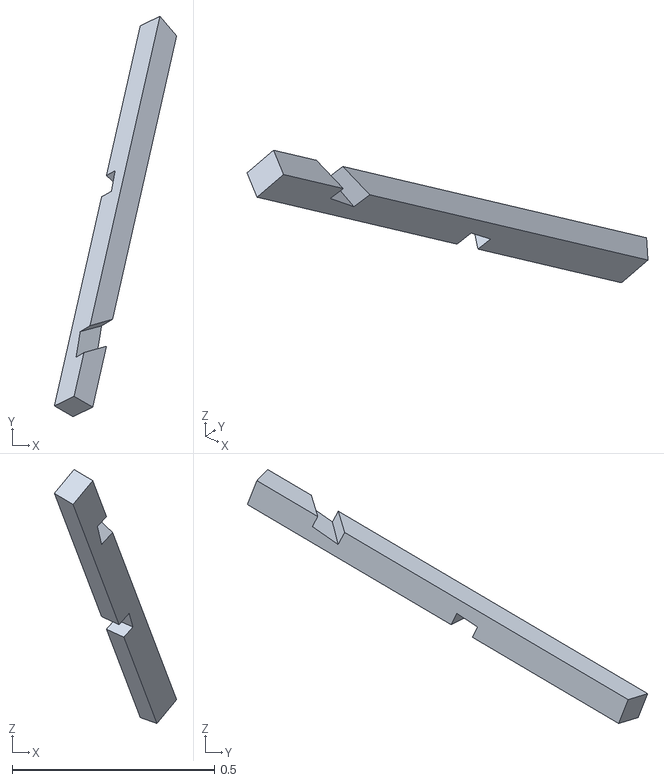
[picture p200: CAD file, 2026-06-04]
web_data/beam/e1/e1.stl
0.302 x 0.989 x 0.627
