gramaziokohler/coding_architecture_fs26_focus_work/web_data/beam/e10/e10.stl

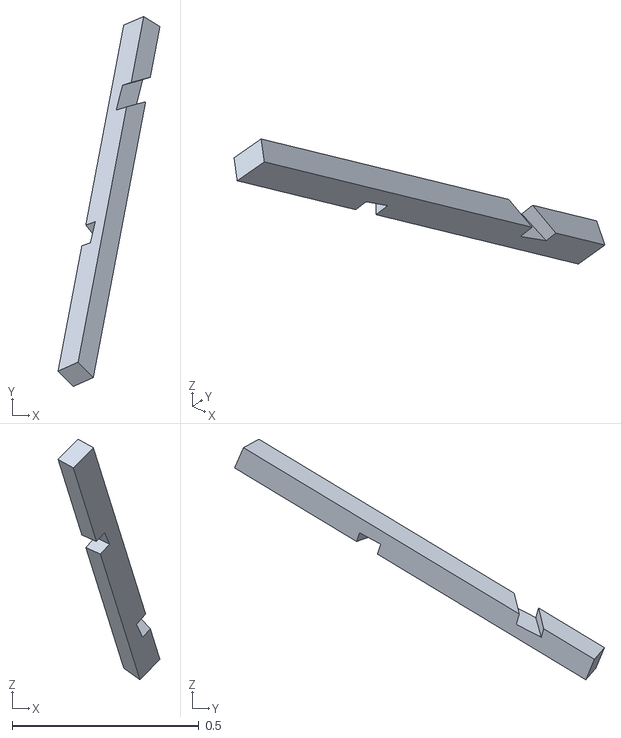
[picture p201: CAD file, 2026-06-04]
web_data/beam/e10/e10.stl
0.273 x 0.991 x 0.644
