gramaziokohler/coding_architecture_fs26_focus_work/web_data/beam/e11/e11.stl

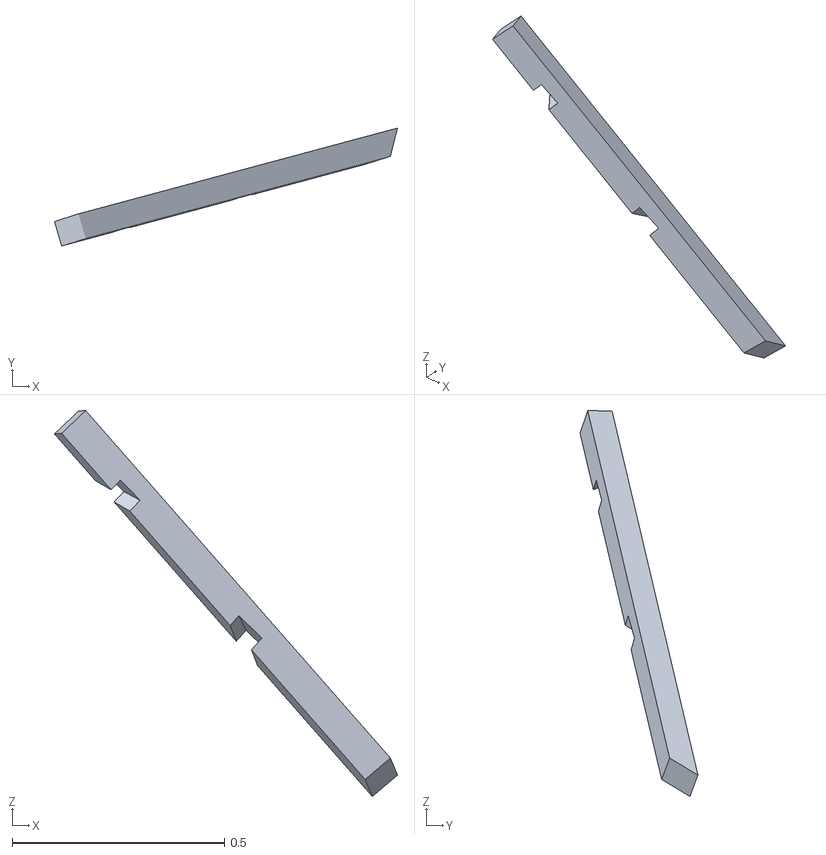
[picture p202: CAD file, 2026-06-04]
web_data/beam/e11/e11.stl
0.808 x 0.278 x 0.909
