gramaziokohler/coding_architecture_fs26_focus_work/web_data/beam/e12/e12.stl

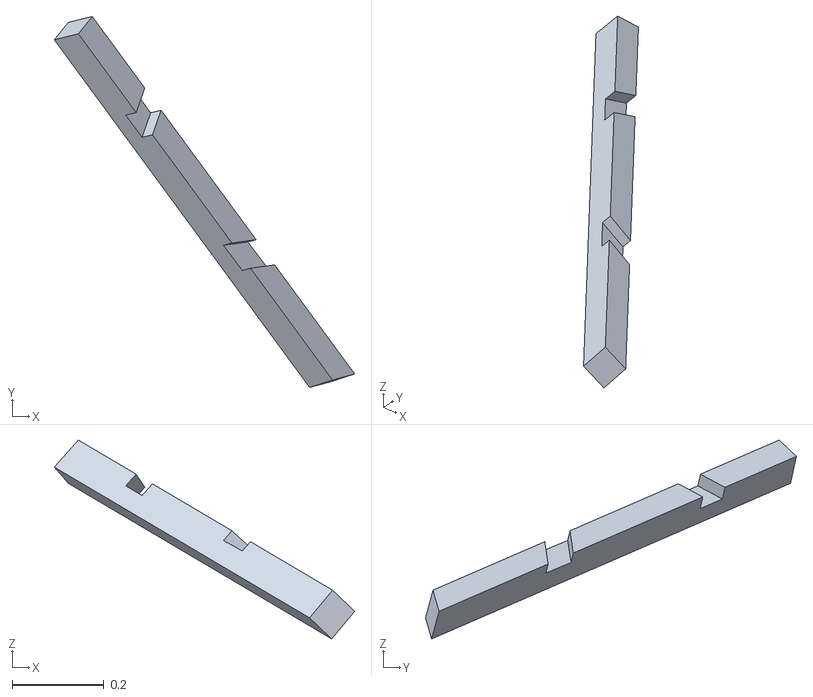
[picture p203: CAD file, 2026-06-04]
web_data/beam/e12/e12.stl
0.655 x 0.809 x 0.434
