gramaziokohler/coding_architecture_fs26_focus_work/web_data/beam/e13/e13.stl

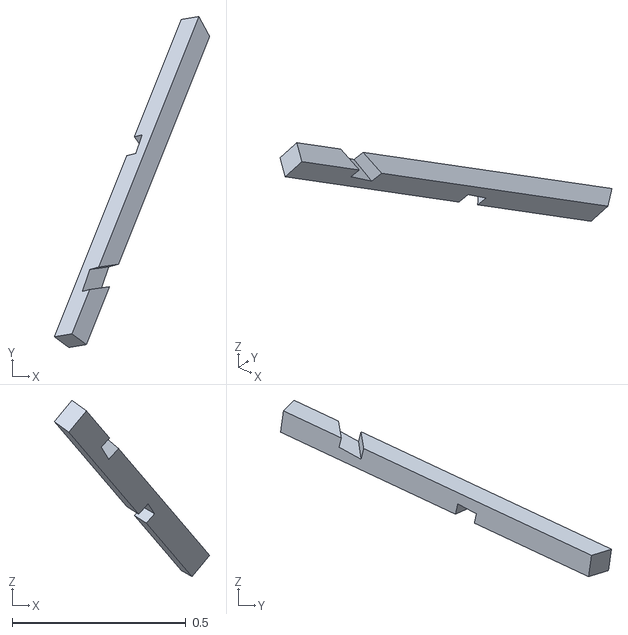
[picture p204: CAD file, 2026-06-04]
web_data/beam/e13/e13.stl
0.447 x 0.952 x 0.507
