gramaziokohler/coding_architecture_fs26_focus_work/web_data/beam/e14/e14.stl

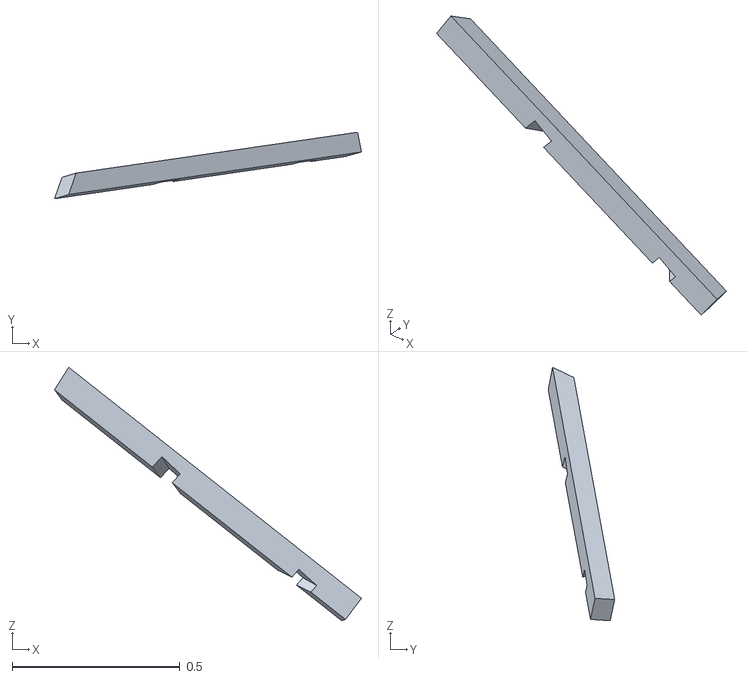
[picture p205: CAD file, 2026-06-04]
web_data/beam/e14/e14.stl
0.914 x 0.198 x 0.755
