gramaziokohler/coding_architecture_fs26_focus_work/web_data/beam/e15/e15.stl

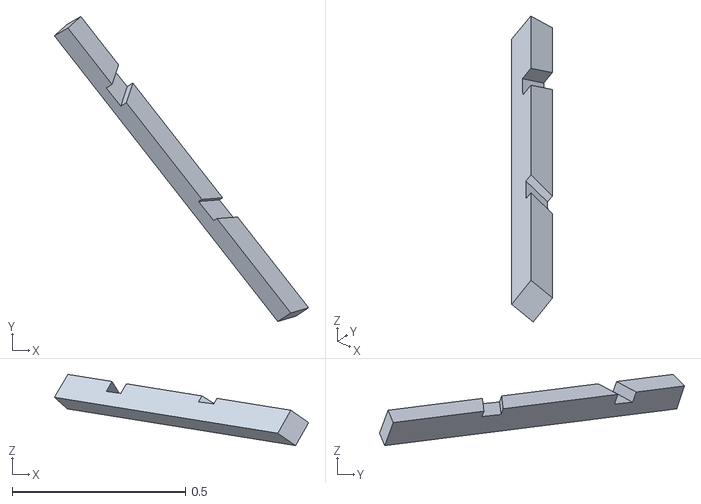
[picture p206: CAD file, 2026-06-04]
web_data/beam/e15/e15.stl
0.733 x 0.879 x 0.205
