gramaziokohler/coding_architecture_fs26_focus_work/web_data/beam/e16/e16.stl

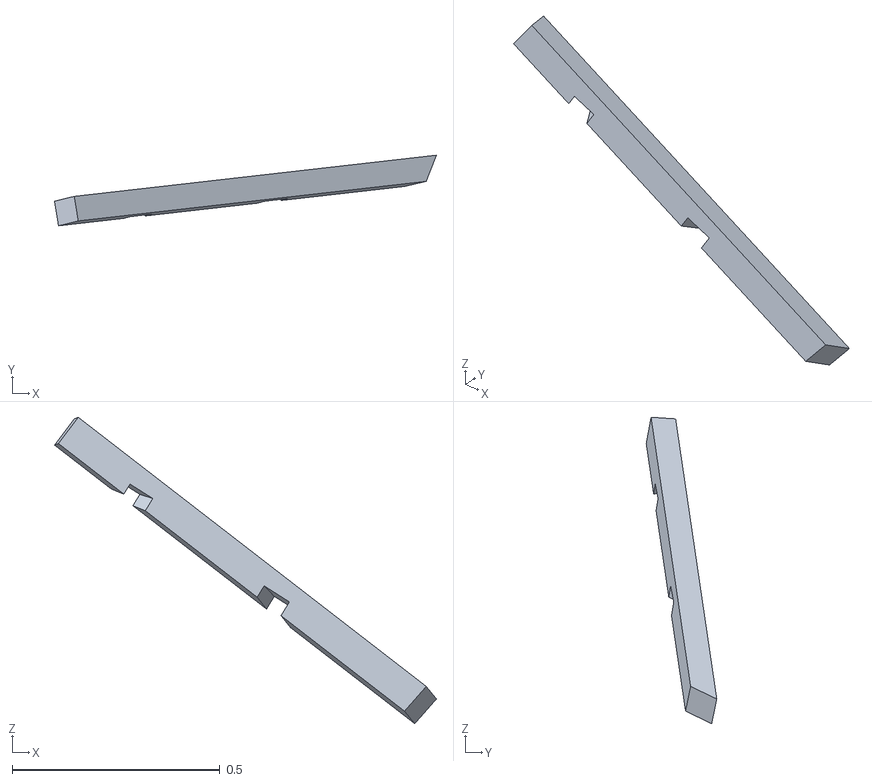
[picture p207: CAD file, 2026-06-04]
web_data/beam/e16/e16.stl
0.92 x 0.17 x 0.738
