gramaziokohler/coding_architecture_fs26_focus_work/web_data/beam/e17/e17.stl

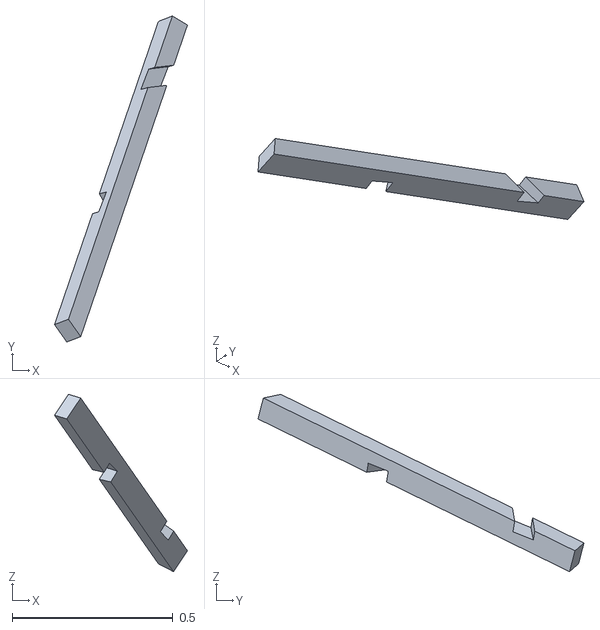
[picture p208: CAD file, 2026-06-04]
web_data/beam/e17/e17.stl
0.414 x 1.01 x 0.552
