gramaziokohler/coding_architecture_fs26_focus_work/web_data/beam/e18/e18.stl

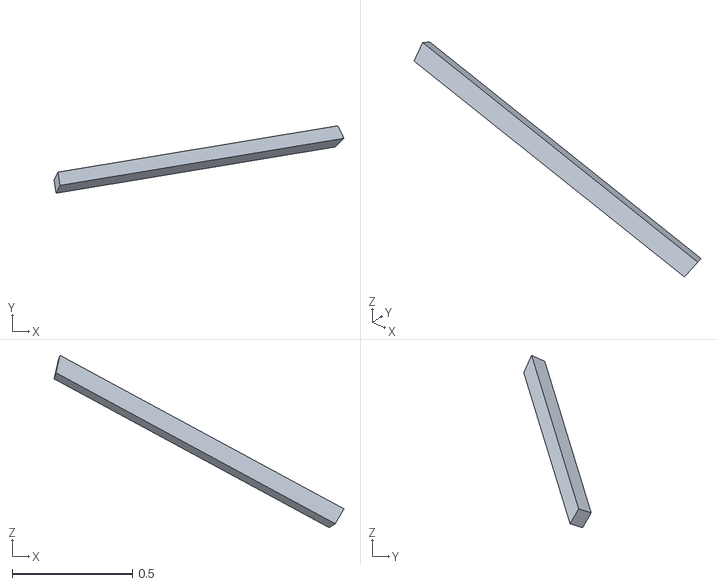
[picture p209: CAD file, 2026-06-04]
web_data/beam/e18/e18.stl
1.21 x 0.281 x 0.718
