gramaziokohler/coding_architecture_fs26_focus_work/web_data/beam/e19/e19.stl

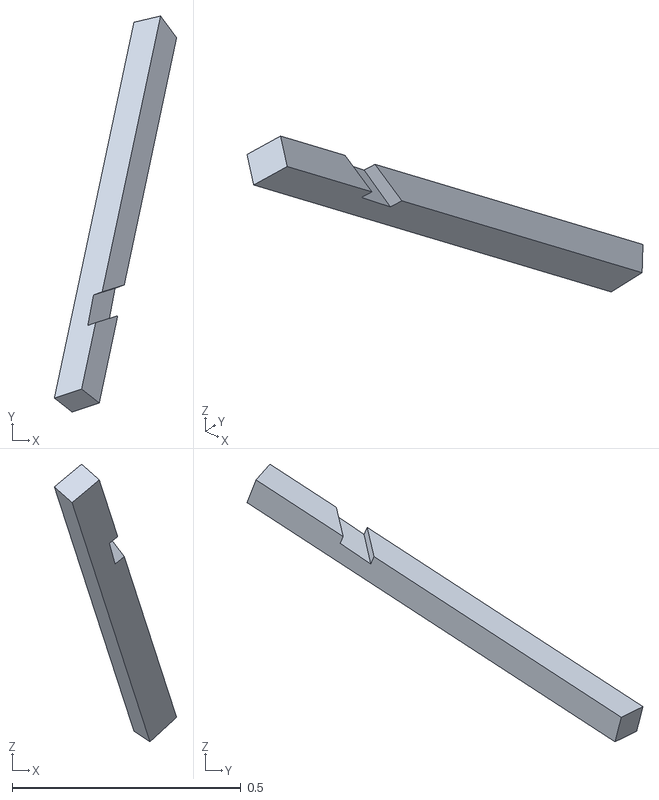
[picture p210: CAD file, 2026-06-04]
web_data/beam/e19/e19.stl
0.267 x 0.865 x 0.607
