gramaziokohler/coding_architecture_fs26_focus_work/web_data/beam/e2/e2.stl

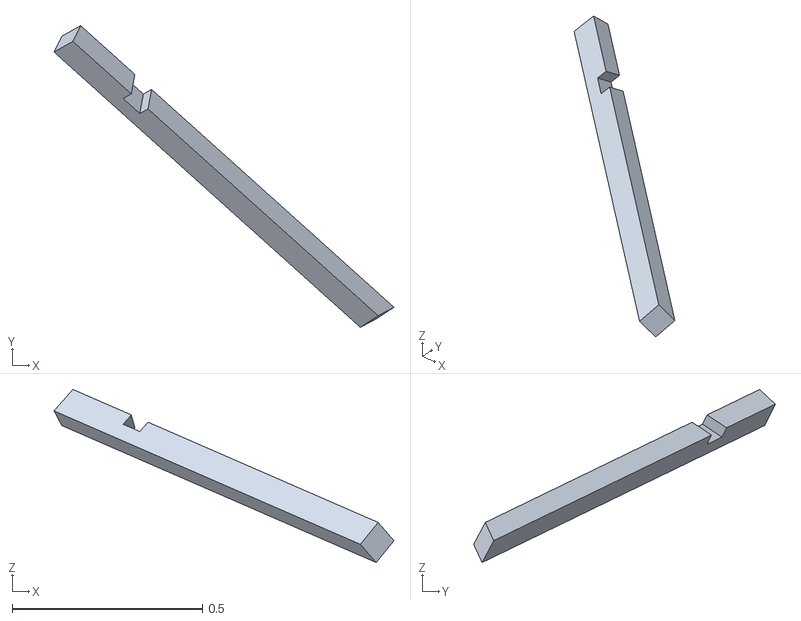
[picture p211: CAD file, 2026-06-04]
web_data/beam/e2/e2.stl
0.893 x 0.792 x 0.454
