gramaziokohler/coding_architecture_fs26_focus_work/web_data/beam/e20/e20.stl

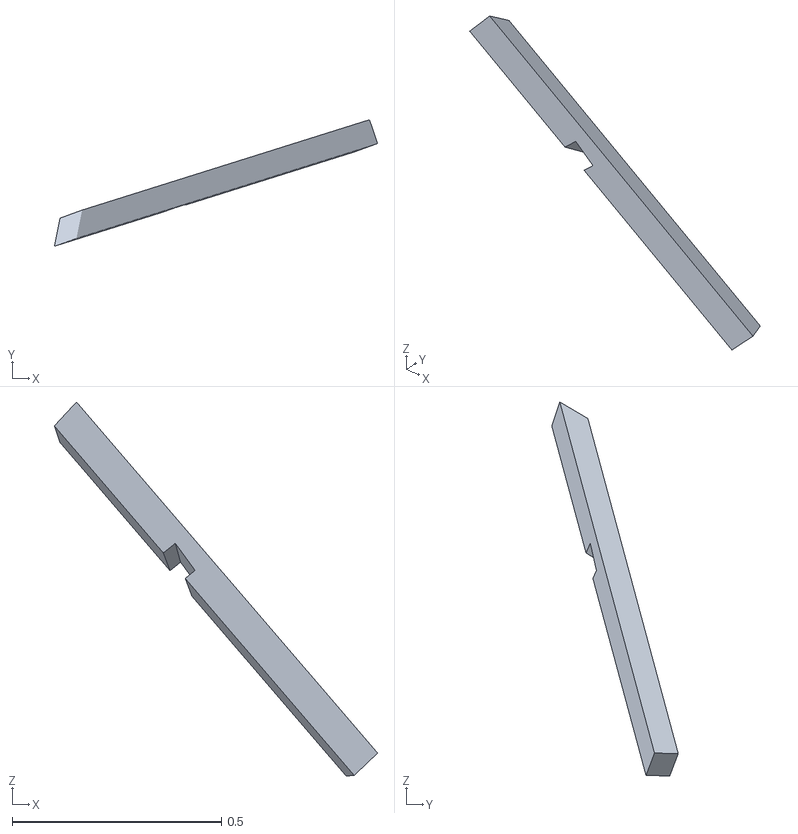
[picture p212: CAD file, 2026-06-04]
web_data/beam/e20/e20.stl
0.772 x 0.302 x 0.893
