gramaziokohler/coding_architecture_fs26_focus_work/web_data/beam/e21/e21.stl

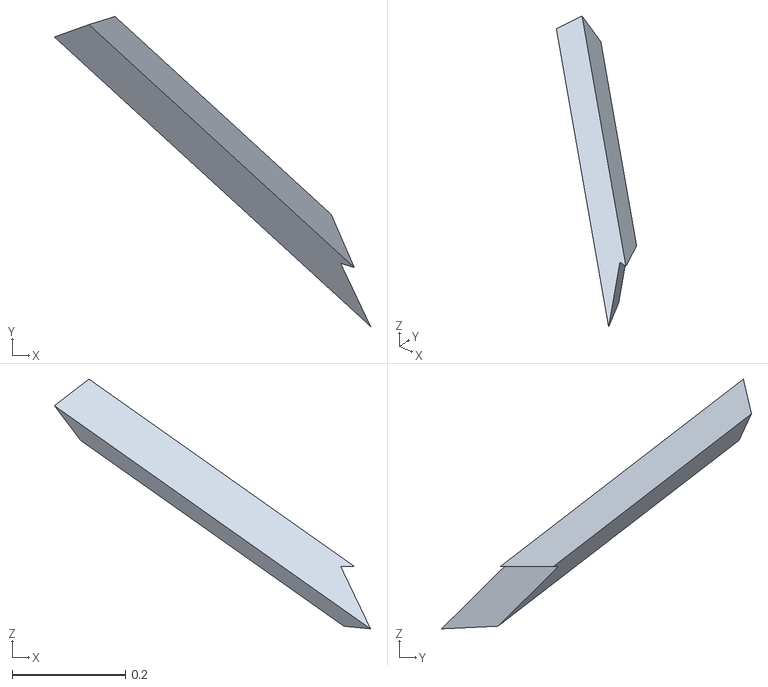
[picture p213: CAD file, 2026-06-04]
web_data/beam/e21/e21.stl
0.559 x 0.548 x 0.442
