gramaziokohler/coding_architecture_fs26_focus_work/web_data/beam/e22/e22.stl

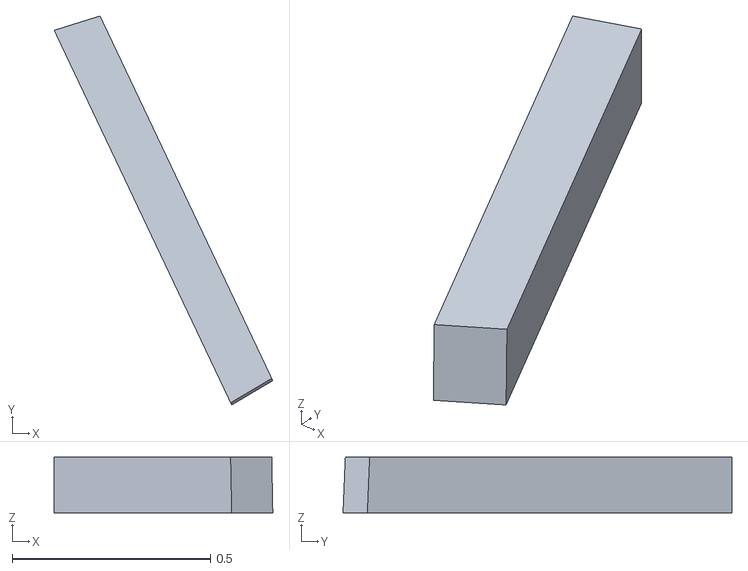
[picture p214: CAD file, 2026-06-04]
web_data/beam/e22/e22.stl
0.551 x 0.981 x 0.14
