gramaziokohler/coding_architecture_fs26_focus_work/web_data/beam/e23/e23.stl

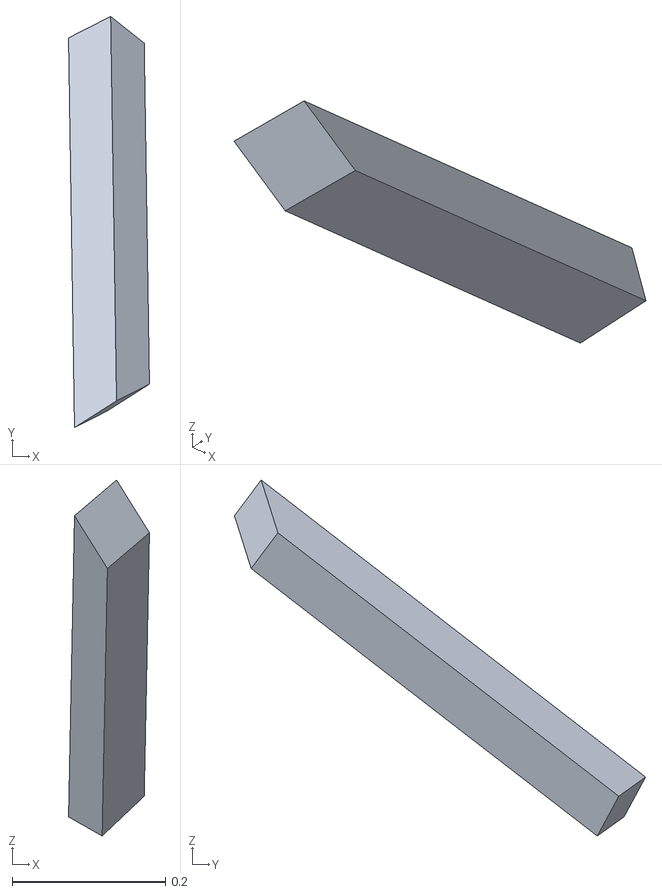
[picture p215: CAD file, 2026-06-04]
web_data/beam/e23/e23.stl
0.106 x 0.536 x 0.464
