gramaziokohler/coding_architecture_fs26_focus_work/web_data/beam/e24/e24.stl

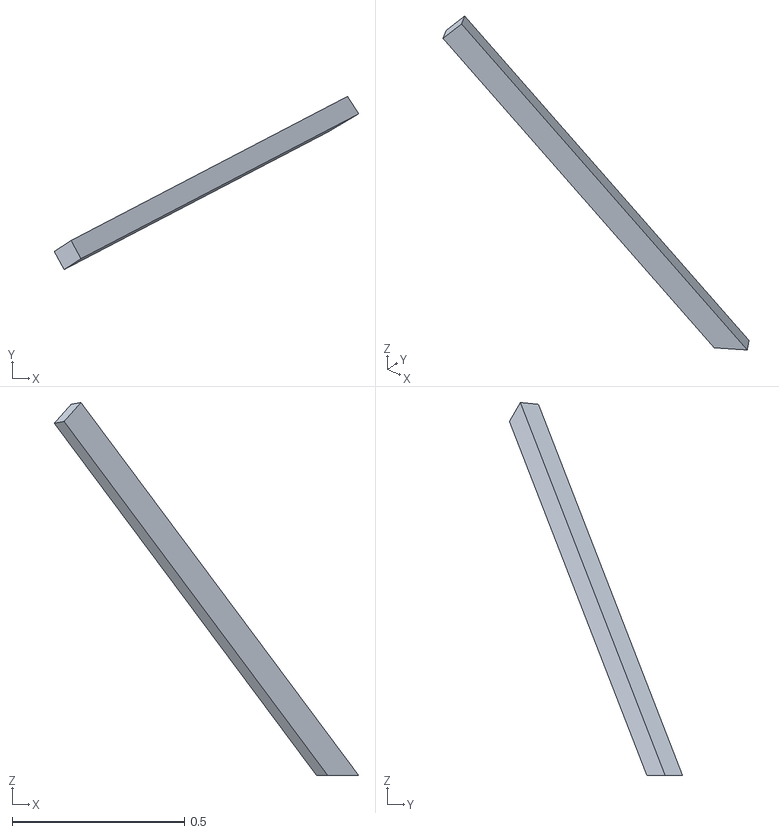
[picture p216: CAD file, 2026-06-04]
web_data/beam/e24/e24.stl
0.883 x 0.502 x 1.08
