gramaziokohler/coding_architecture_fs26_focus_work/web_data/beam/e25/e25.stl

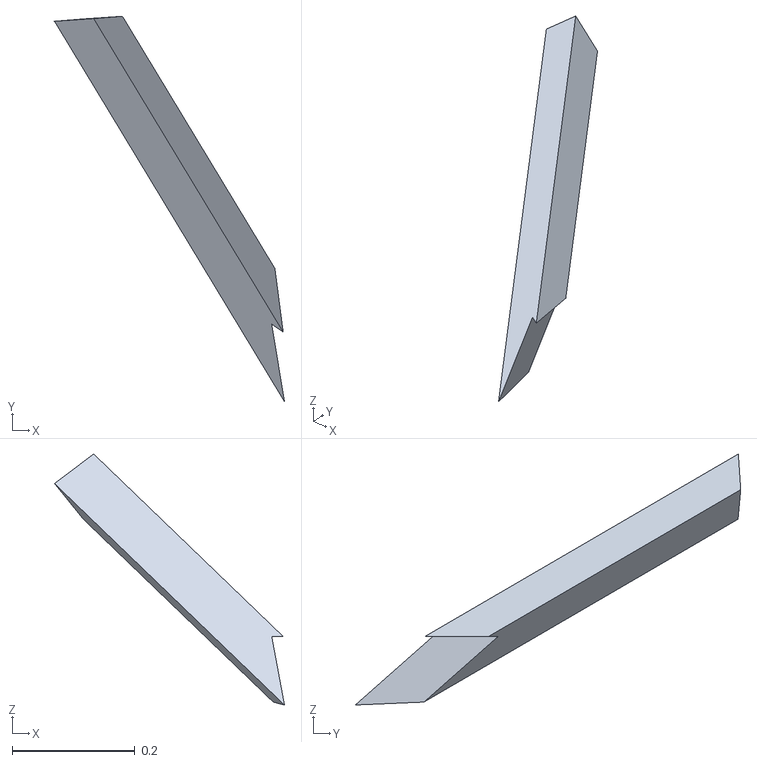
[picture p217: CAD file, 2026-06-04]
web_data/beam/e25/e25.stl
0.375 x 0.629 x 0.409
