gramaziokohler/coding_architecture_fs26_focus_work/web_data/beam/e26/e26.stl

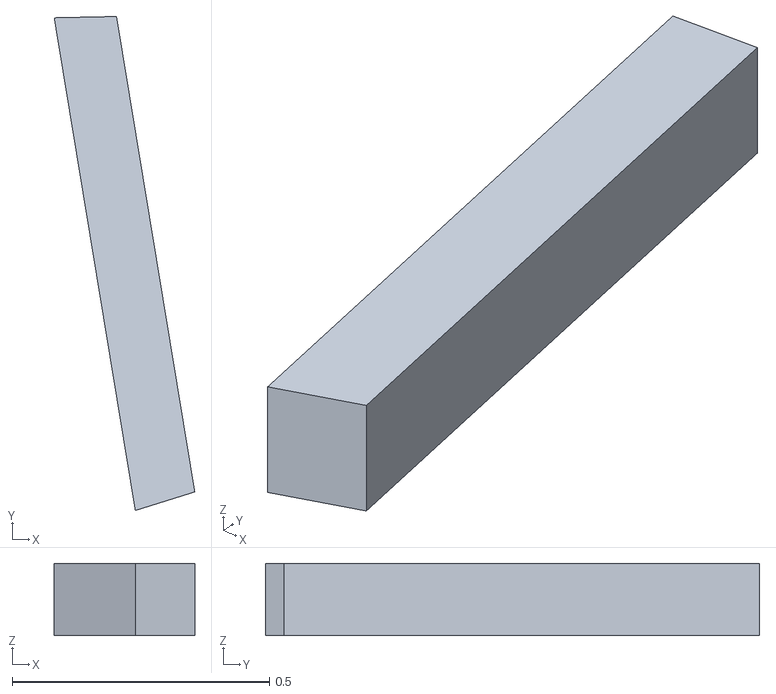
[picture p218: CAD file, 2026-06-04]
web_data/beam/e26/e26.stl
0.273 x 0.96 x 0.14
