gramaziokohler/coding_architecture_fs26_focus_work/web_data/beam/e27/e27.stl

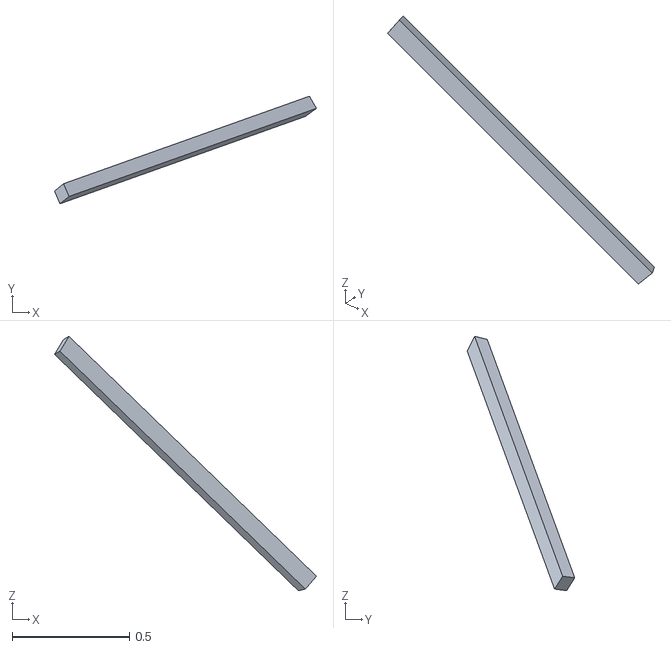
[picture p219: CAD file, 2026-06-04]
web_data/beam/e27/e27.stl
1.12 x 0.458 x 1.08
