gramaziokohler/coding_architecture_fs26_focus_work/web_data/beam/e3/e3.stl

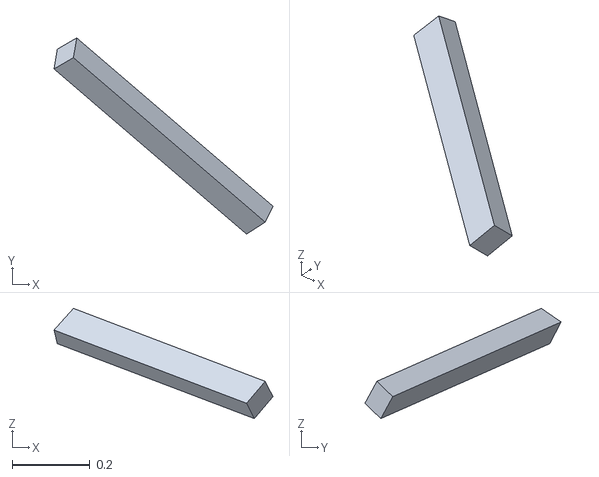
[picture p220: CAD file, 2026-06-04]
web_data/beam/e3/e3.stl
0.562 x 0.503 x 0.283
