gramaziokohler/coding_architecture_fs26_focus_work/web_data/beam/e4/e4.stl

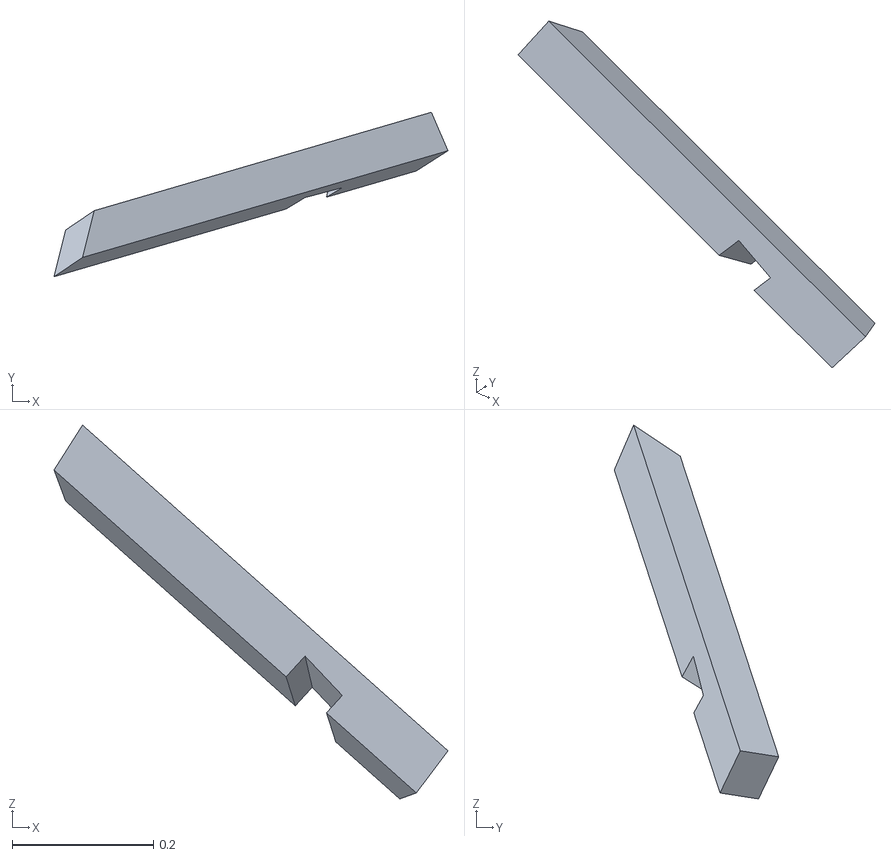
[picture p221: CAD file, 2026-06-04]
web_data/beam/e4/e4.stl
0.558 x 0.233 x 0.53
