gramaziokohler/coding_architecture_fs26_focus_work/web_data/beam/e5/e5.stl

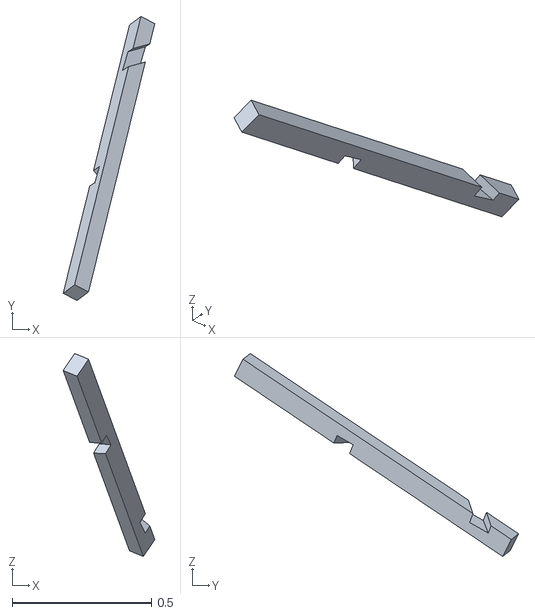
[picture p222: CAD file, 2026-06-04]
web_data/beam/e5/e5.stl
0.33 x 1.02 x 0.73
