gramaziokohler/coding_architecture_fs26_focus_work/web_data/beam/e6/e6.stl

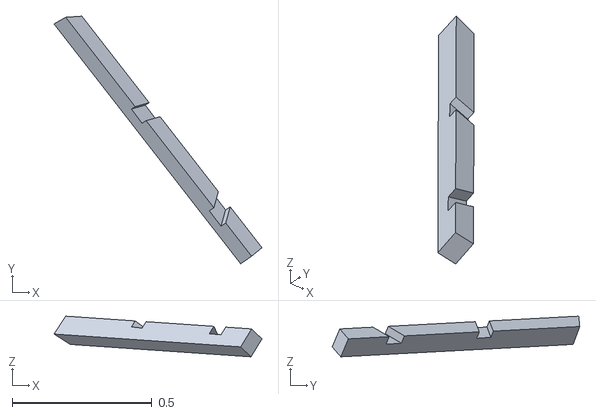
[picture p223: CAD file, 2026-06-04]
web_data/beam/e6/e6.stl
0.744 x 0.886 x 0.146
