gramaziokohler/coding_architecture_fs26_focus_work/web_data/beam/e7/e7.stl

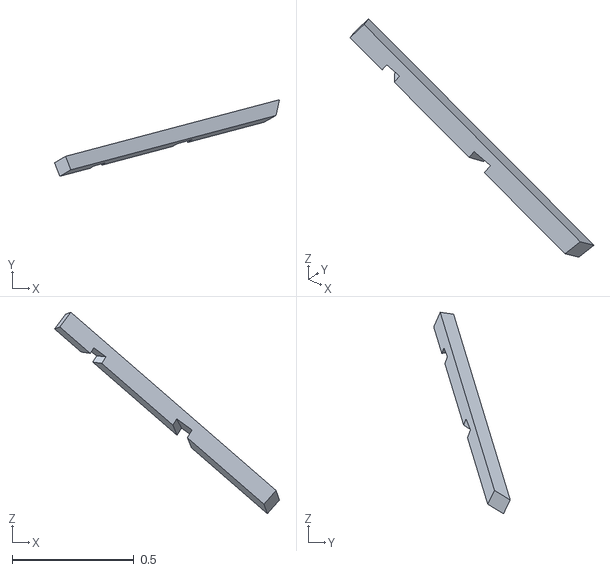
[picture p224: CAD file, 2026-06-04]
web_data/beam/e7/e7.stl
0.923 x 0.314 x 0.827
