gramaziokohler/coding_architecture_fs26_focus_work/web_data/beam/e8/e8.stl

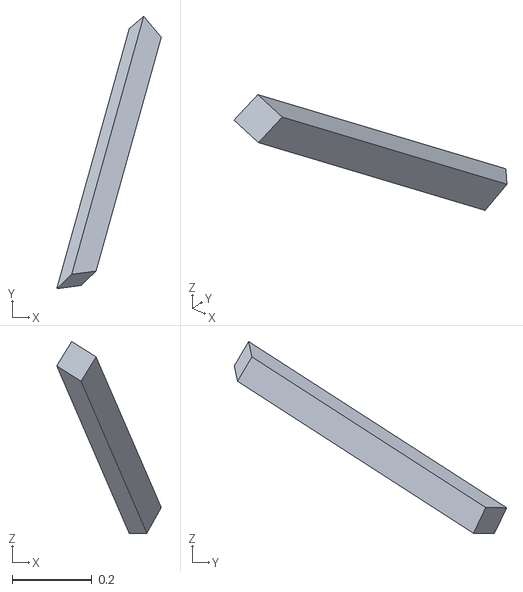
[picture p225: CAD file, 2026-06-04]
web_data/beam/e8/e8.stl
0.262 x 0.682 x 0.48
