gramaziokohler/coding_architecture_fs26_focus_work/web_data/beam/e9/e9.stl

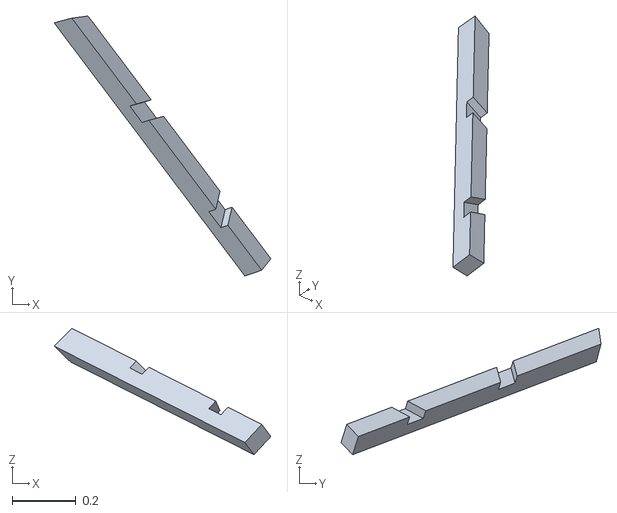
[picture p226: CAD file, 2026-06-04]
web_data/beam/e9/e9.stl
0.681 x 0.816 x 0.397
