gramaziokohler/coding_architecture_fs26_focus_work/web_data/beam/f1/f1.stl

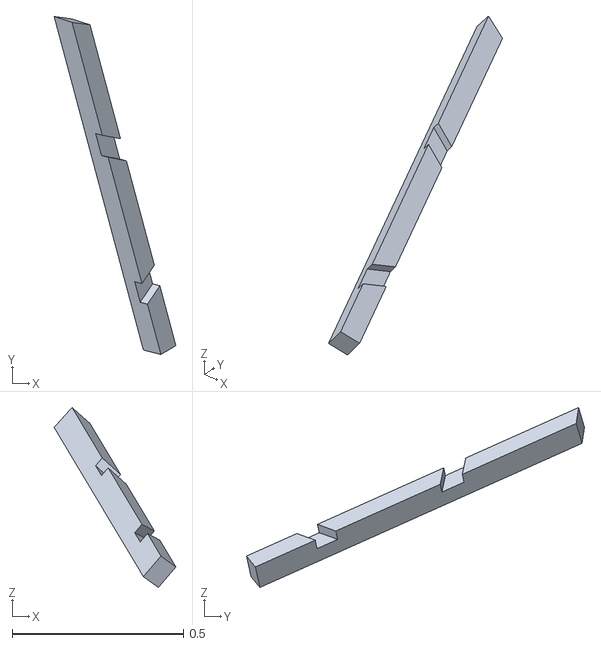
[picture p227: CAD file, 2026-06-04]
web_data/beam/f1/f1.stl
0.356 x 0.987 x 0.526
