gramaziokohler/coding_architecture_fs26_focus_work/web_data/beam/f10/f10.stl

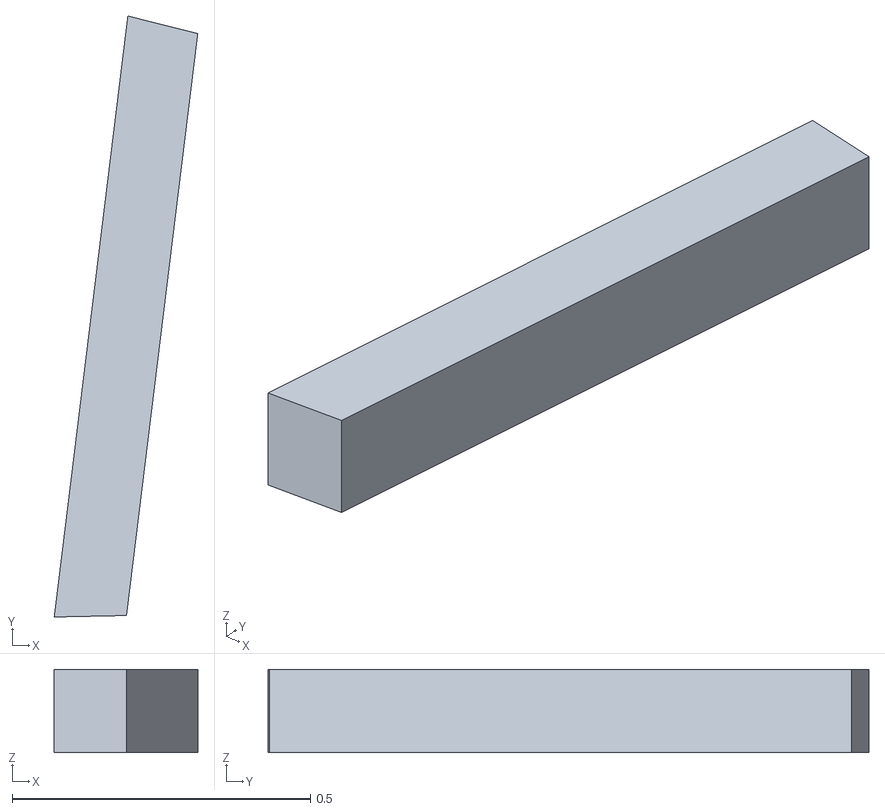
[picture p228: CAD file, 2026-06-04]
web_data/beam/f10/f10.stl
0.241 x 1.01 x 0.14
