gramaziokohler/coding_architecture_fs26_focus_work/web_data/beam/f11/f11.stl

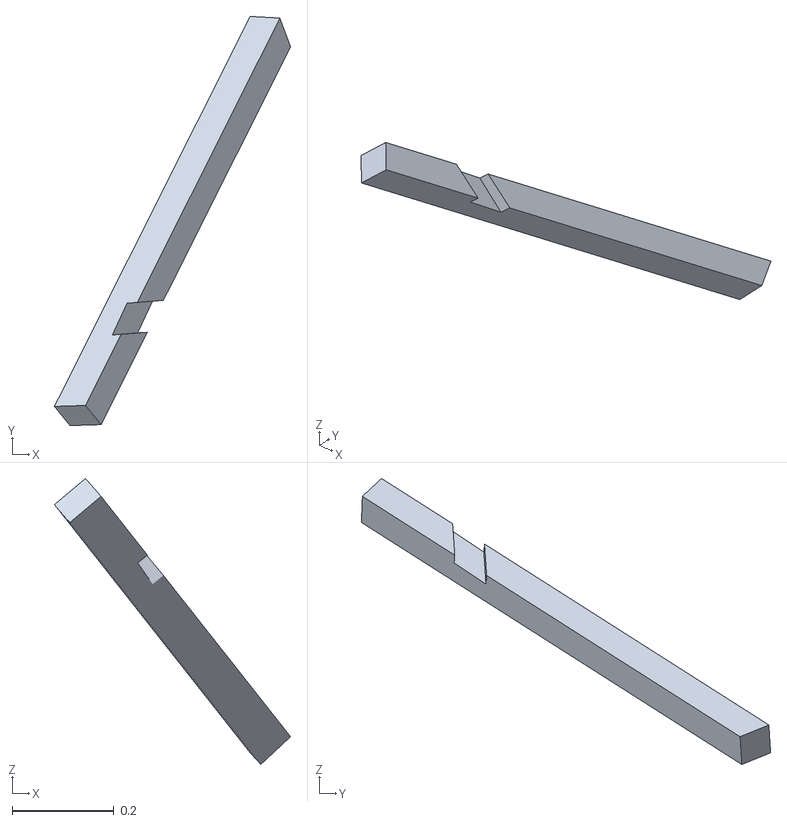
[picture p229: CAD file, 2026-06-04]
web_data/beam/f11/f11.stl
0.465 x 0.806 x 0.563
