gramaziokohler/coding_architecture_fs26_focus_work/web_data/beam/f12/f12.stl

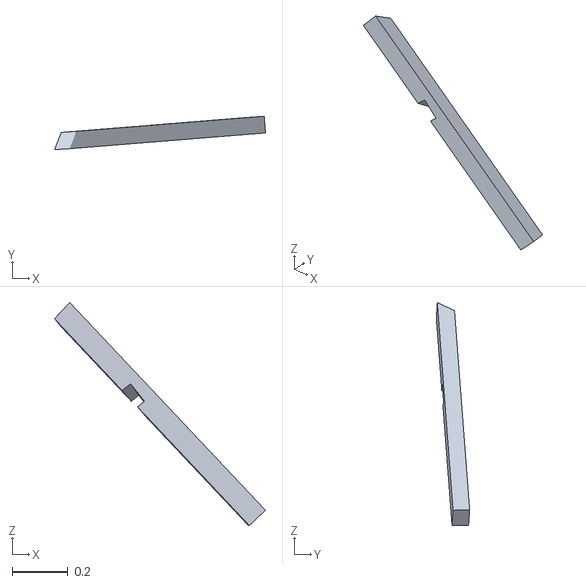
[picture p230: CAD file, 2026-06-04]
web_data/beam/f12/f12.stl
0.76 x 0.12 x 0.803
