gramaziokohler/coding_architecture_fs26_focus_work/web_data/beam/f13/f13.stl

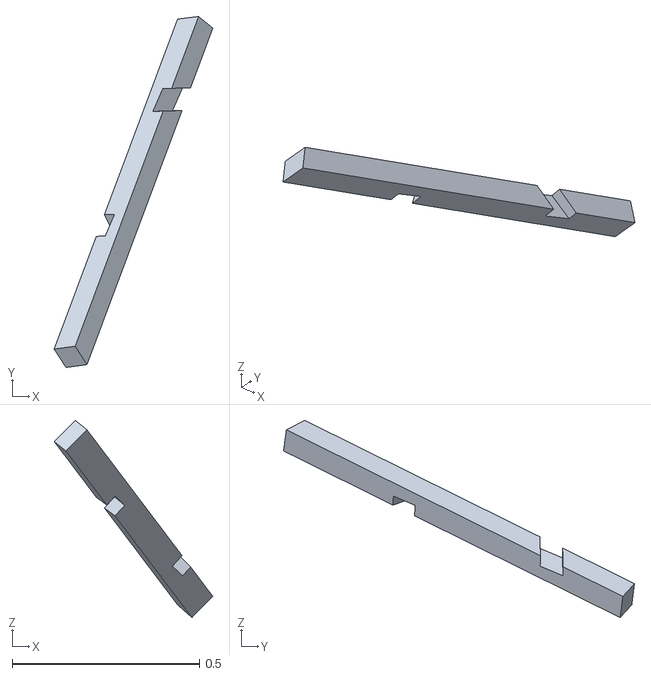
[picture p231: CAD file, 2026-06-04]
web_data/beam/f13/f13.stl
0.424 x 0.937 x 0.527
