gramaziokohler/coding_architecture_fs26_focus_work/web_data/beam/f14/f14.stl

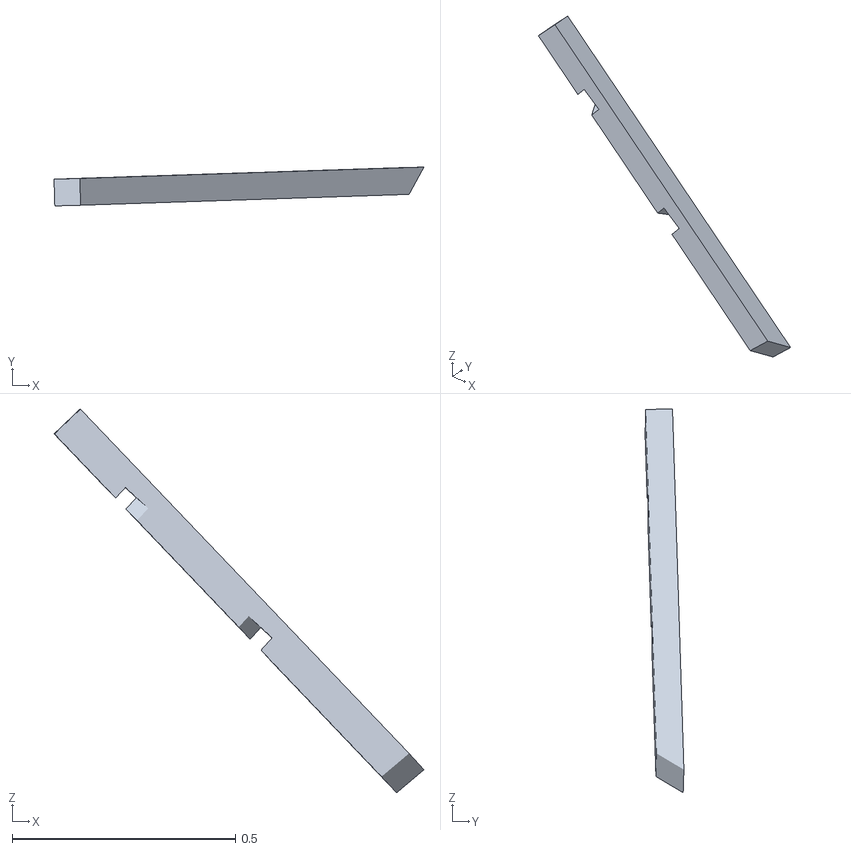
[picture p232: CAD file, 2026-06-04]
web_data/beam/f14/f14.stl
0.829 x 0.0871 x 0.859
