gramaziokohler/coding_architecture_fs26_focus_work/Dokumentation/Group A/Base Beams Issues.png

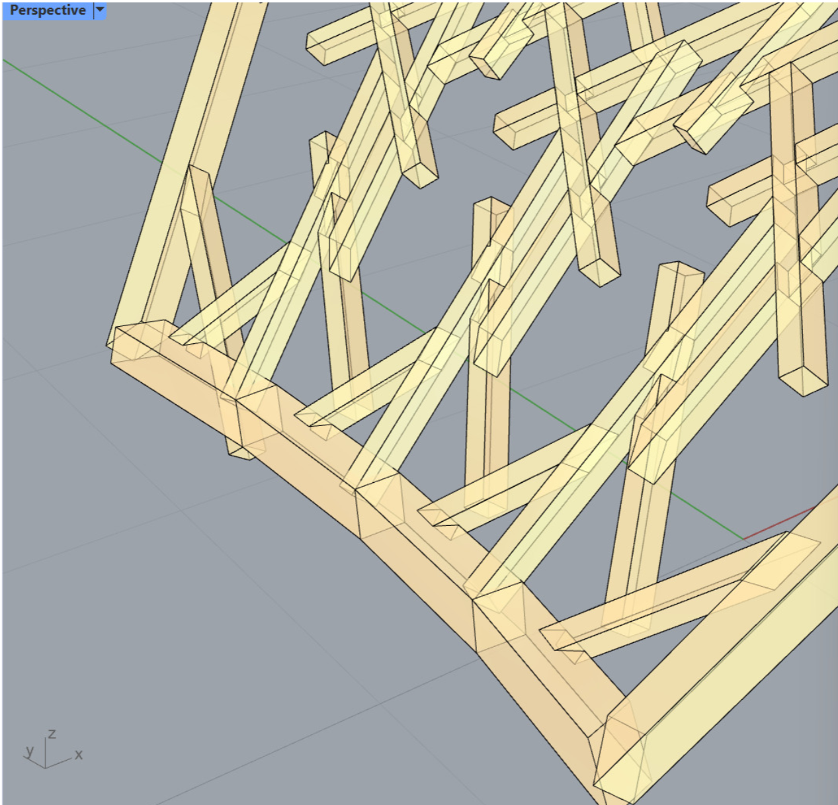
Dokumentation/Group A/Base Beams Issues.png
