gramaziokohler/coding_architecture_fs26_focus_work/Dokumentation/Group A/Booklet_focuswork_2406 Folder/Links/unterbaugruppe.pdf

## TOP VIEW M1:5

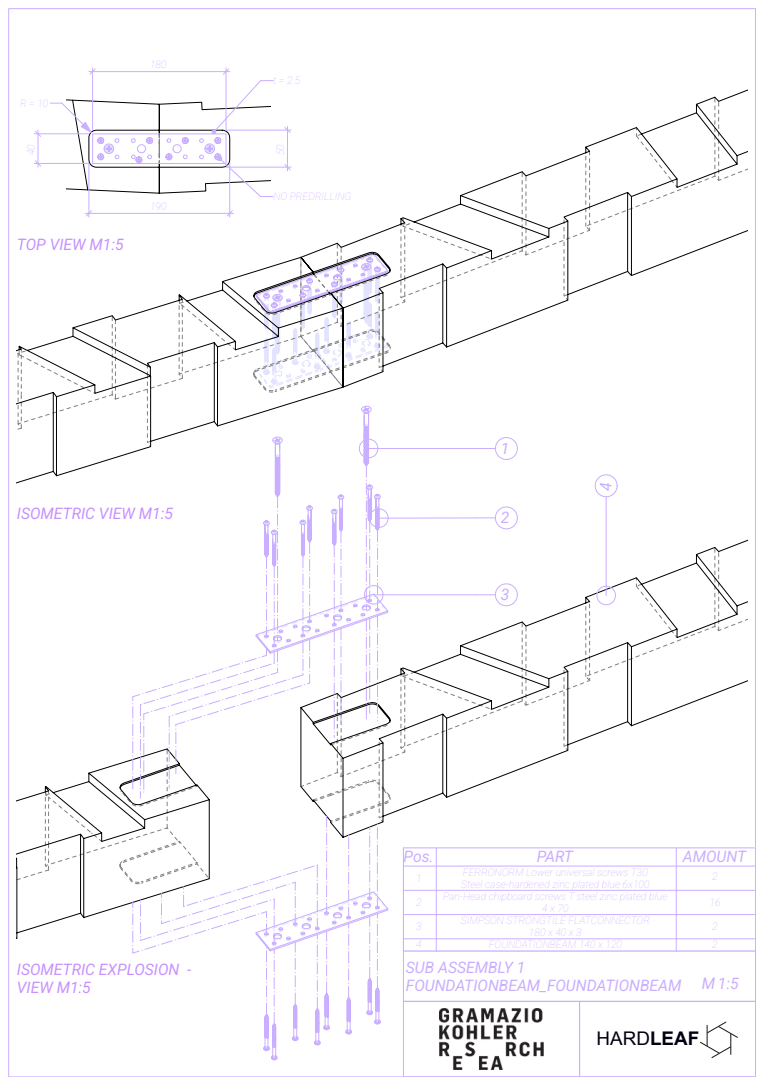
[picture p245: page 1]
NO PREDRILLING; FOUNDATIONBEAM_FOUNDATIONBEAM M 1:5; SUB ASSEMBLY 1; HARDLEAF; PART; AMOUNT; Steel case-hardened zinc plated blue 6x100; Pan-Head chipboard screws T steel zinc plated blue; FOUNDATIONBEAM 140 x 120; Pos.; ISOMETRIC EXPLOSION - VIEW M1:5; ISOMETRIC VIEW M1:5

FERRONORM Lower universal screws T30

SIMPSON STRONGTILE FLATCONNECTOR

1
2

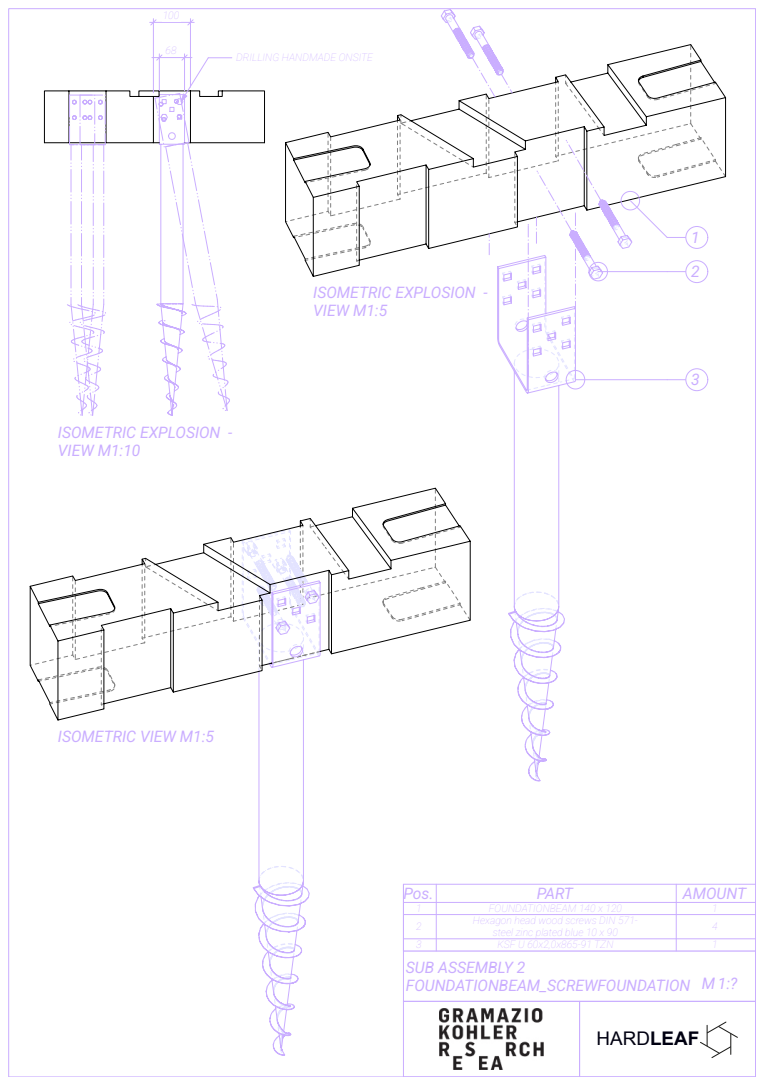
[picture p246: page 2]
DRILLING HANDMADE ONSITE; FOUNDATIONBEAM_SCREWFOUNDATION M 1:?; SUB ASSEMBLY 2; ISOMETRIC VIEW M1:5; ISOMETRIC EXPLOSION - VIEW M1:5; ISOMETRIC EXPLOSION - VIEW M1:10; PART; FOUNDATIONBEAM 140 x 120; steel zinc plated blue 10 x 90; KSF U 60x2,0x865-91 TZN; Pos. 1 2 3; AMOUNT

Hexagon head wood screws DIN 571-

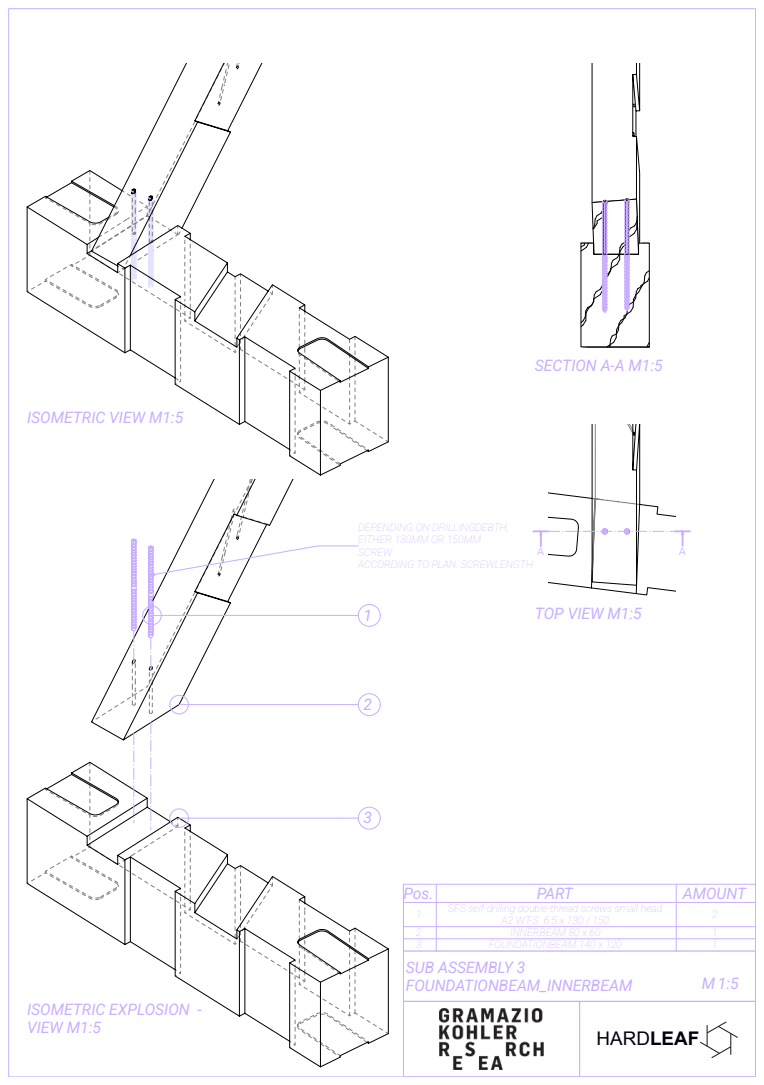
[picture p247: page 3]
Schnitt A-A; FOUNDATIONBEAM_INNERBEAM; SUB ASSEMBLY 3; ISOMETRIC EXPLOSION - VIEW M1:5; ISOMETRIC VIEW M1:5; SECTION A-A M1:5; TOP VIEW M1:5; PART; INNERBEAM 80 x 60; FOUNDATIONBEAM 140 x 120; Pos.; AMOUNT

DEPENDING ON DRILLINGDEBTH,
EITHER 130MM OR 150MM
SCREW
ACCORDING TO PLAN: SCREWLENGTH

SFS self-drilling double-thread screws small head

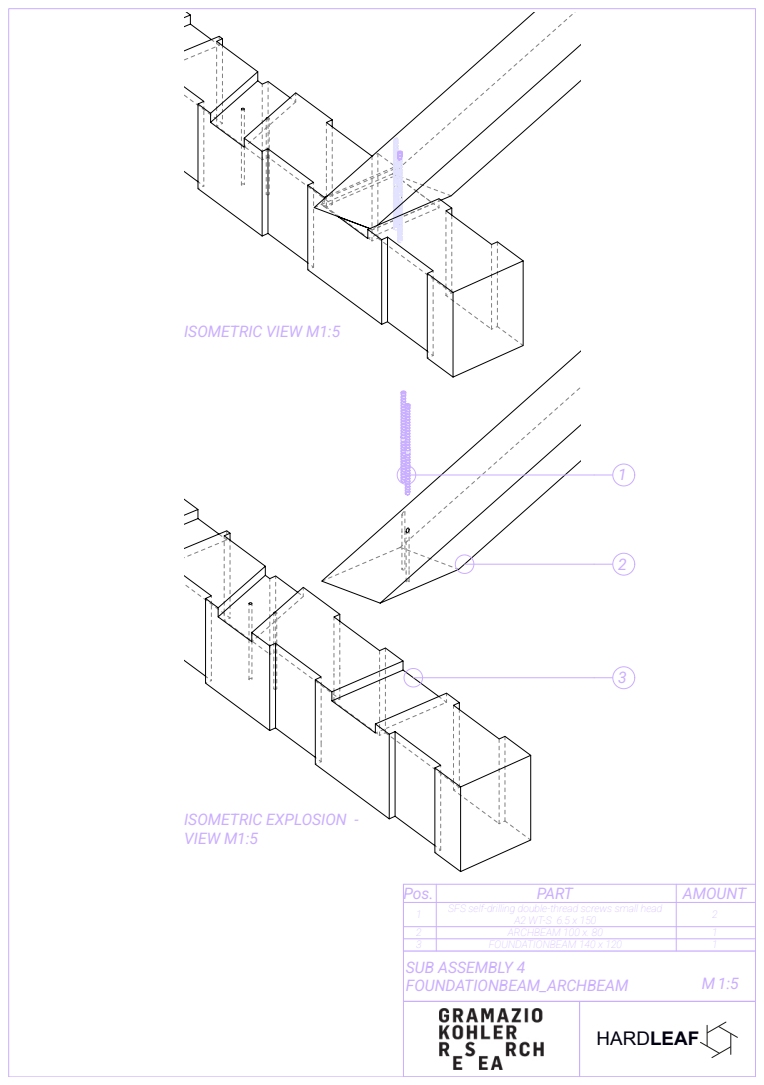
[picture p248: page 4]
FOUNDATIONBEAM_ARCHBEAM; SUB ASSEMBLY 4; PART; AMOUNT; ARCHBEAM 100 x. 80; FOUNDATIONBEAM 140 x 120; Pos.; ISOMETRIC EXPLOSION - VIEW M1:5; ISOMETRIC VIEW M1:5

SFS self-drilling double-thread screws small head

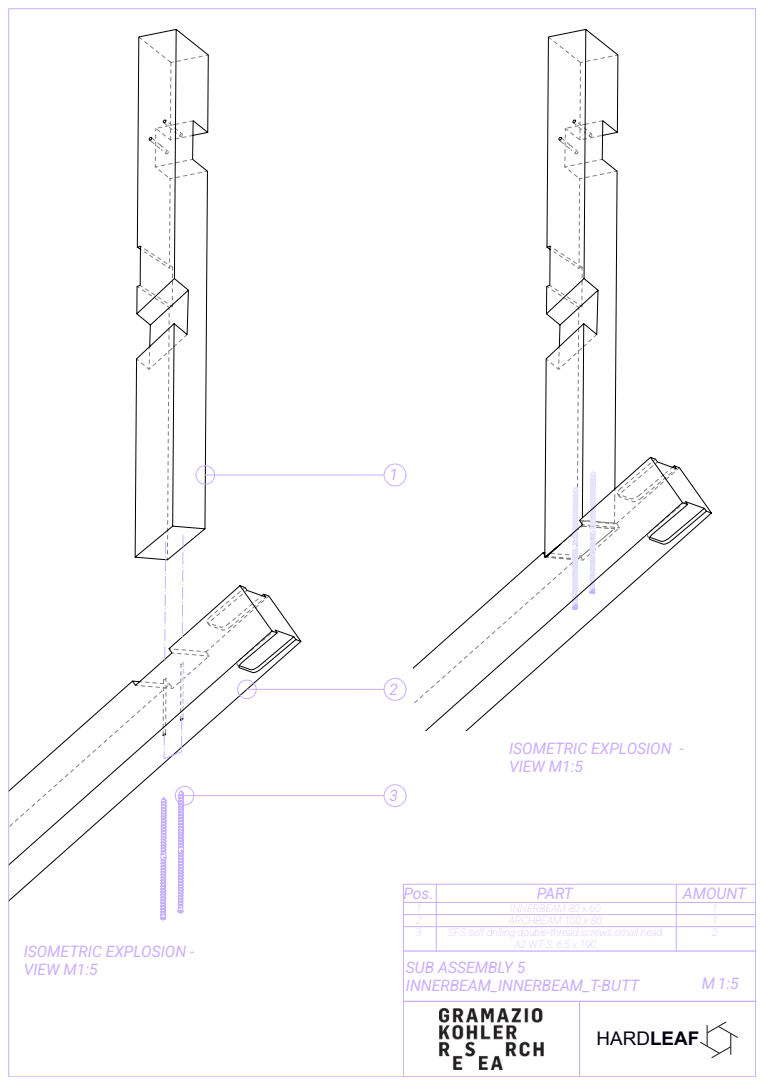
[picture p249: page 5]
INNERBEAM_INNERBEAM_T-BUTT; PART; AMOUNT; ARCHBEAM 100 x 80; INNERBEAM 80 x 60; ISOMETRIC EXPLOSION - VIEW M1:5

Pos.
SFS self-drilling double-thread screws small head
SUB ASSEMBLY 5

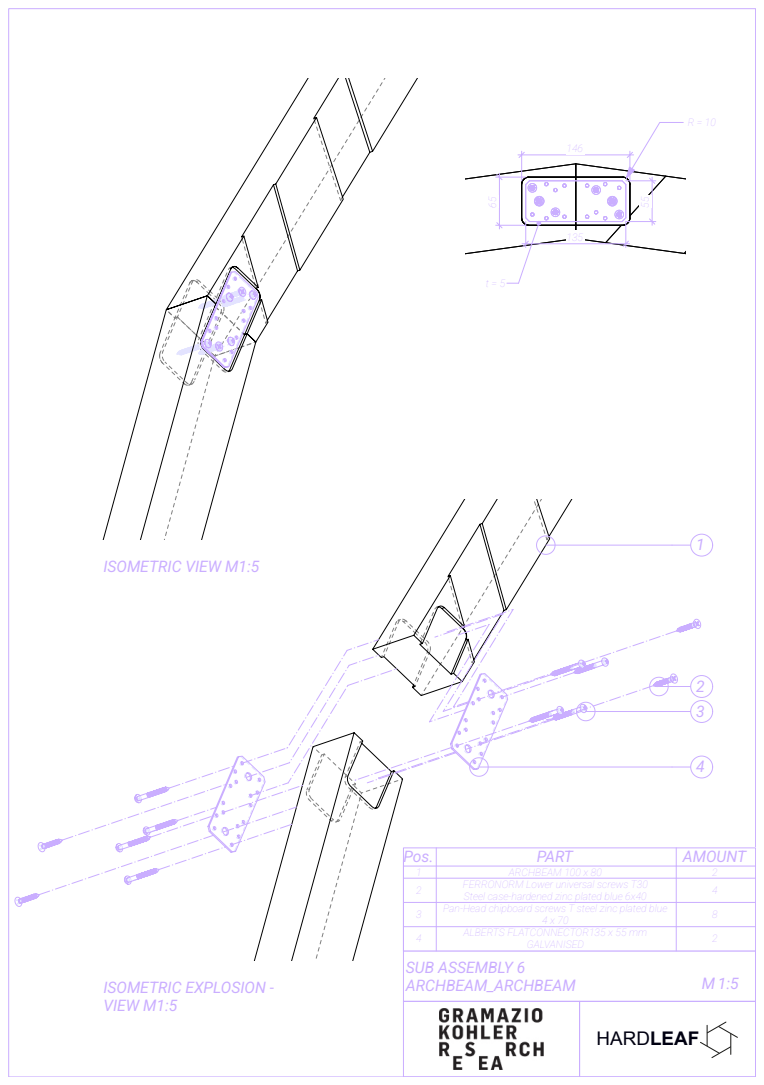
[picture p250: page 6]
ARCHBEAM_ARCHBEAM; PART; AMOUNT; Steel case-hardened zinc plated blue 6x40; ARCHBEAM 100 x 80; ALBERTS FLATCONNECTOR135 x 55 mm; GALVANISED 4; ISOMETRIC VIEW M1:5; ISOMETRIC EXPLOSION - VIEW M1:5

Pos.
Pan-Head chipboard screws T steel zinc plated blue
SUB ASSEMBLY 6

FERRONORM Lower universal screws T30

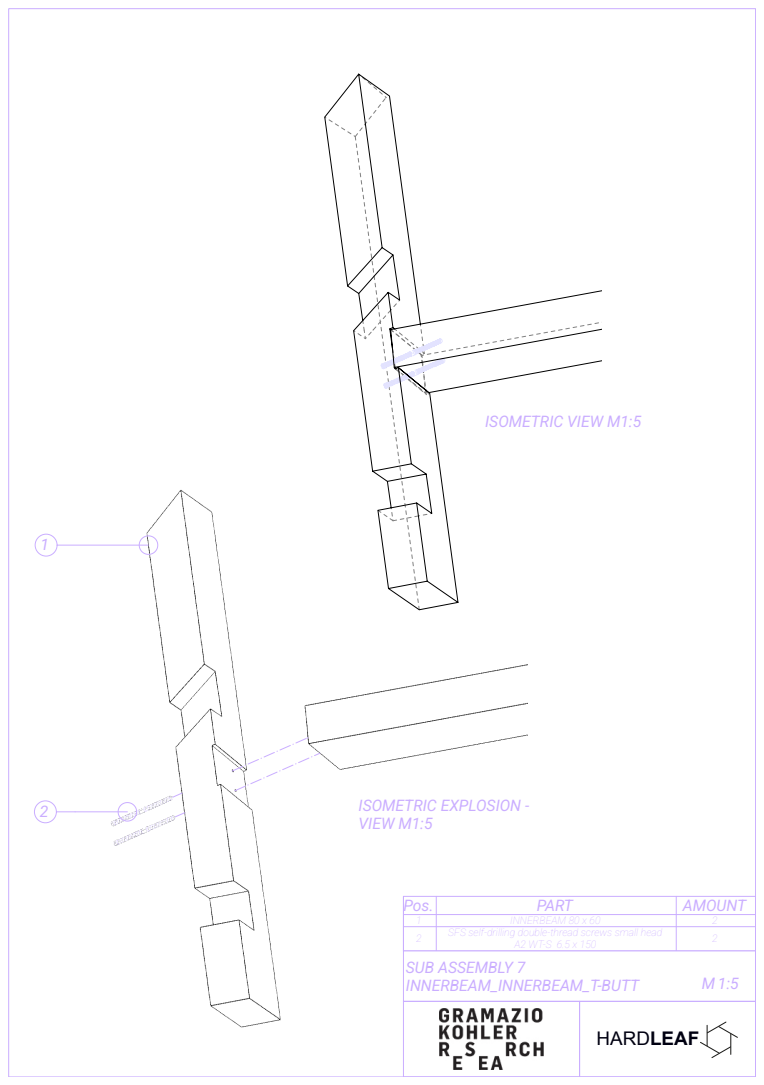
[picture p251: page 7]
PART; AMOUNT; INNERBEAM 80 x 60; INNERBEAM_INNERBEAM_T-BUTT; ISOMETRIC VIEW M1:5; ISOMETRIC EXPLOSION - VIEW M1:5

Pos.
SFS self-drilling double-thread screws small head
SUB ASSEMBLY 7

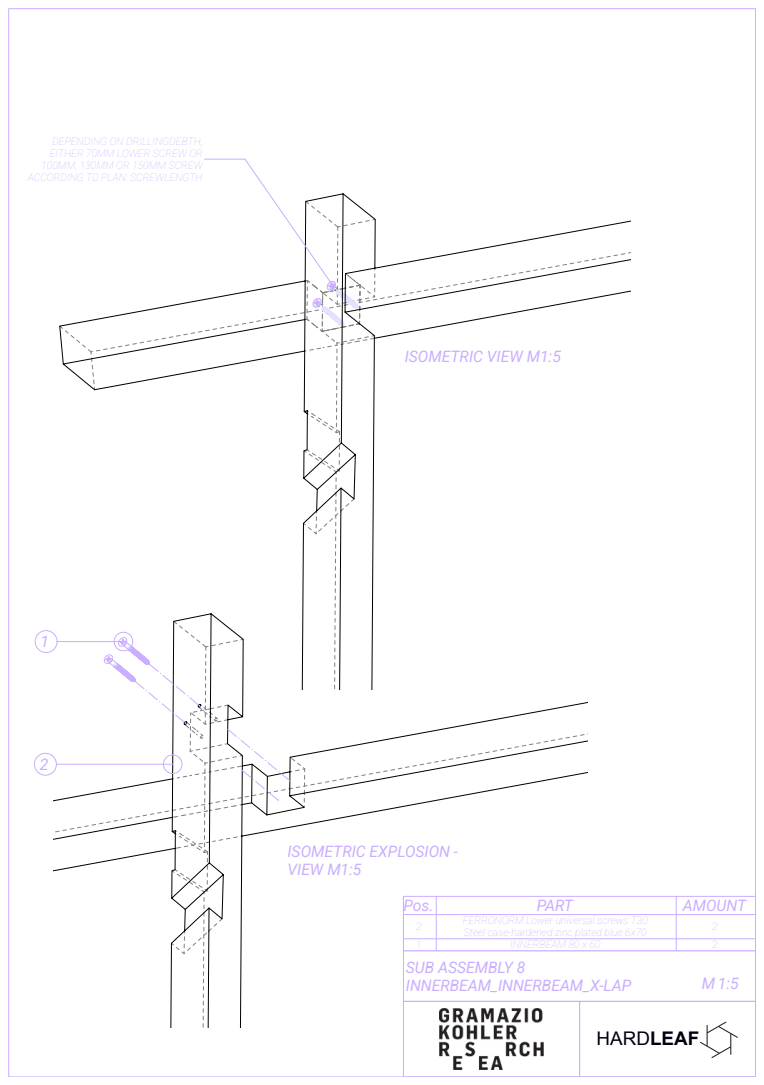
[picture p252: page 8]
PART; AMOUNT; INNERBEAM 80 x 60; Pos.; INNERBEAM_INNERBEAM_X-LAP; SUB ASSEMBLY 8; ISOMETRIC VIEW M1:5; ISOMETRIC EXPLOSION - VIEW M1:5

DEPENDING ON DRILLINGDEBTH,
EITHER 70MM LOWER SCREW OR
100MM, 130MM OR 150MM SCREW
ACCORDING TO PLAN: SCREWLENGTH

FERRONORM Lower universal screws T30
Steel case-hardened zinc plated blue 6x70
