gramaziokohler/coding_architecture_fs26_focus_work/Dokumentation/Group A/Booklet_focuswork_2406 Folder/Links/oberbaugruppe.pdf

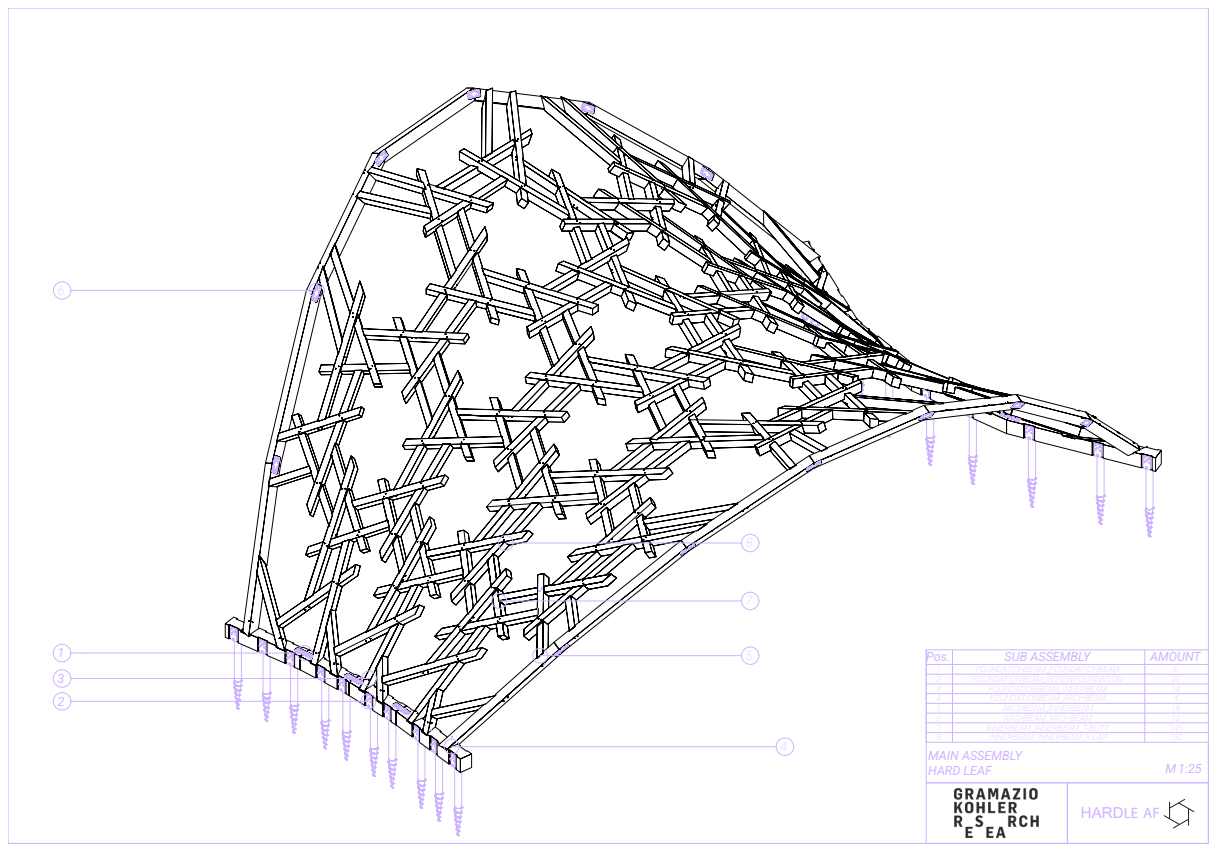
[picture p258: page 1]
HARD LEAF; MAIN ASSEMB; HAR; SUB ASSEMB; AMOU; FOU; Pos. 12345678
