gramaziokohler/coding_architecture_fs26_focus_work/Dokumentation/Group A/Booklet_focuswork_2406 Folder/Links/stupid_floorplan.pdf

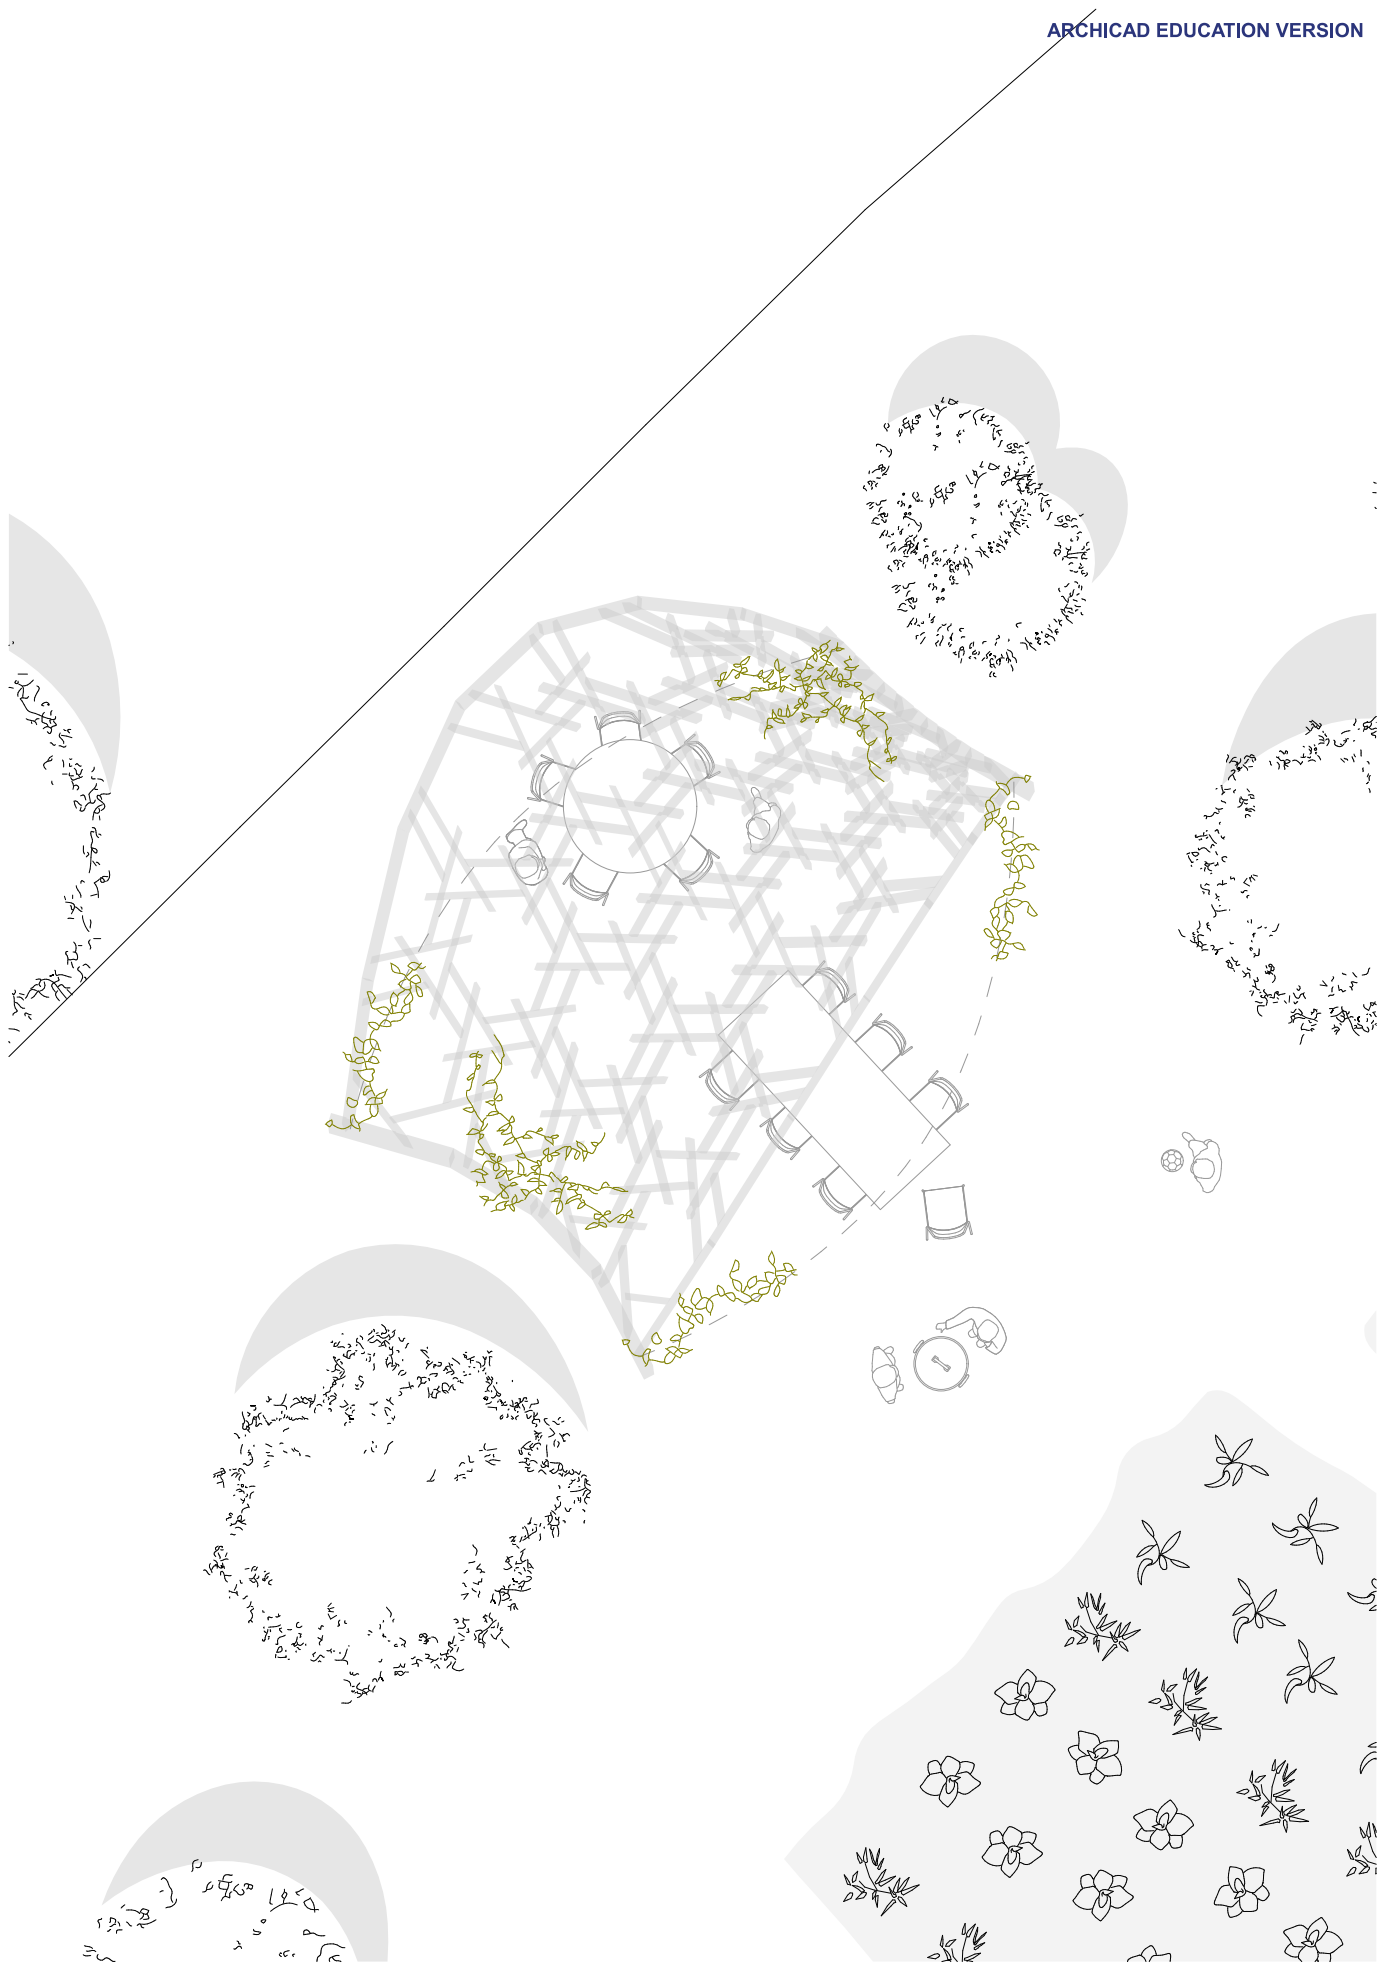
[picture p259: page 1]
GSEducationalVersion
